geerlingguy/pi4gpu/PCIe bracket/PCIe_bracket_M3_hole.png

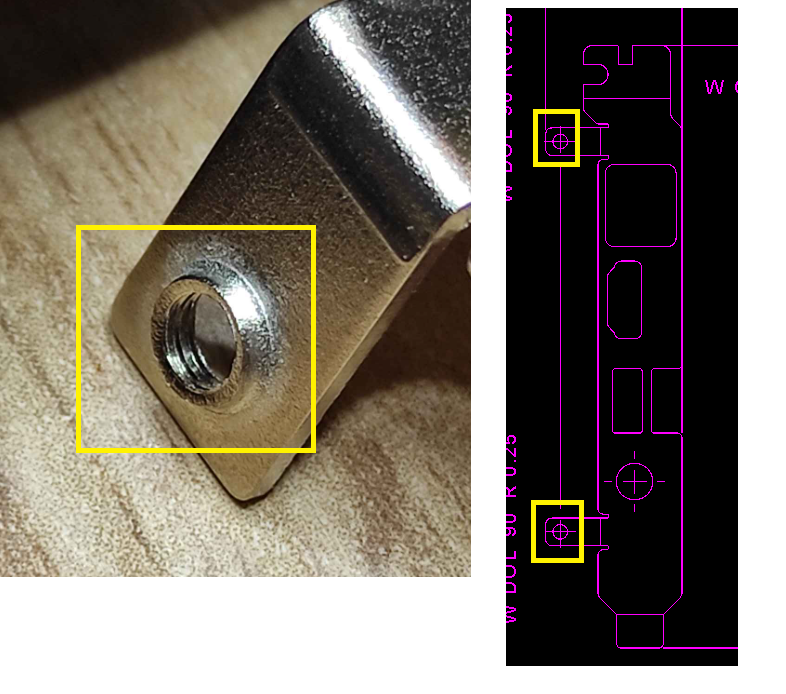
PCIe bracket/PCIe_bracket_M3_hole.png
