geerlingguy/pi4gpu/PCIe bracket/PCIe_missing_bending.png

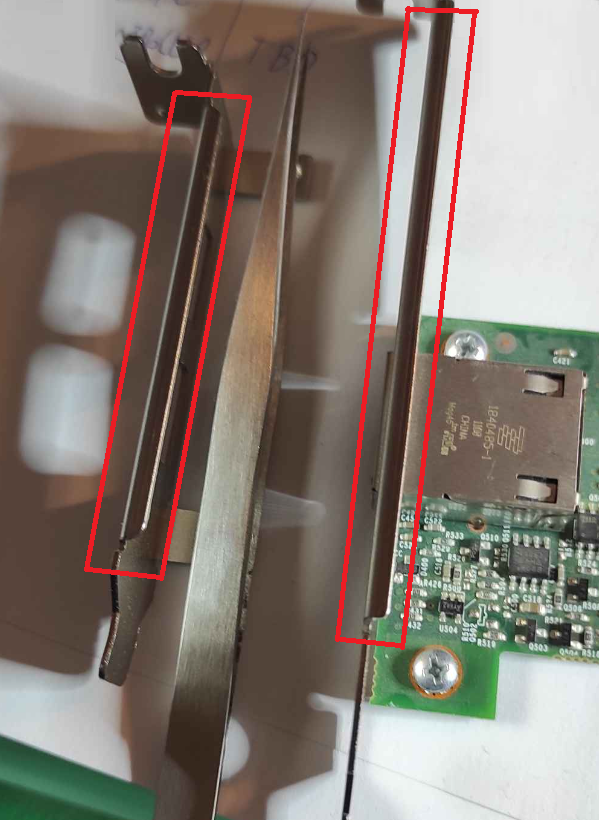
PCIe bracket/PCIe_missing_bending.png
