geerlingguy/pi4gpu/PCIe bracket/photo_2022-12-15_10-46-20.jpg

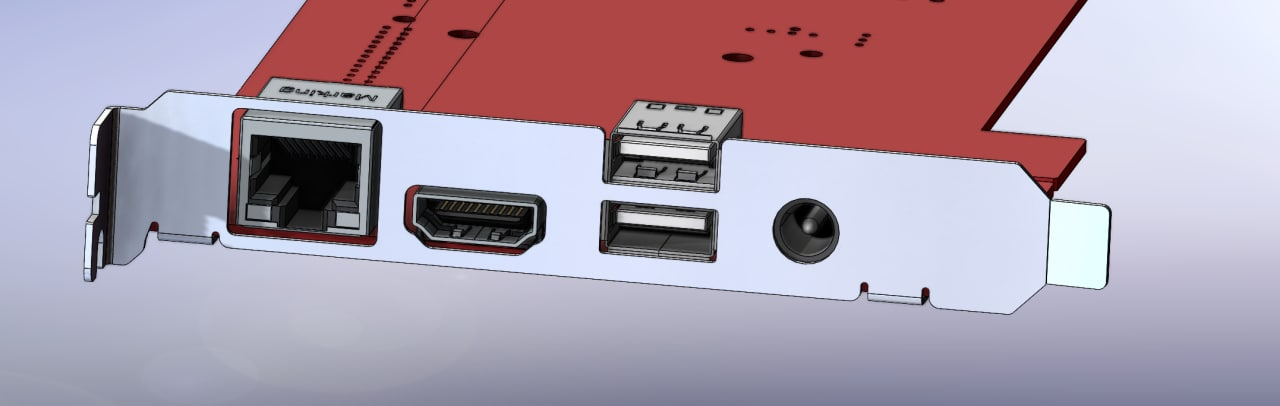
PCIe bracket/photo_2022-12-15_10-46-20.jpg
