geerlingguy/pi4gpu/renders/cm4_gpu1.png

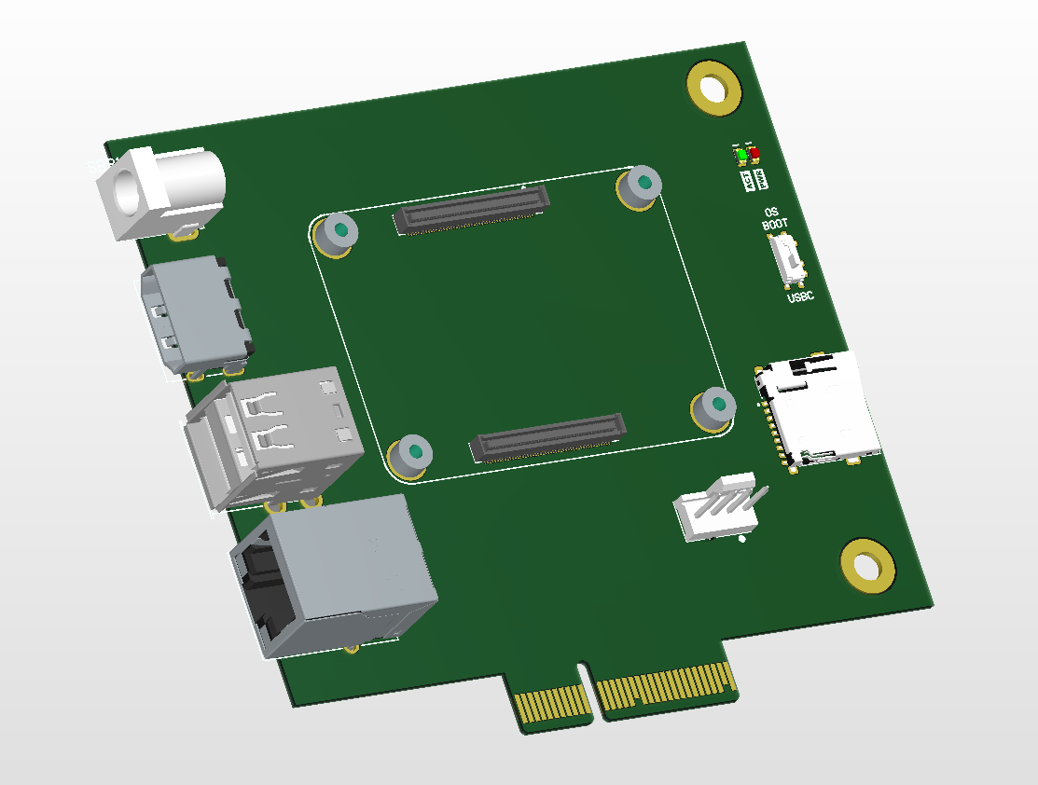
renders/cm4_gpu1.png
