geerlingguy/pi4gpu/renders/cm4_gpu2.png

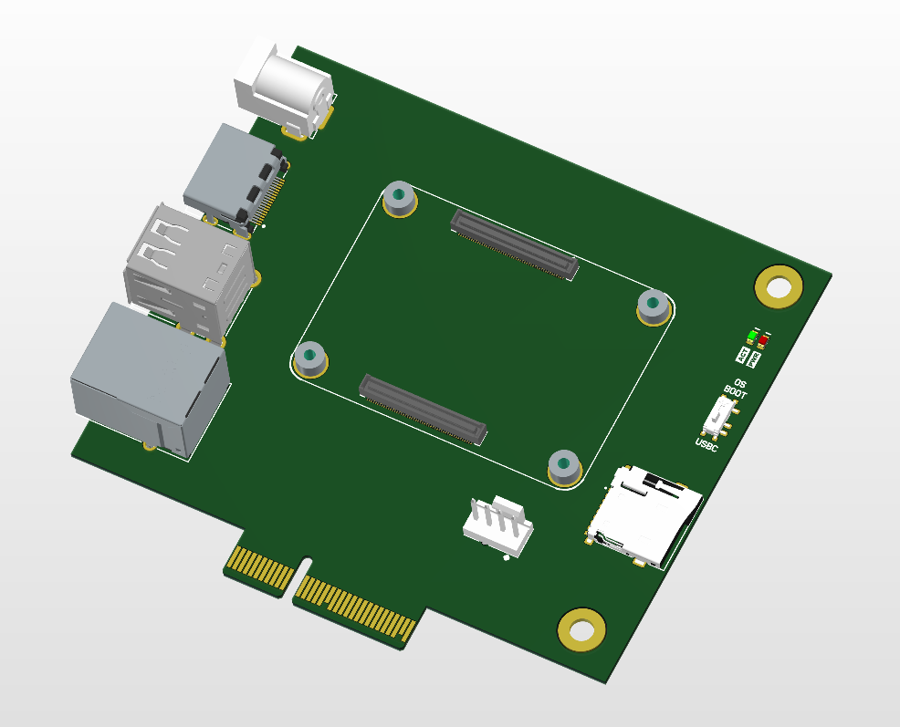
renders/cm4_gpu2.png
