geerlingguy/pi4gpu/renders/CM4GPU_PCB_20221031_01.png

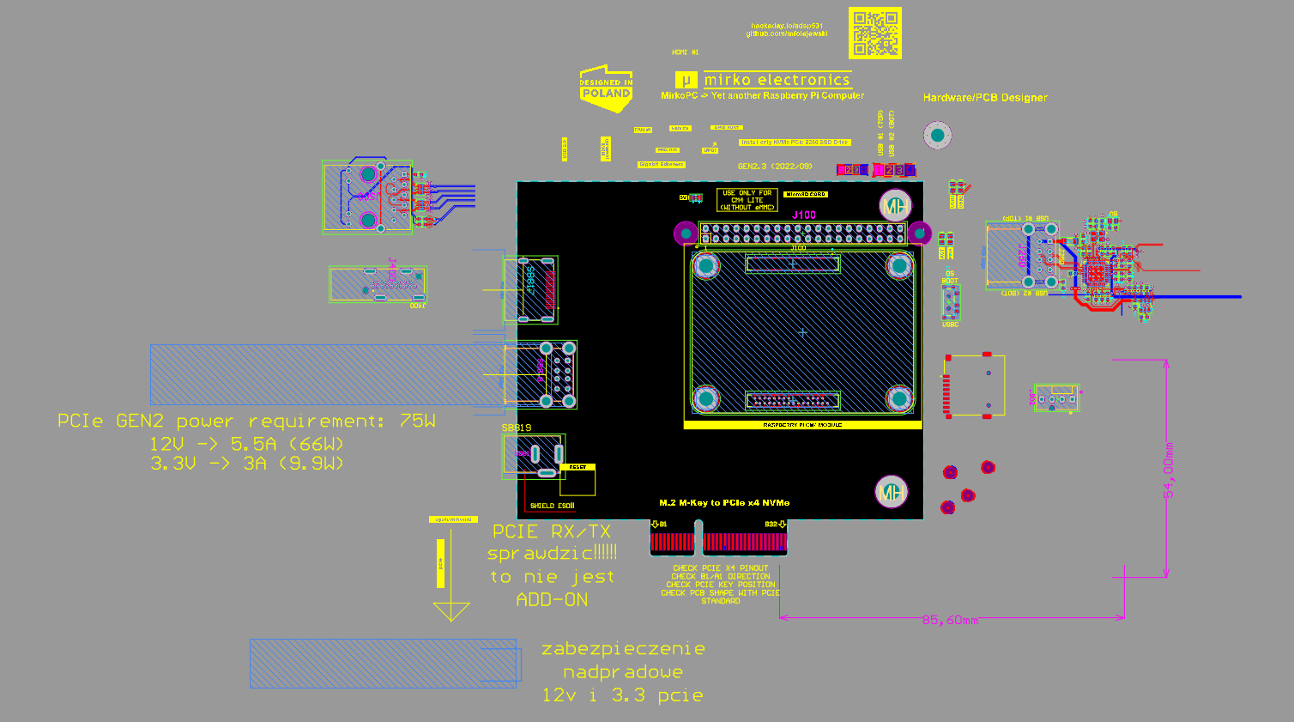
renders/CM4GPU_PCB_20221031_01.png
