geerlingguy/pi4gpu/renders/CM4GPU_PCB_20221103_01.png

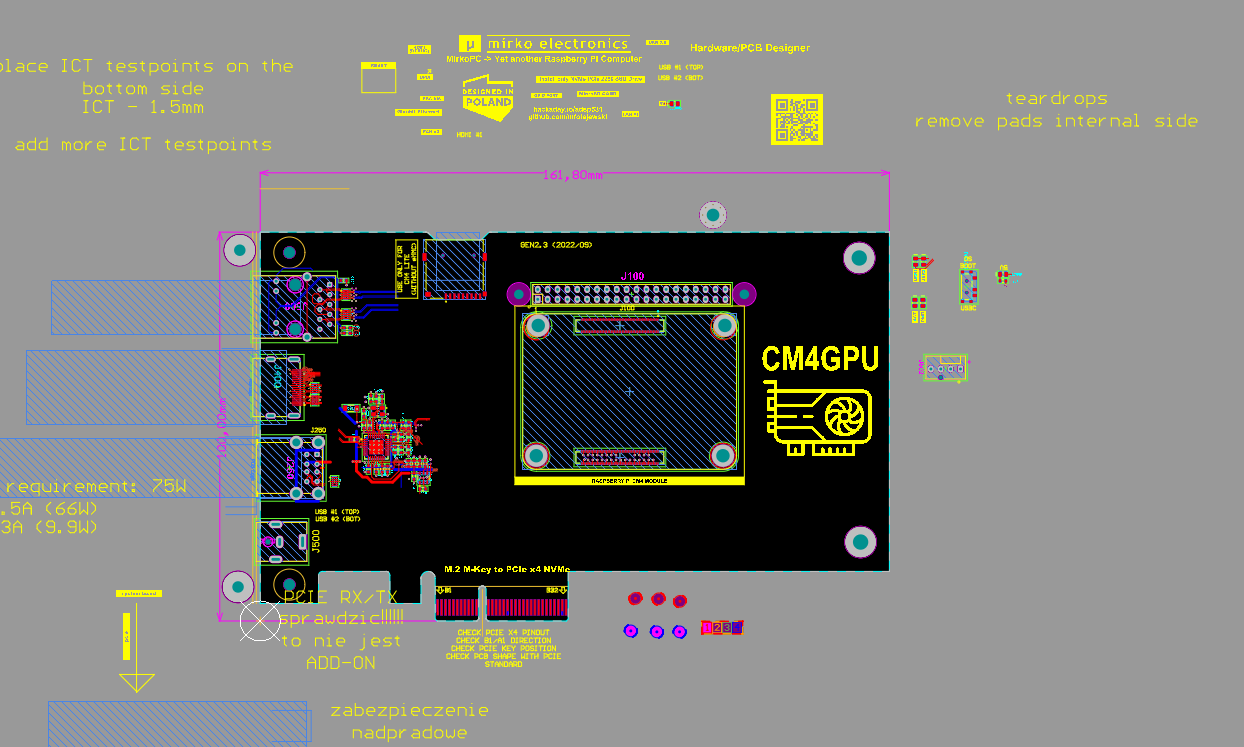
renders/CM4GPU_PCB_20221103_01.png
