geerlingguy/pi4gpu/renders/CM4GPU_PCB_20221110_01.png

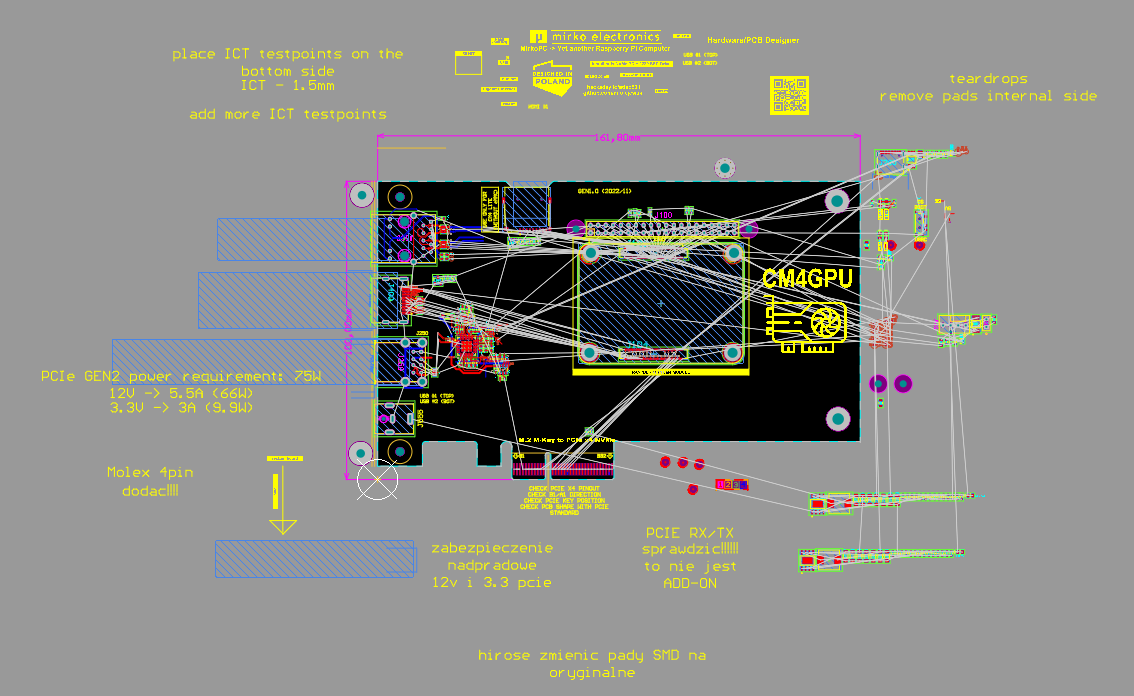
renders/CM4GPU_PCB_20221110_01.png
