geerlingguy/pi4gpu/renders/CM4GPU_PCB_20221114_04.png

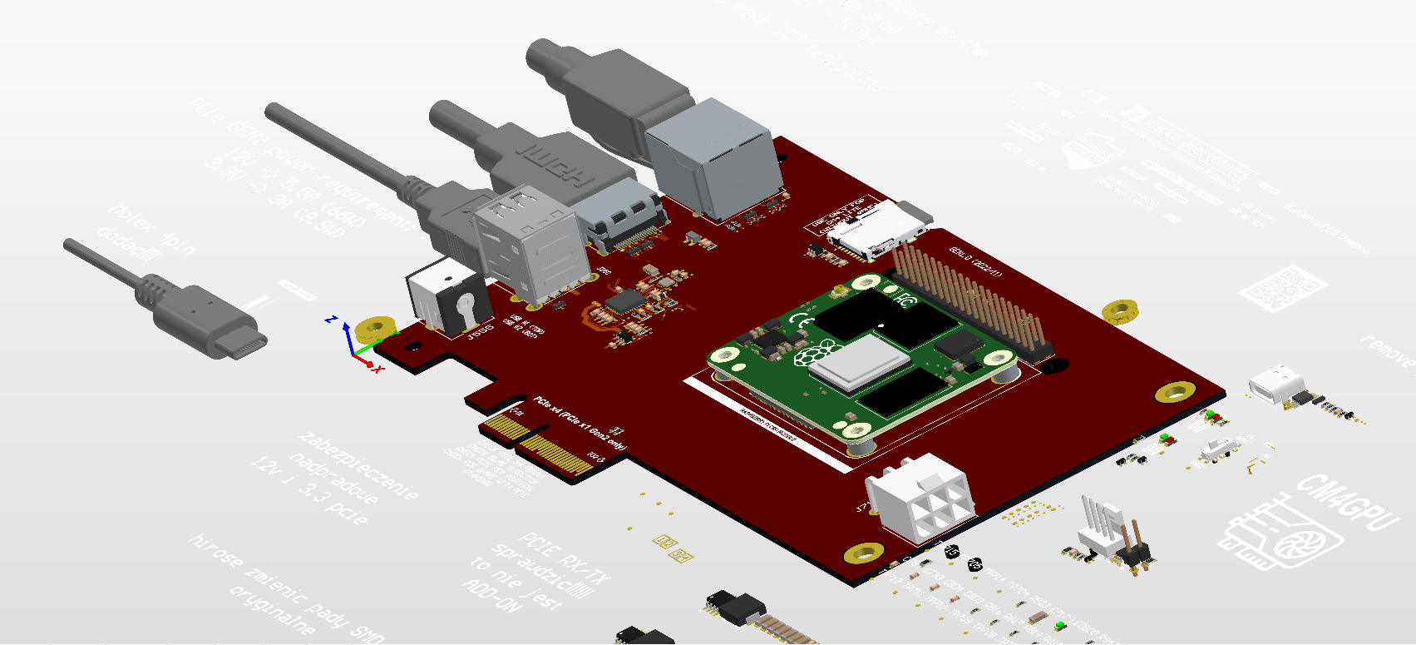
renders/CM4GPU_PCB_20221114_04.png
