geerlingguy/pi4gpu/renders/CM4GPU_PCB_20221117_03.png

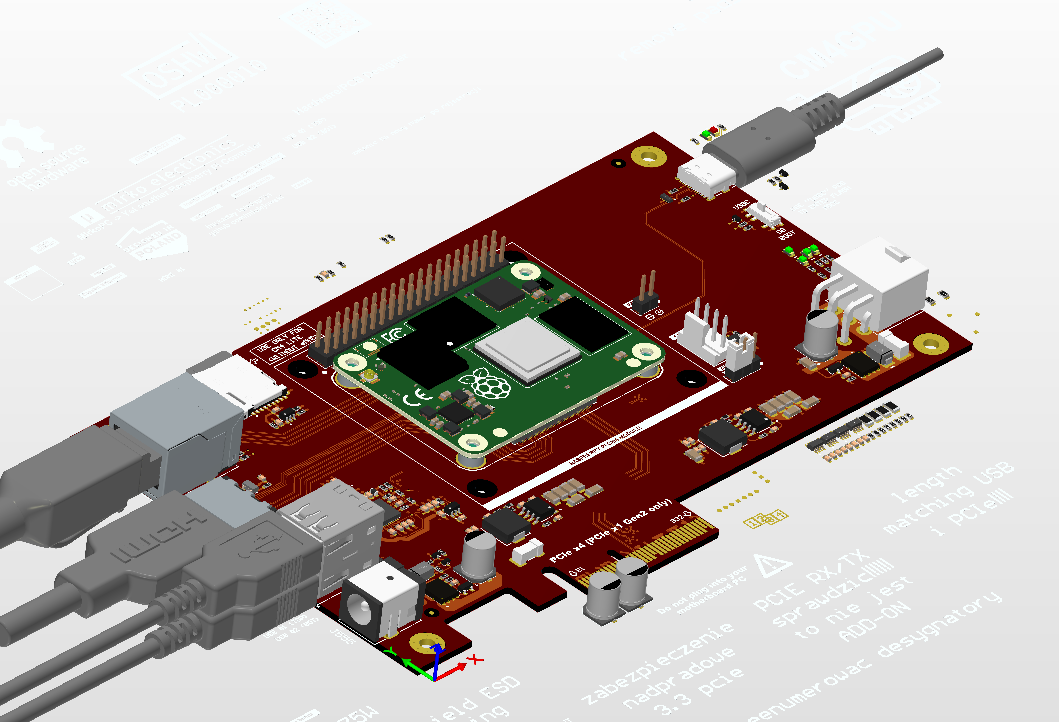
renders/CM4GPU_PCB_20221117_03.png
