geerlingguy/pi4gpu/renders/PCIE_adapter2.png

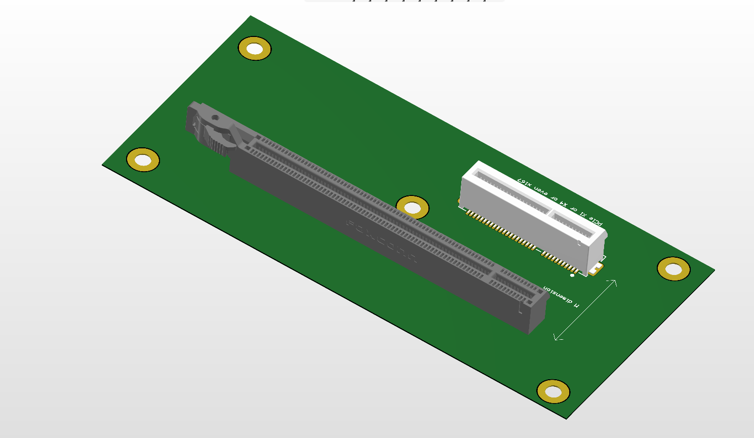
renders/PCIE_adapter2.png
