geerlingguy/pi4gpu/renders/PCIe_X4_X16_ADP_2.png

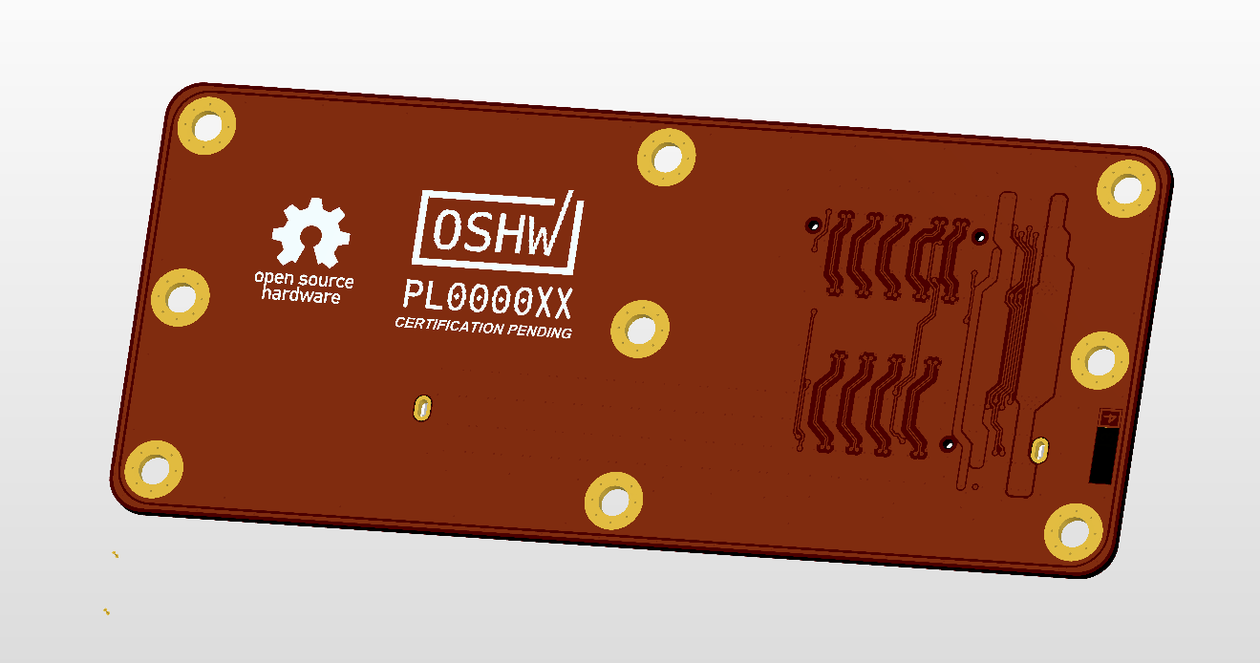
renders/PCIe_X4_X16_ADP_2.png
