geerlingguy/pi4gpu/renders/PCIe_X4_X16_ADP_4.png

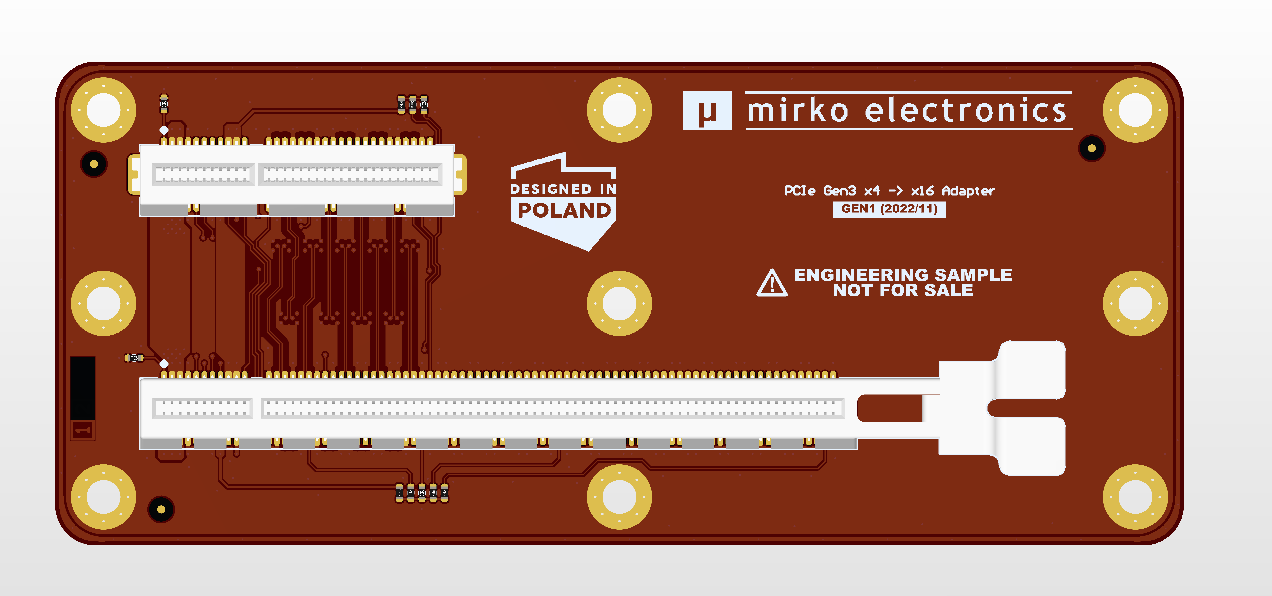
renders/PCIe_X4_X16_ADP_4.png
