geerlingguy/pi4gpu/renders/PCIe_X4_X16_ADP_5.png

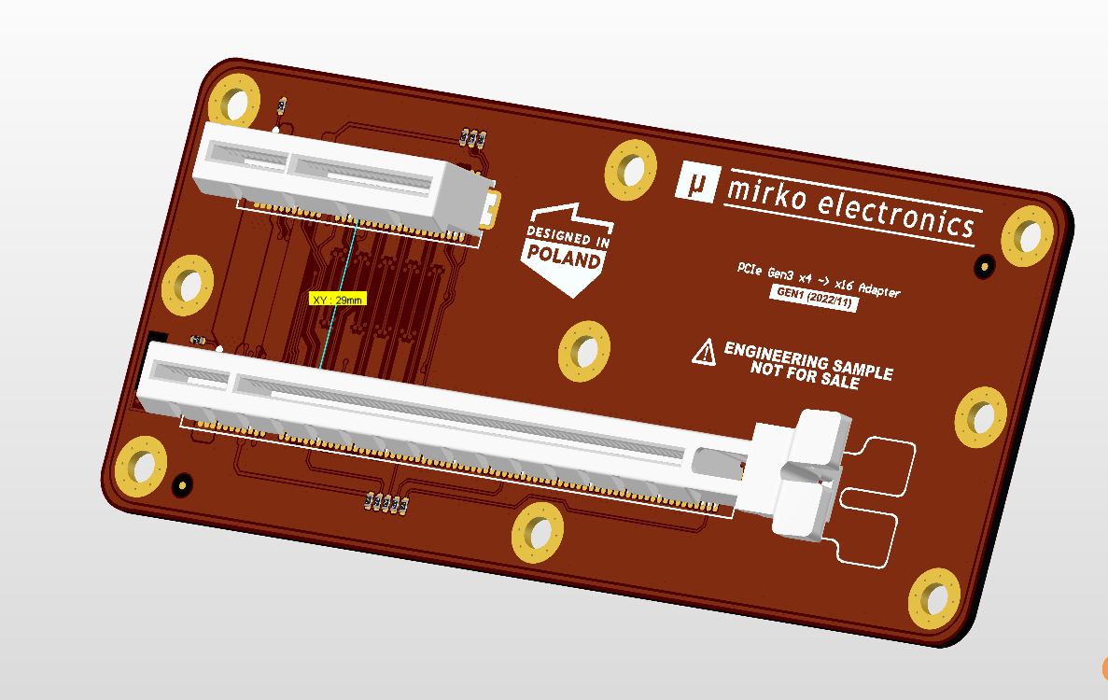
renders/PCIe_X4_X16_ADP_5.png
