geerlingguy/pi4gpu/renders/Pi4GPU_2022-11-21_4.png

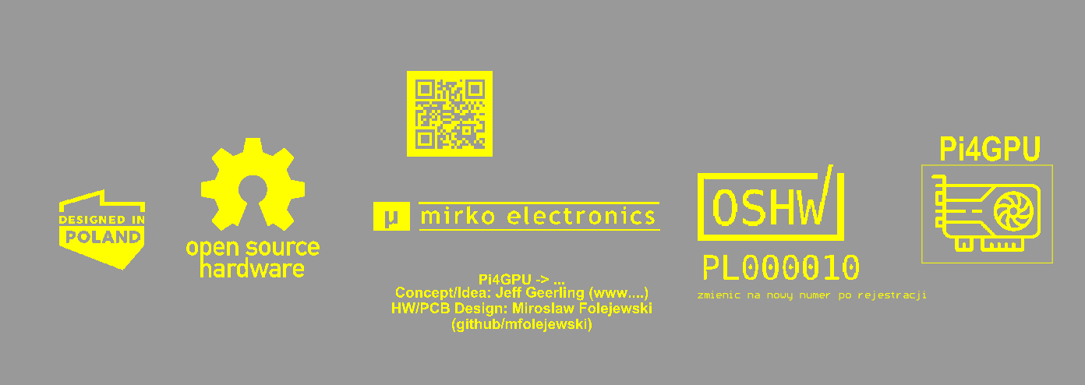
renders/Pi4GPU_2022-11-21_4.png
