geerlingguy/pi4gpu/renders/Pi4GPU_2022-11-23_2.png

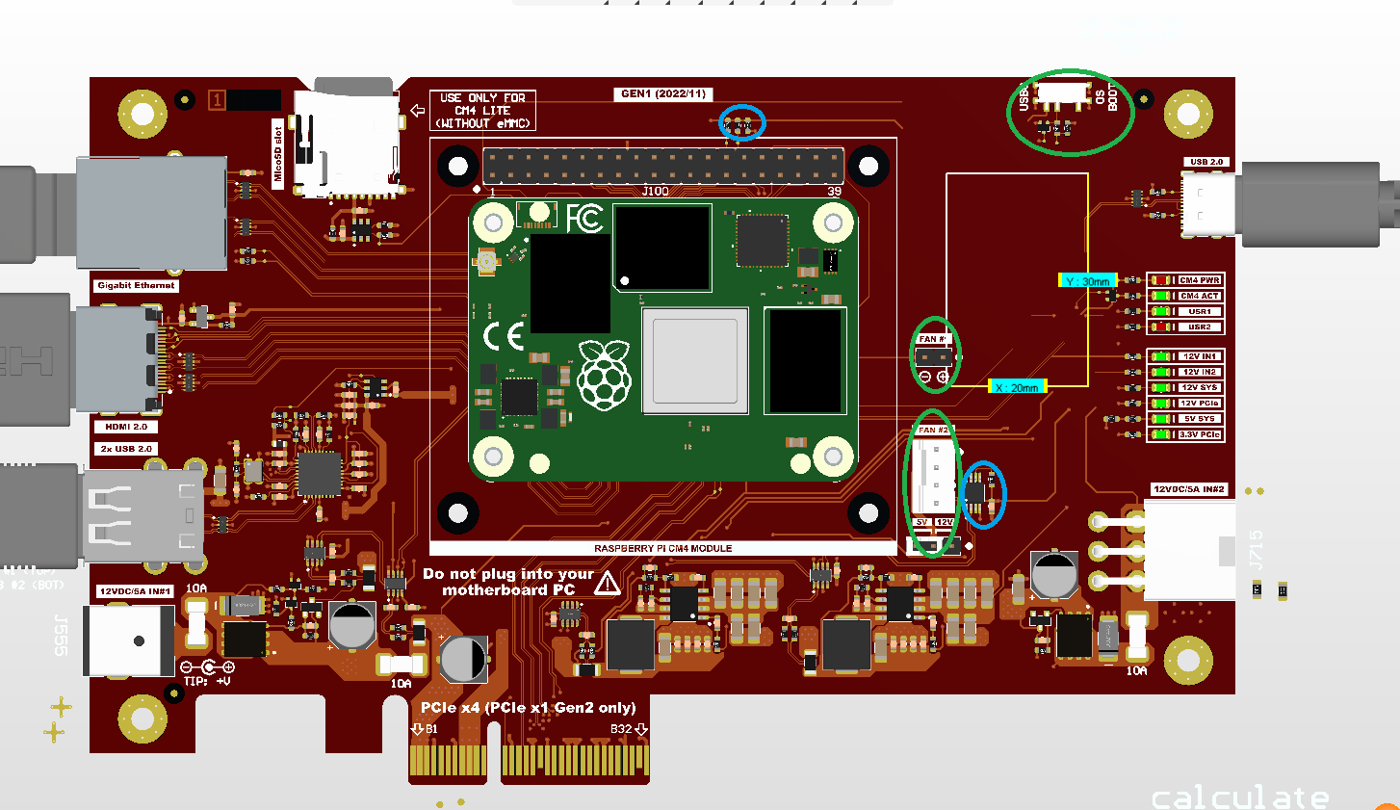
renders/Pi4GPU_2022-11-23_2.png
