geerlingguy/pi4gpu/renders/Pi4GPU_2022-11-24_7.png

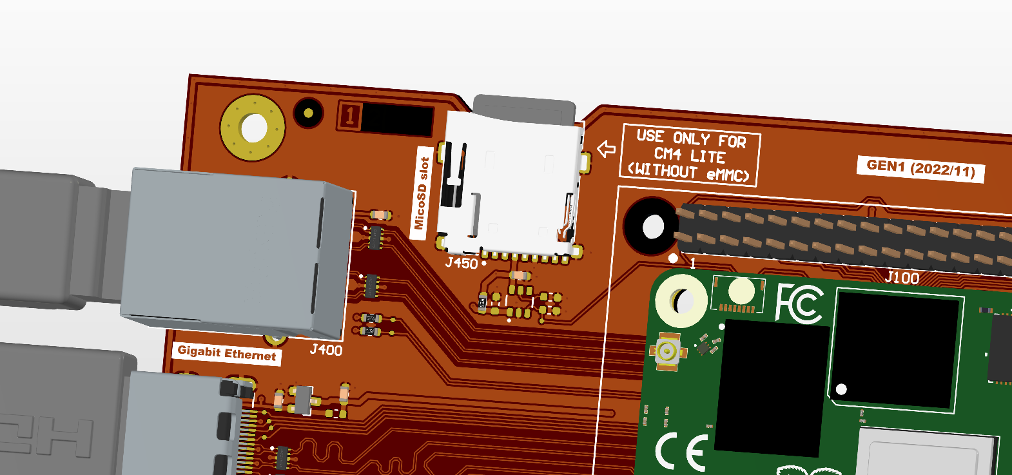
renders/Pi4GPU_2022-11-24_7.png
