geerlingguy/pi4gpu/renders/Pi4GPU_2022-11-29_1.png

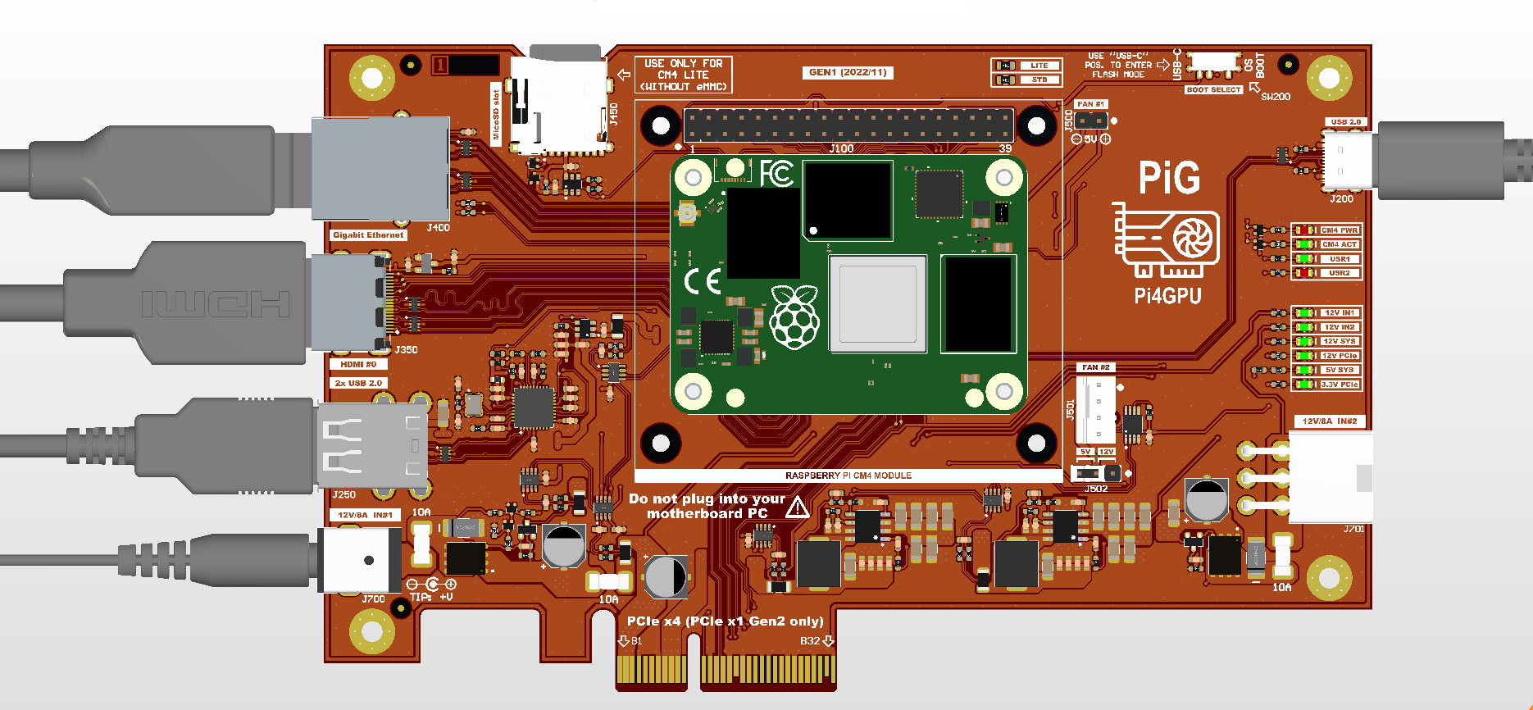
renders/Pi4GPU_2022-11-29_1.png
