geerlingguy/pi4gpu/renders/Pi4GPU_2022-11-29_6.png

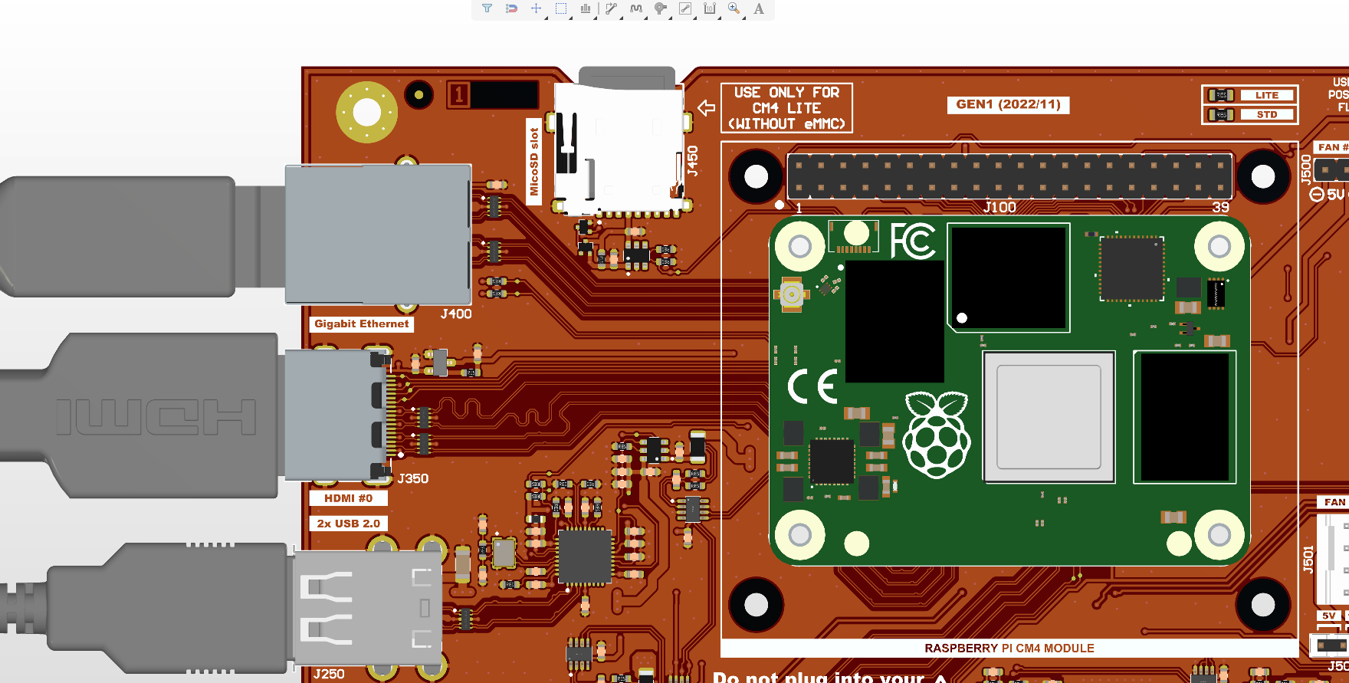
renders/Pi4GPU_2022-11-29_6.png
