geerlingguy/pi4gpu/renders/Pi4GPU_2022-12-03_1.png

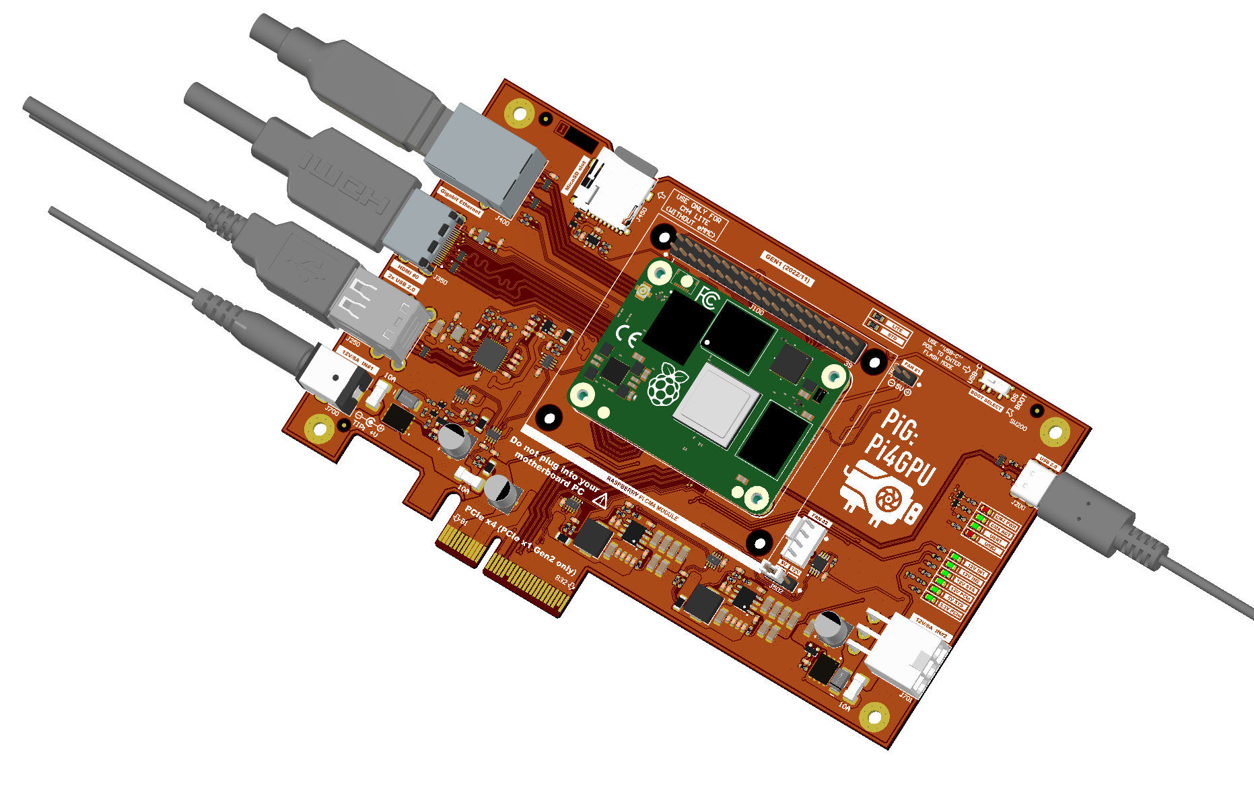
renders/Pi4GPU_2022-12-03_1.png
