geerlingguy/pi4gpu/renders/Pi4GPU_v2_2023-04-13_2.png

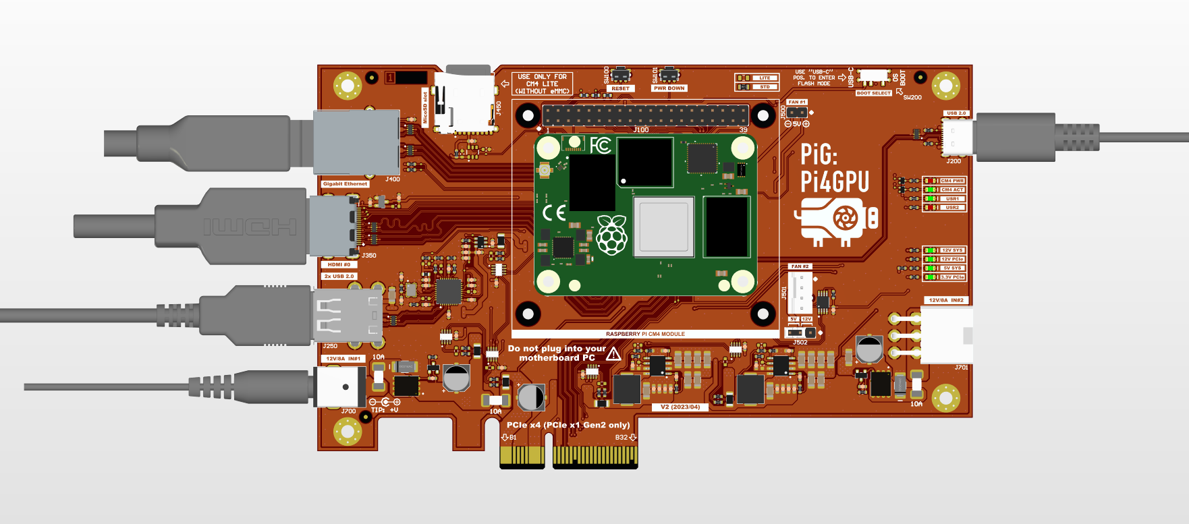
renders/Pi4GPU_v2_2023-04-13_2.png
