geerlingguy/pi4gpu/renders/Pi4GPU_v2_2023-04-13_4.png

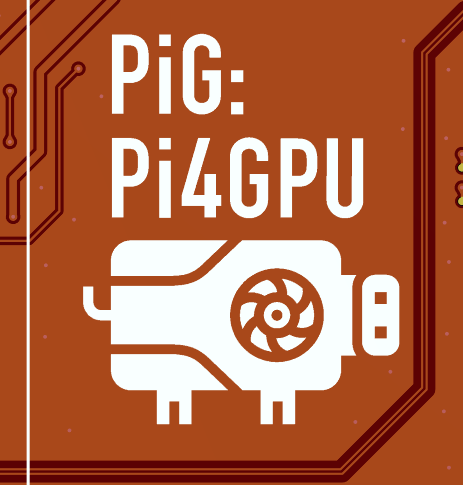
renders/Pi4GPU_v2_2023-04-13_4.png
