geerlingguy/pi4gpu/source files (PCB)/v2/pcb_stackup.png

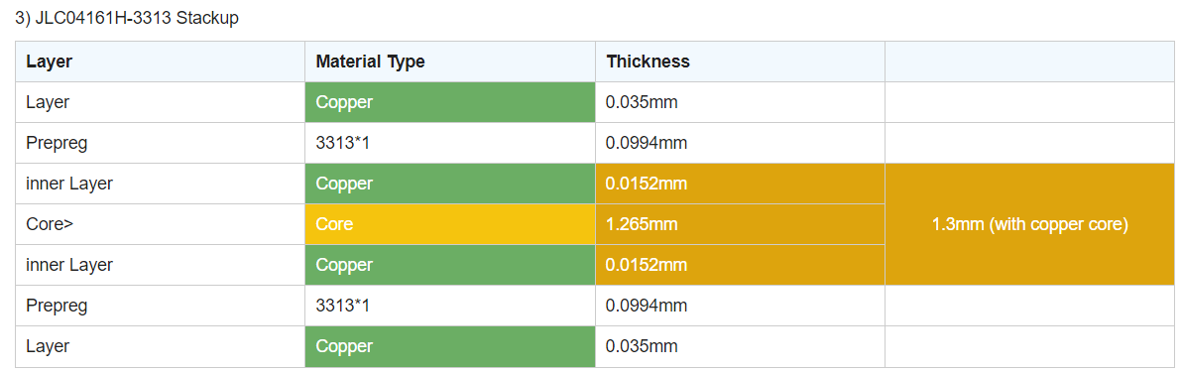
source files (PCB)/v2/pcb_stackup.png
