geerlingguy/pi4gpu/issues/HW_PCB_issues_v1.png

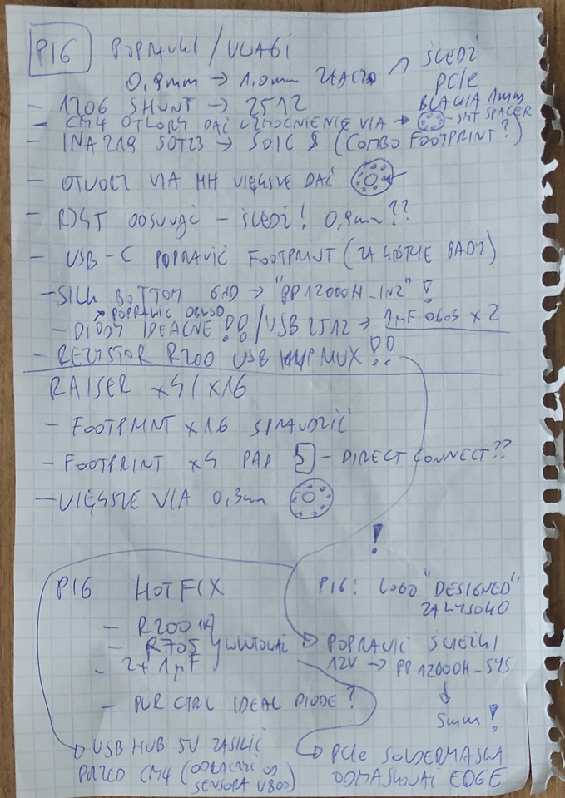
issues/HW_PCB_issues_v1.png
