geerlingguy/pi4gpu/schematics/deprecated/Pi4GPU_(PiG)_v1_Schematic_2022-12-03.pdf

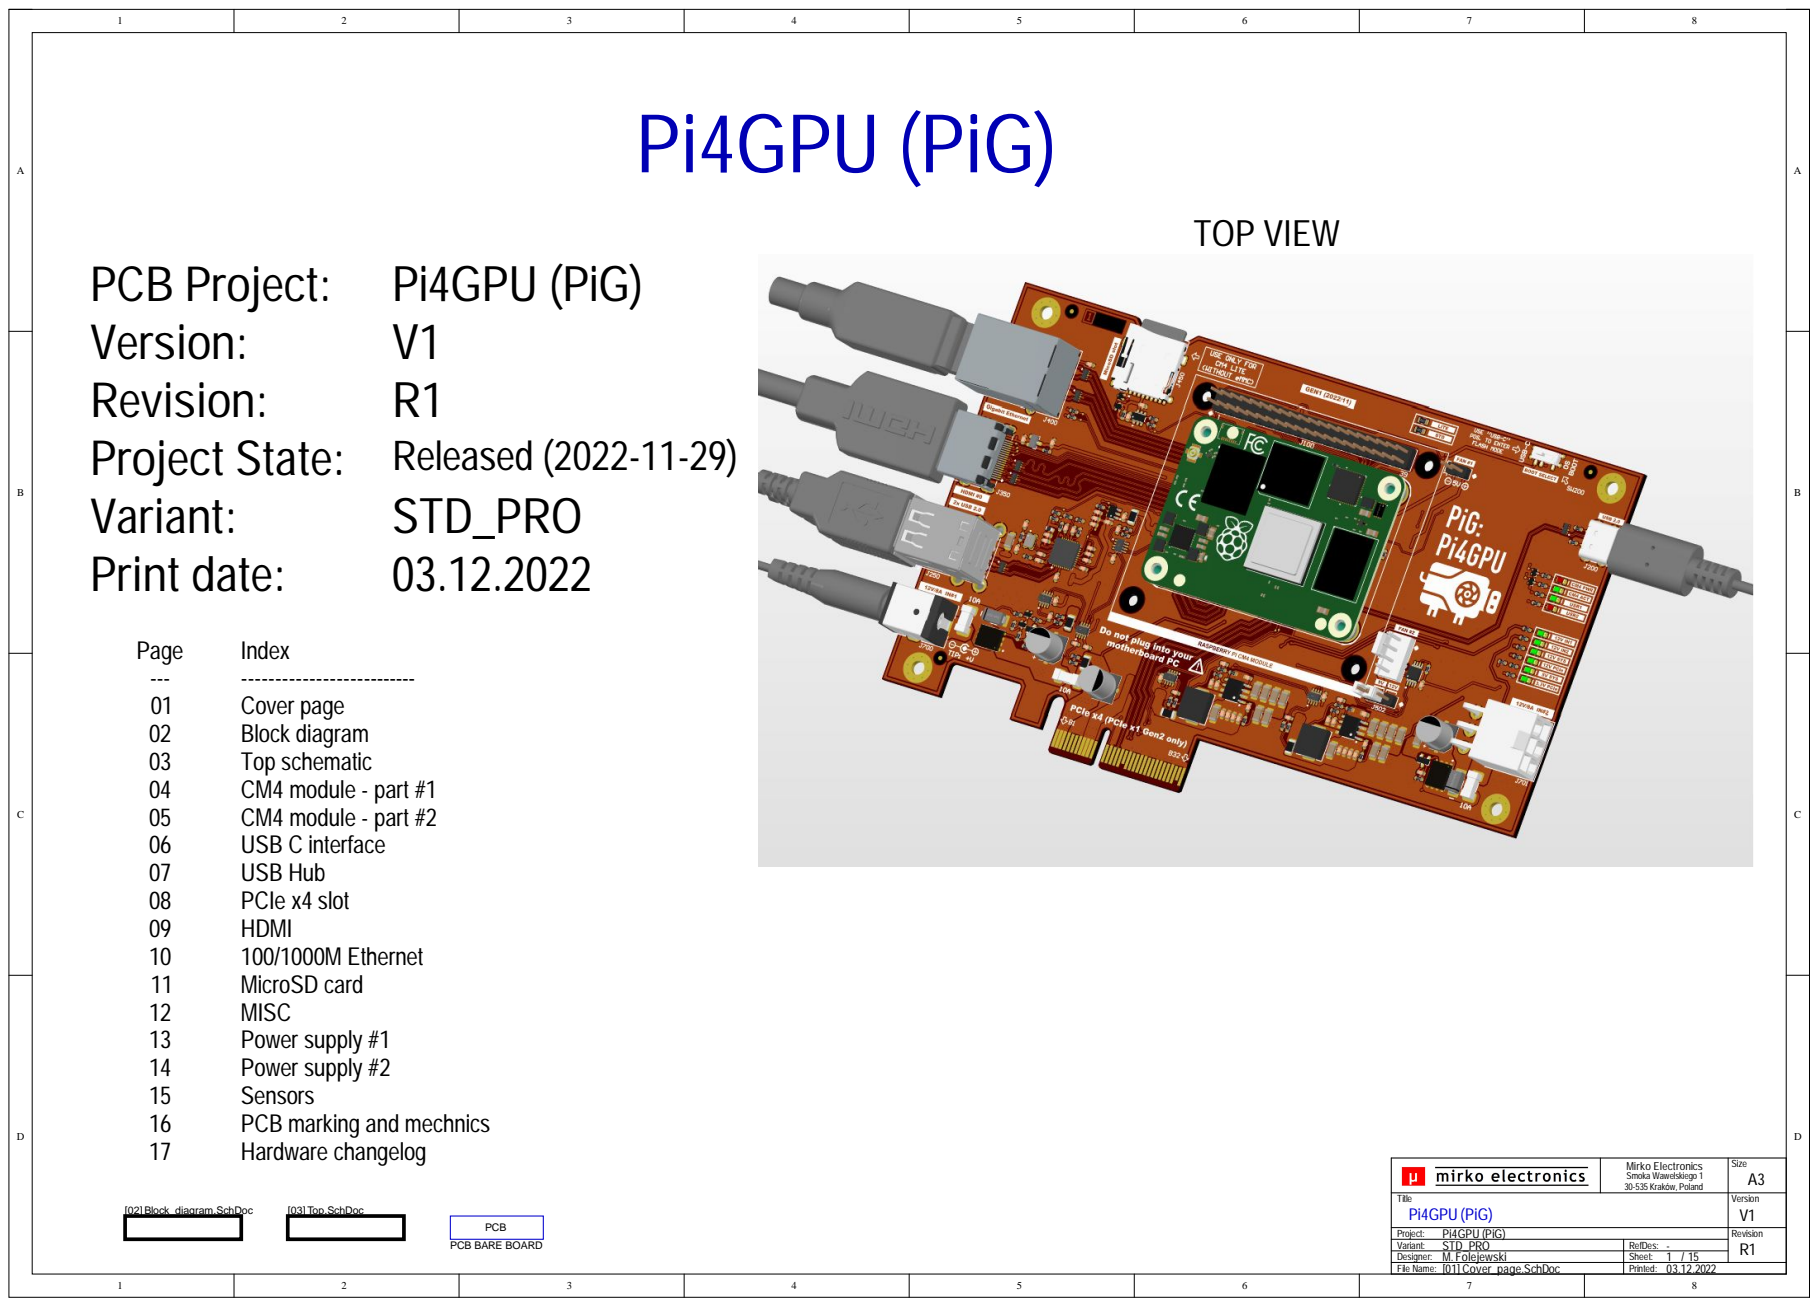
[picture p160: page 1]

Mirko Electronics Smoka Wawelskiego 1 30-535 Kraków, Poland | Size A3

Title Pi4GPU (PiG) | | Version V1

Project: Pi4GPU (PiG) | | Revision R1
Variant: STD_PRO | RefDes: -
Designer: M. Folejewski
File Name: [01] Cover_page.SchDoc | Printed:

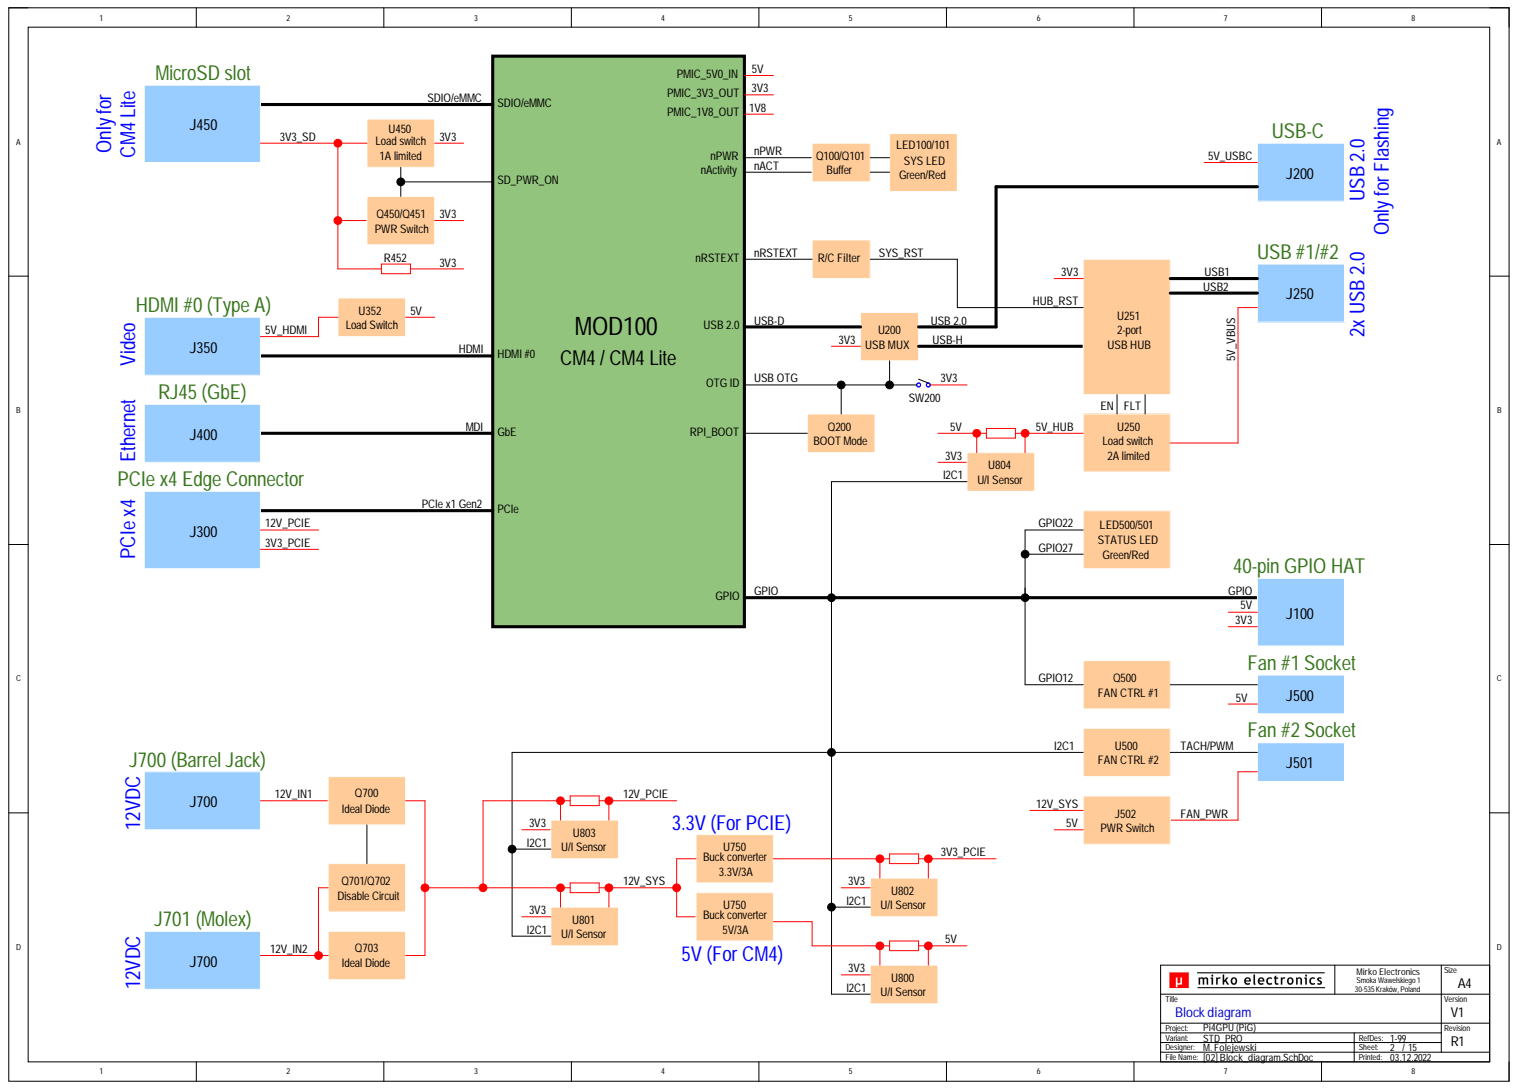
[picture p161: page 2]

SDIO/eMMC

Mirko Electronics Smoka Wawelskiego 1

Title Block diagram | Version V1

Project: Pi4GPU (PiG) | Revision R1
Variant: STD_PRO | RefDes: 1-99


Mirko Electronics Smoka Wawelskiego 1 30-535 Kraków, Poland | Size A4

Title Top schematic | | Version V1

Project: Pi4GPU (PiG) | | Revision R1
Variant: STD_PRO | RefDes: 1-99

Sheet: 3 15 /

File Name: [03] TOP.SchDoc | Printed: 03.12.2022

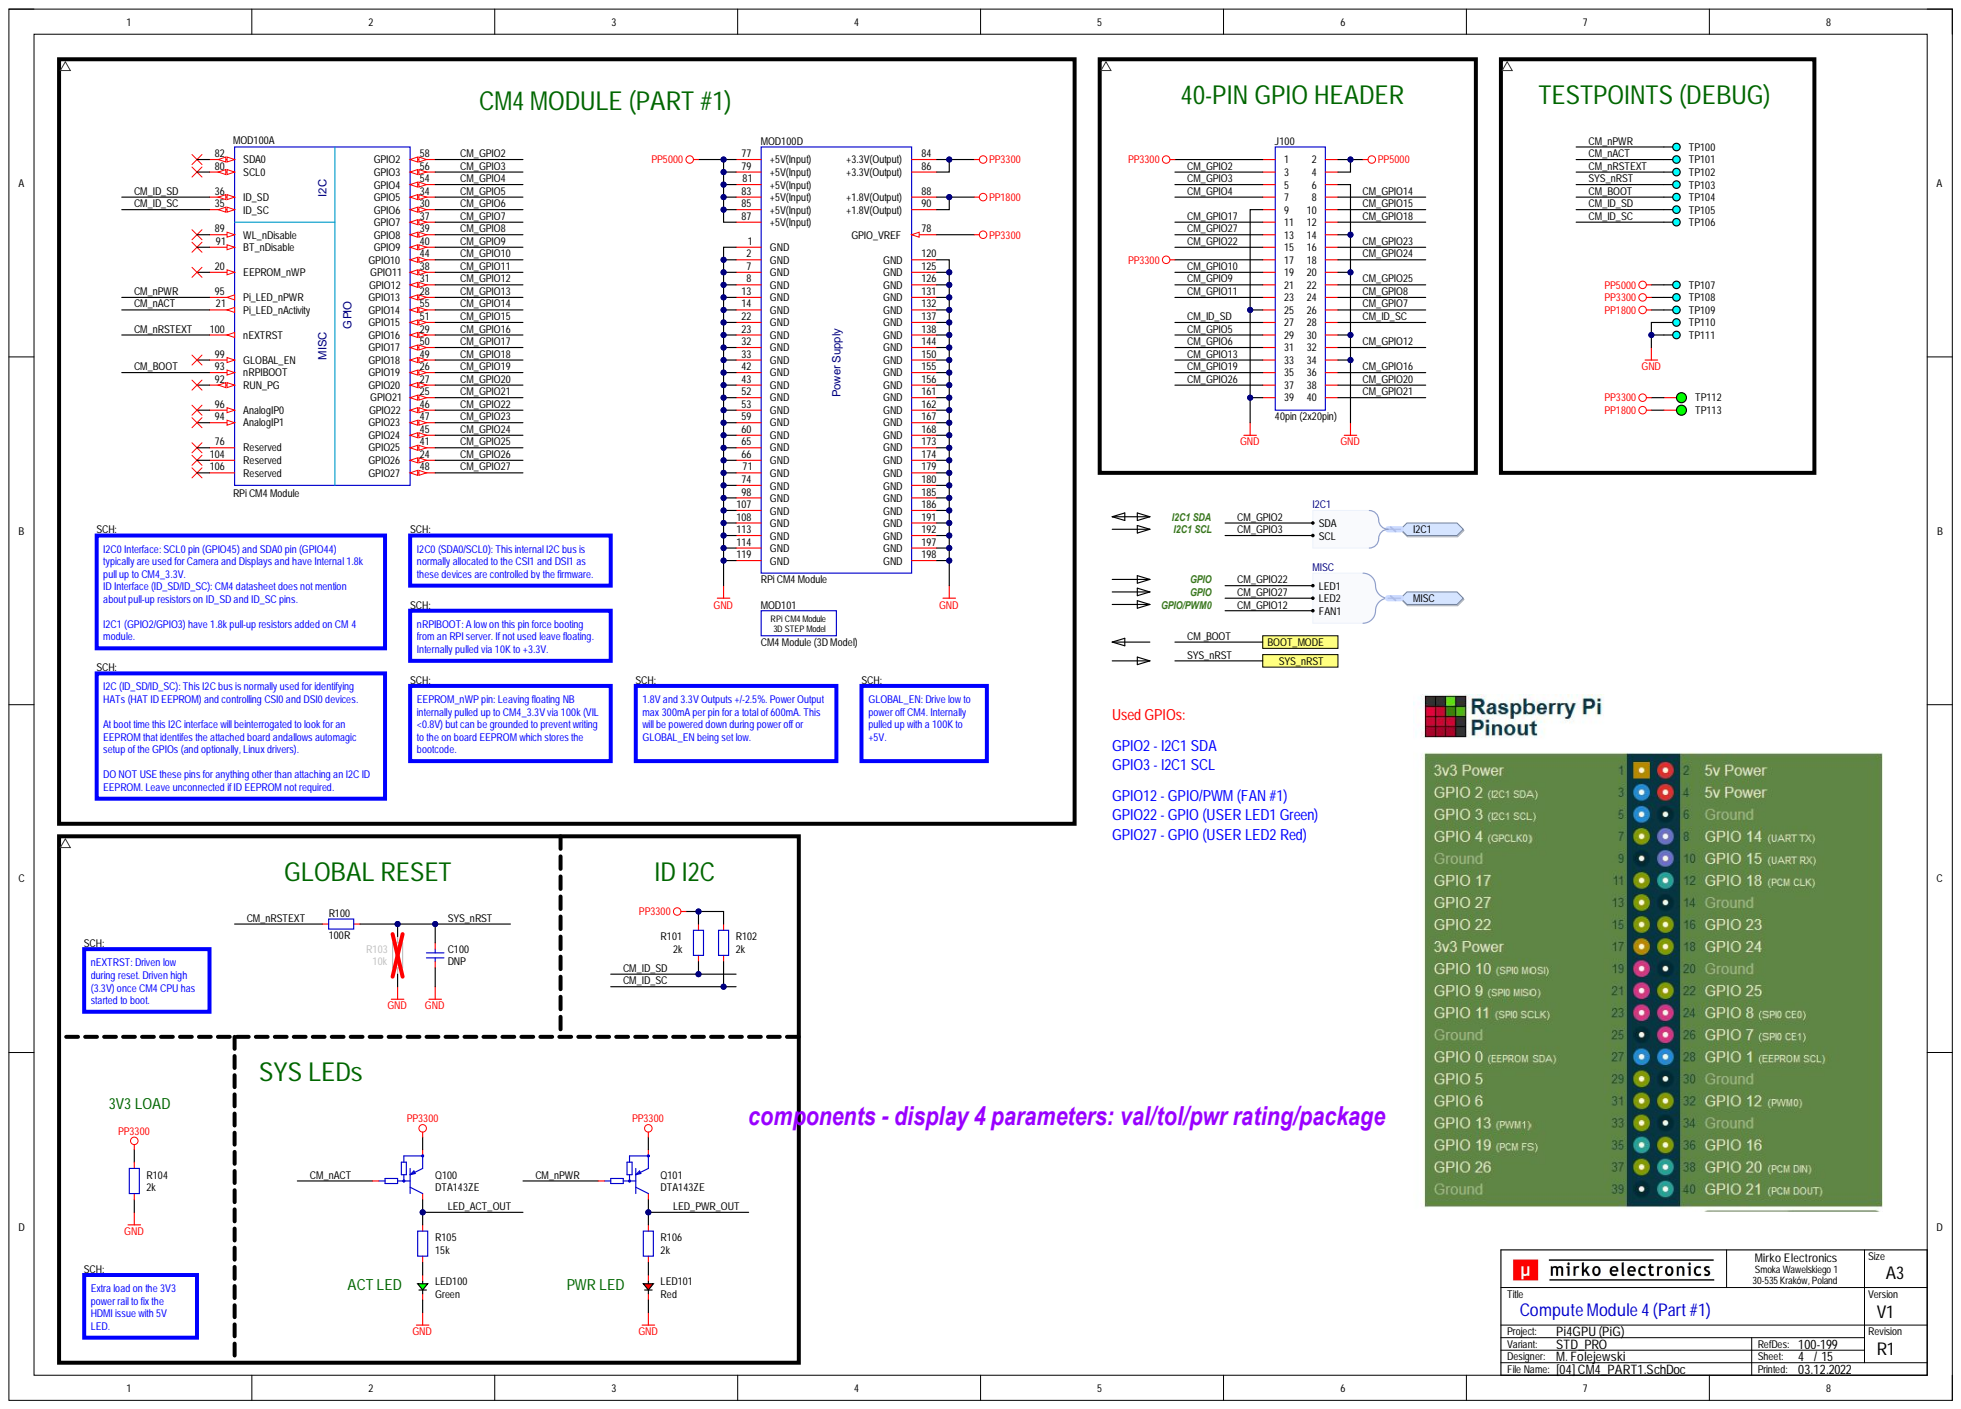
[picture p162: page 4]

85 | 90
87 | 7 8

1 3 | 1 31
1 4 | 1 32
22 | 1 37

23 | 1 38
32 | 1 44

1 07 | 1 86
1 08 | 1 91
1 1 3 | 1 92

GPIO27 - GPIO (USER LED2 Red) I2C1 SDA I2C1 SCL

Mi r k o E l ec tro n i cs Smoka Wawelskiego 1 30-535 Kra kó w, Pol a nd | S i z e A 3

T i tl e C o m p u te Mod ule 4 (Part #1) | | Versi on V1

Proj ect: P i 4G P U (P i G ) | | R evi s i on R 1
Vari a n t: S T D_P R O | R efDes : 1 00-1 99
Des i g ner: M. F o l ej ews ki | S hee t: 4 / 1 5
F i l e N ame : [04] C M4_PA R T 1 . S ch Doc | Pri n ted : 03. 1 2. 2022

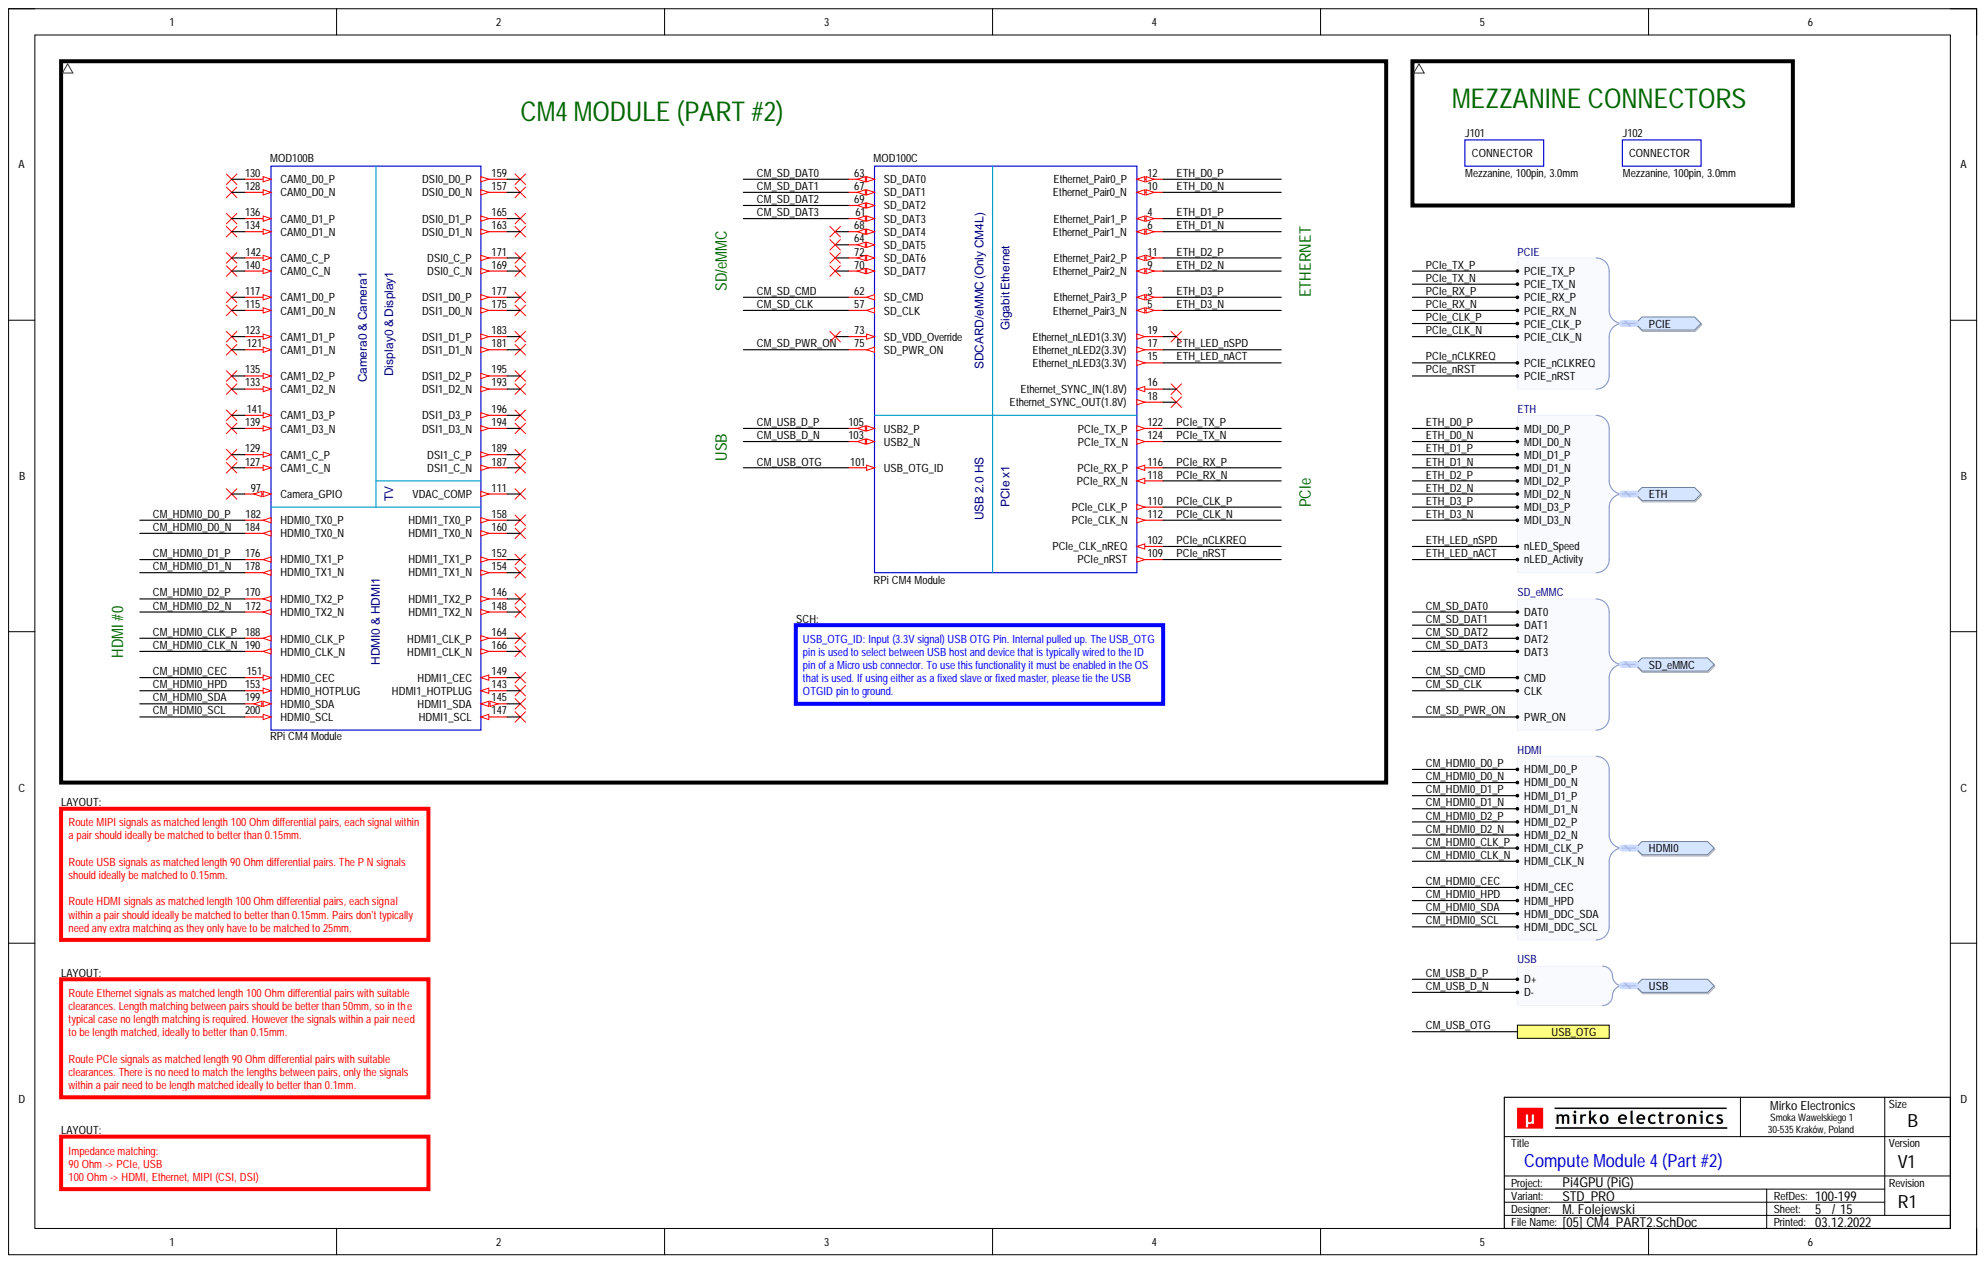
[picture p163: page 5]

SDCARD/eMMC(Only CM4L) USB 2.0 HS

(3.3V signal
Input
to select between USB host and device
Micro usb connector. To use
is used.
OTG

rs, each signal withi

Route USB signals as
should

Route HDMI signals as
within a pai
need any extra

Route Ethernet signals as
clearances. Length
typical case no

fferential pai
than 50mm, so
the signals within a pai

Route PCIe signals as
clearances. There

Project: Pi4GPU (Pi G ) | Revision R1
Variant: STD_PRO | RefDes: 100-199
Designer: M. Folejewski | Sheet:
Fi le Name: [05] CM4_PART2.SchDoc | Printed:

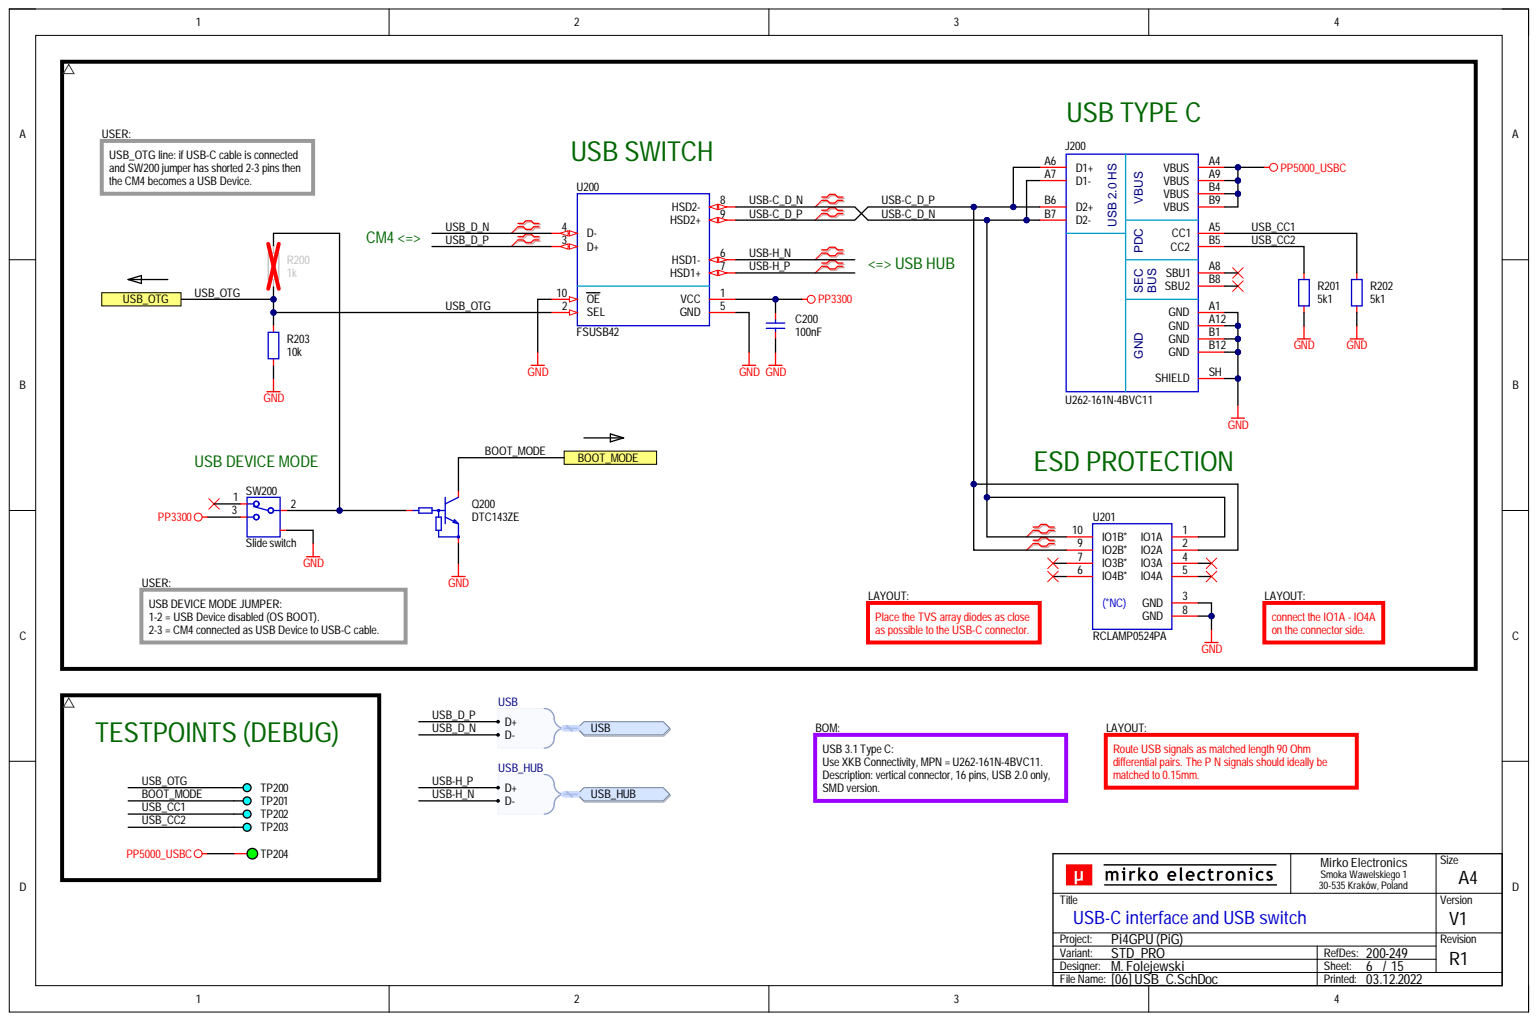
[picture p164: page 6]

USER:
USB_OTG line: if USB-C cable is connected
and SW200 jumper has shorted 2-3 pins then
the CM4 becomes a USB Device.

GND VBUS PDC SEC

USB DEVICE MODE JUMPER:
1-2 = USB Device disabled (OS BOOT).
2-3 = CM4 connected as USB Device to USB-C cable.

Place the TVS array diodes as close
as possible to the USB-C connector.

connect the IO1A - IO4A
on the connector side.

BOM:
USB 3.1 Type C:
Use XKB Connectivity, MPN = U262-161N-4BVC11.
Description: vertical connector, 16 pins, USB 2.0 only,
SMD version.

LAYOUT:
Route USB signals as matched length 90 Ohm
differential pairs. The P N signals should ideally be
matched to 0.15mm.

Mirko Electronics Smoka Wawelskiego 1 30-535 Kraków, Poland | Size A4

Title USB-C interface and USB switch | | Version V1

Project: Pi4GPU (PiG) | | Revision R1
Variant: STD_PRO | RefDes: 200-249

File Name: [06] USB_C.SchDoc | Printed:

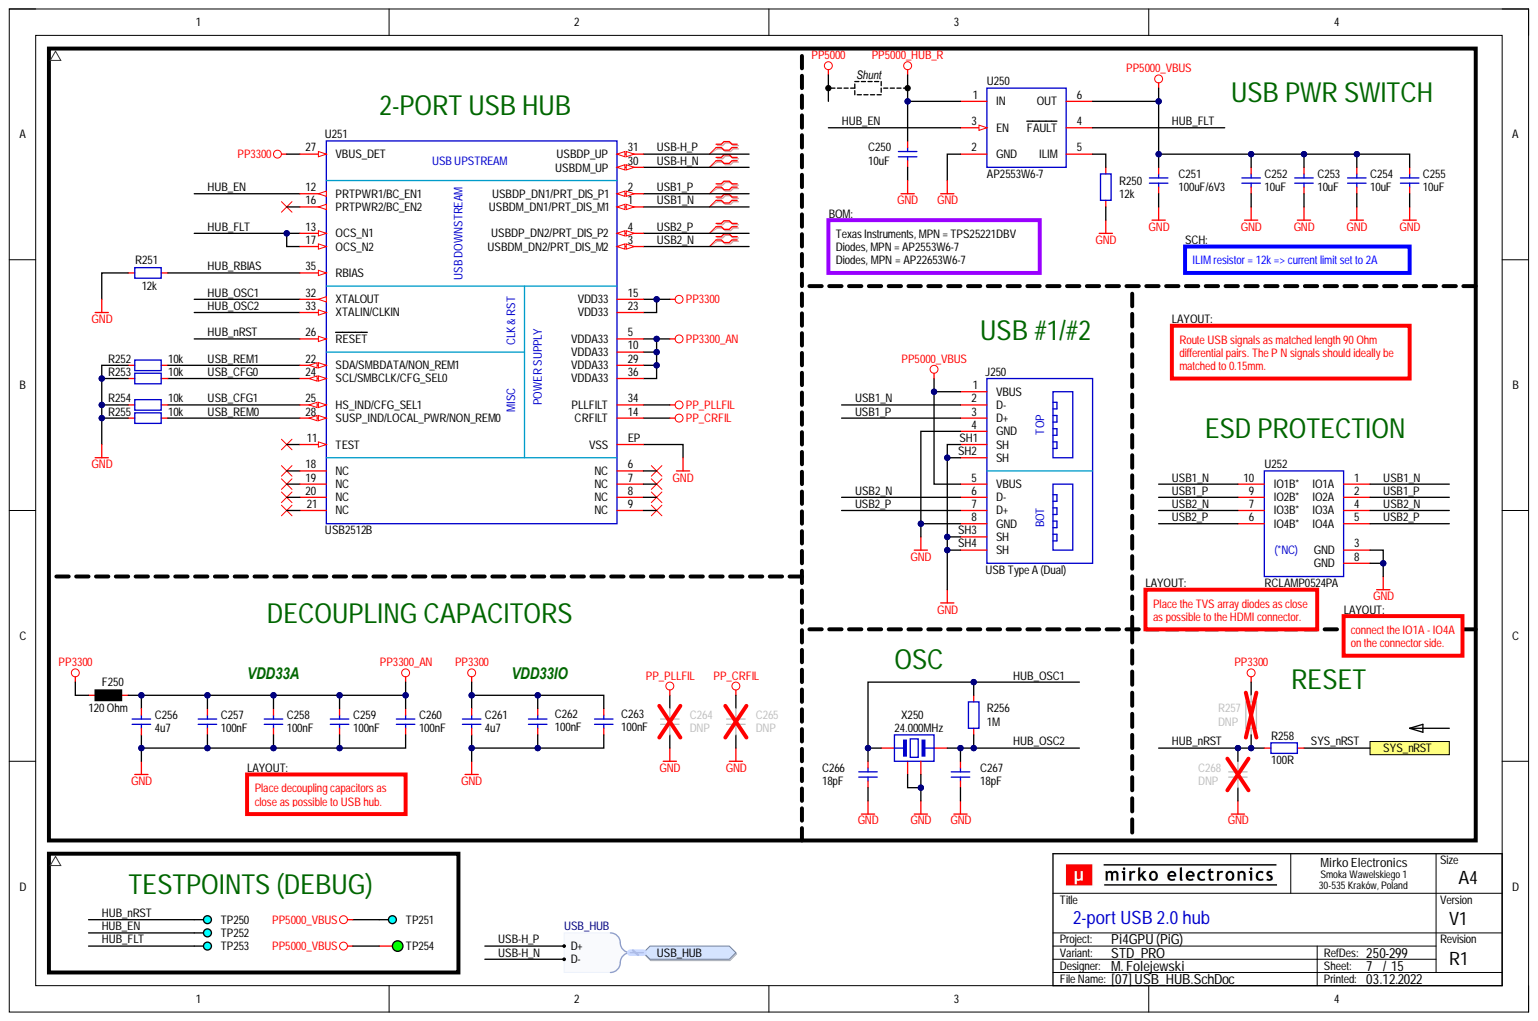
[picture p165: page 7]

SCH:
ILIM resistor = 12k => current limit set to 2A

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

D+ 3 D- 2 GND 4

Place the TVS array diodes as close
as possible to the HDMI connector.

Place decoupling capacitors as
close as possible to USB hub.

Mirko Electronics Smoka Wawelskiego 1

File Name: [07] USB_HUB.SchDoc | Printed:

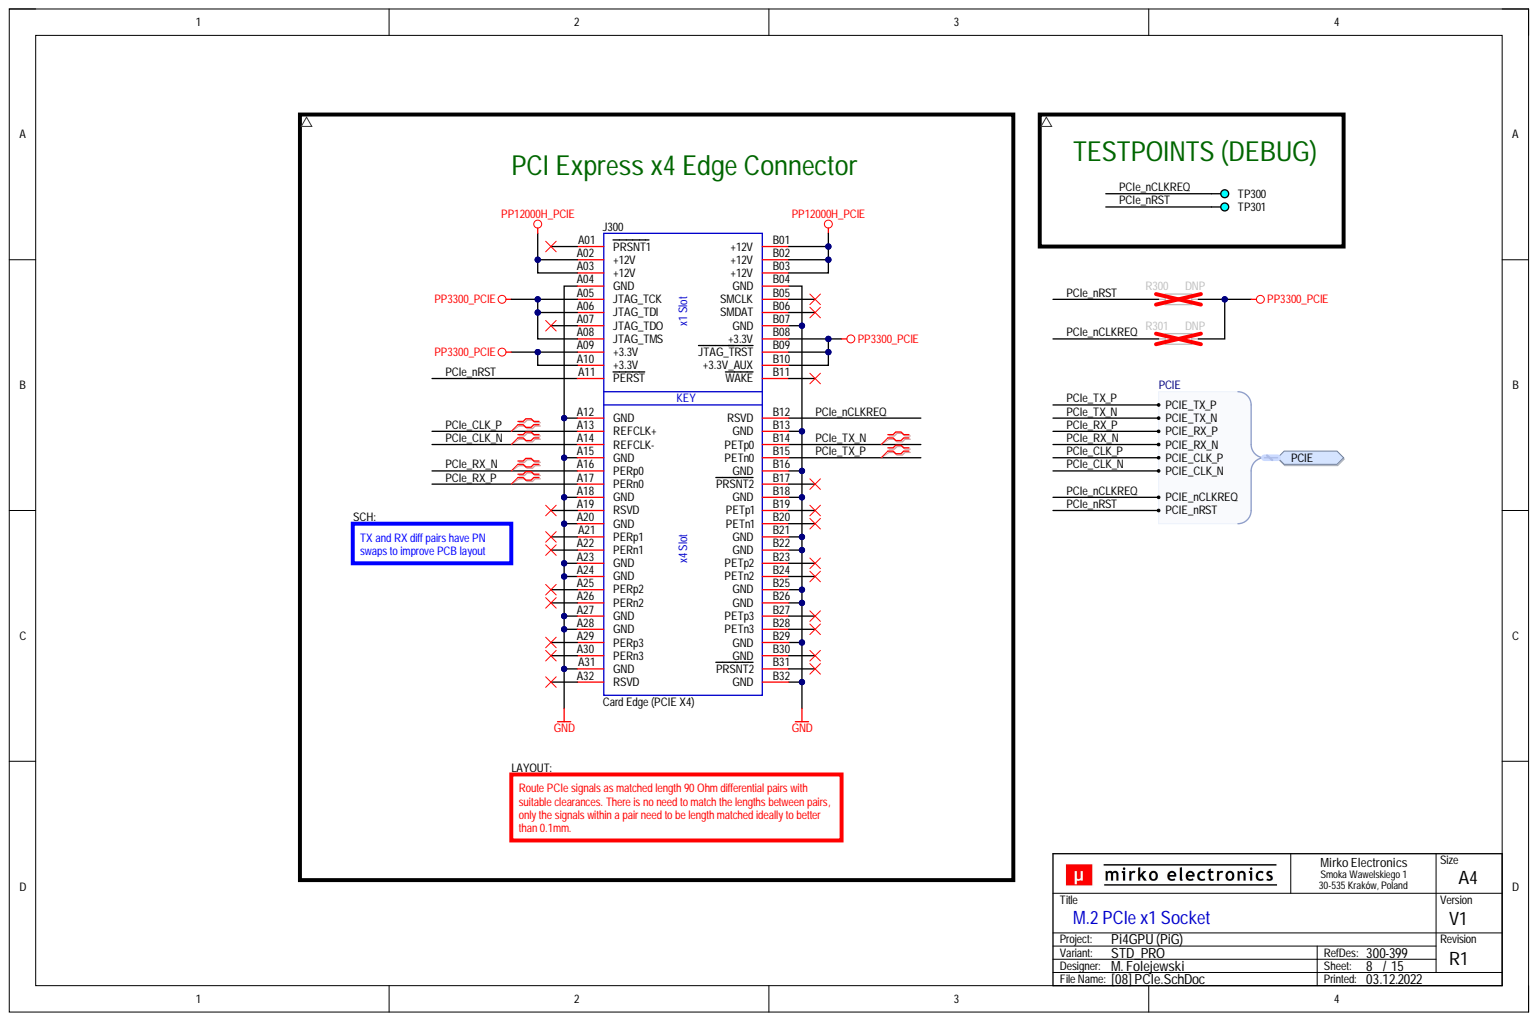
[picture p166: page 8]

PCI Express x4 Edge Connector

nd RX diff pairs have PN
ps to improve PCB layout

LAYOU
Route PCIe signals as matched le
suita
only the signals within a pair need to be le
tha

here is no need to match the le

ngth matched ideally to better

Mirko Electro n ics Smoka Wawelskiego 1 30-535 Kraków, Poland | Siz e A4

Titl e M.2 PCIe x1 Socket | | Ve rsion V1

Project: Pi4G PU (PiG ) | | Revision
STD_P R O R1 Va ria nt: | 300-399 RefDes:
Designer: M. Folejews k i | Sheet: 8 / 1 5
File Na me: [08] PCIe.S ch Doc | Printed : 03.1 2. 2022

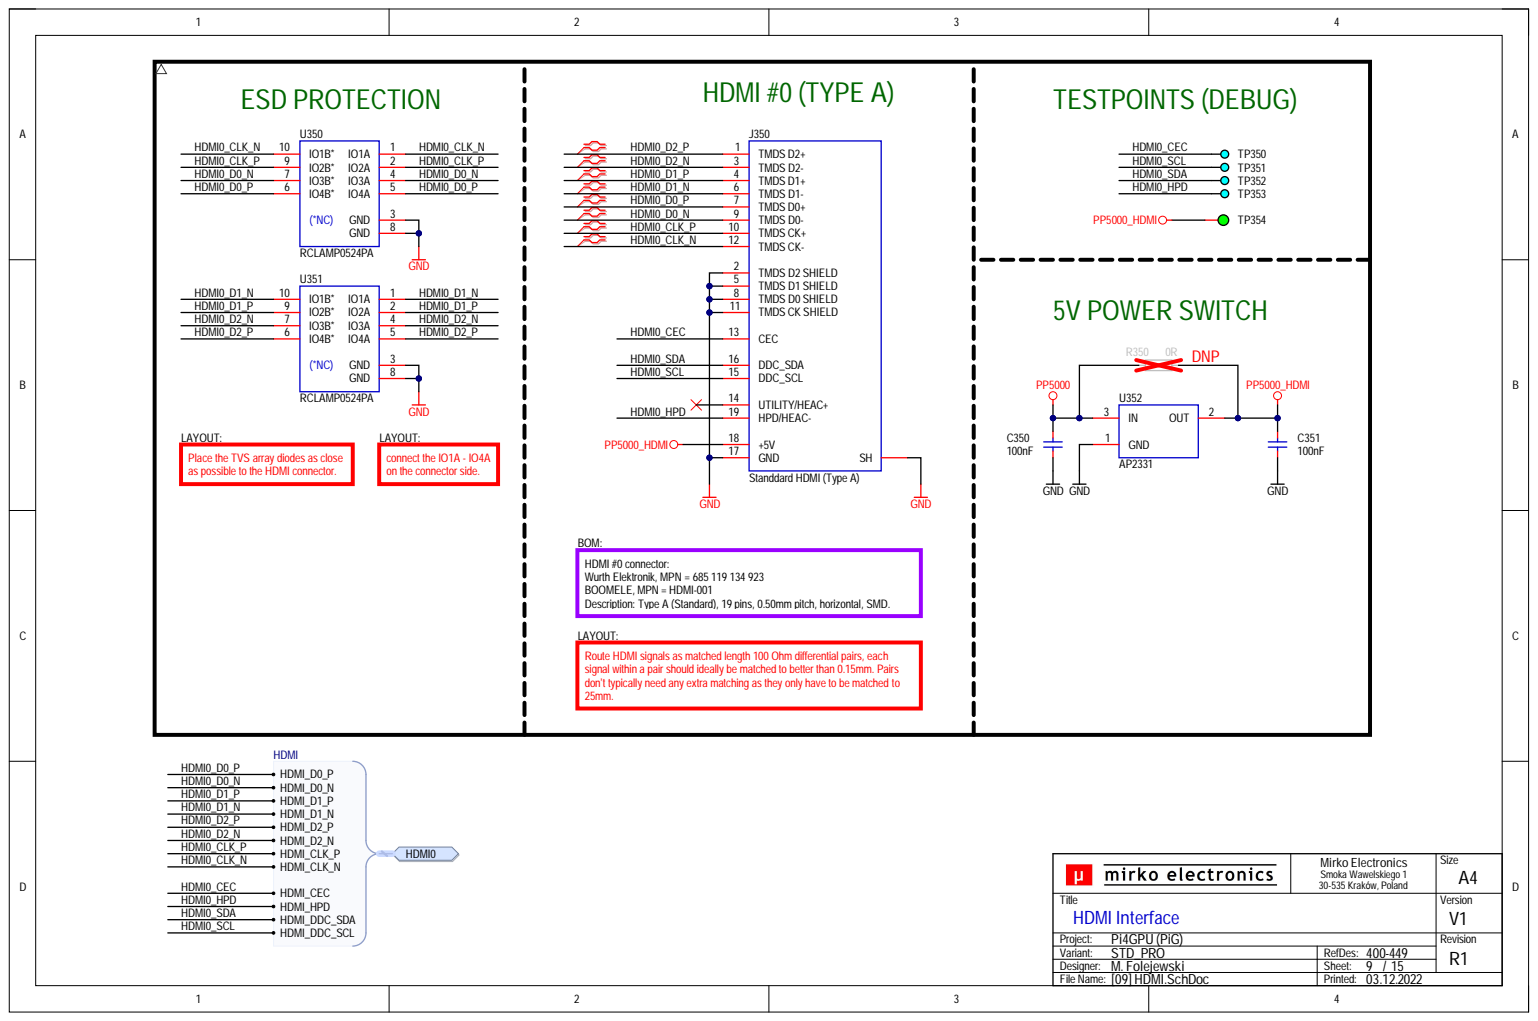
[picture p167: page 9]

Place the TVS array diodes as close
as possible to the HDMI connector.

connect the IO1A - IO4A
on the connector side.

BOM:
HDMI #0 connector:
Wurth Elektronik, MPN = 685 119 134 923
BOOMELE, MPN = HDMI-001
Description: Type A (Standard), 19 pins, 0.50mm pitch, horizontal, SMD.

LAYOUT:
Route HDMI signals as matched length 100 Ohm differential pairs, each
signal within a pair should ideally be matched to better than 0.15mm. Pairs
don’t typically need any extra matching as they only have to be matched to

Mirko Electronics Smoka Wawelskiego 1 30-535 Kraków, Poland | Size A4

Title HDMI Interface | | Version V1

Project: Pi4GPU (PiG) | | Revision R1
Variant: STD_PRO | RefDes: 400-449

File Name: [09] HDMI.SchDoc | Printed:

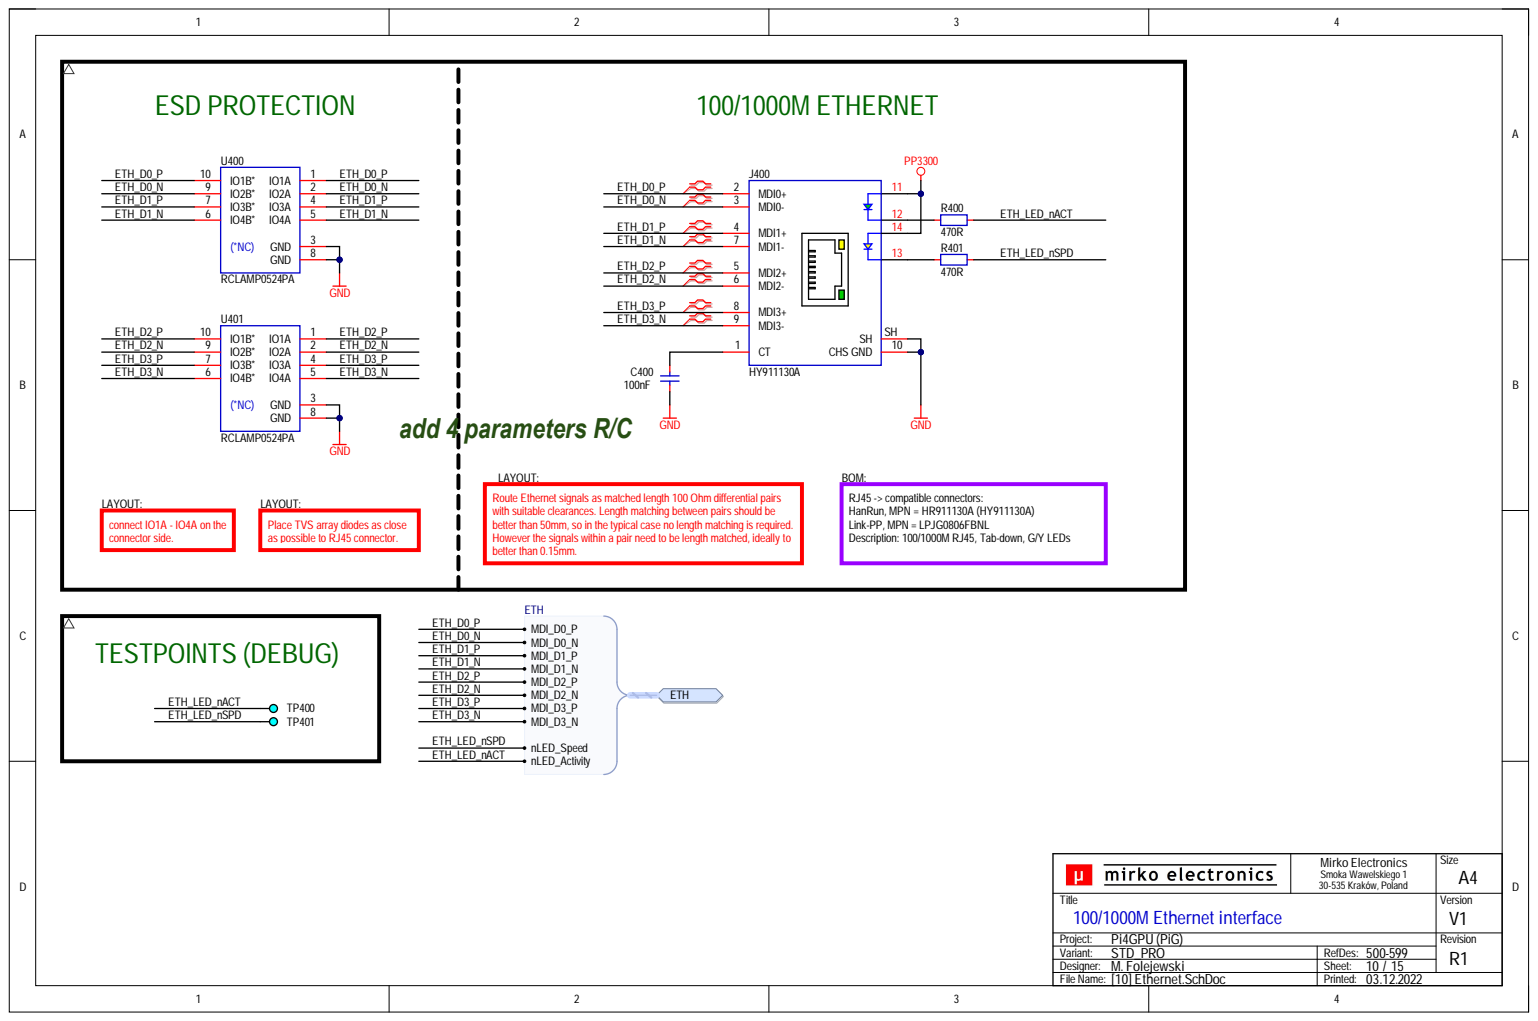
[picture p168: page 10]

LAYOUT:
Route Ethernet signals as matched length 100 Ohm differential pairs
with suitable clearances. Length matching between pairs should be
better than 50mm, so in the typical case no length matching is required.
However the signals within a pair need to be length matched, ideally to
better than 0.15mm.

BOM:
RJ45 -> compatible connectors:
HanRun, MPN = HR911130A (HY911130A)
Link-PP, MPN = LPJG0806FBNL
Description: 100/1000M RJ45, Tab-down, G/Y LEDs

Place TVS array diodes as close
as possible to RJ45 connector.

Mirko Electronics Smoka Wawelskiego 1 30-535 Kraków, Poland | Size A4

Title 100/1000M Ethernet interface | | Version V1

Project: Pi4GPU (PiG) | | Revision R1
Variant: STD_PRO | RefDes: 500-599

File Name: [10] Ethernet.SchDoc | Printed:

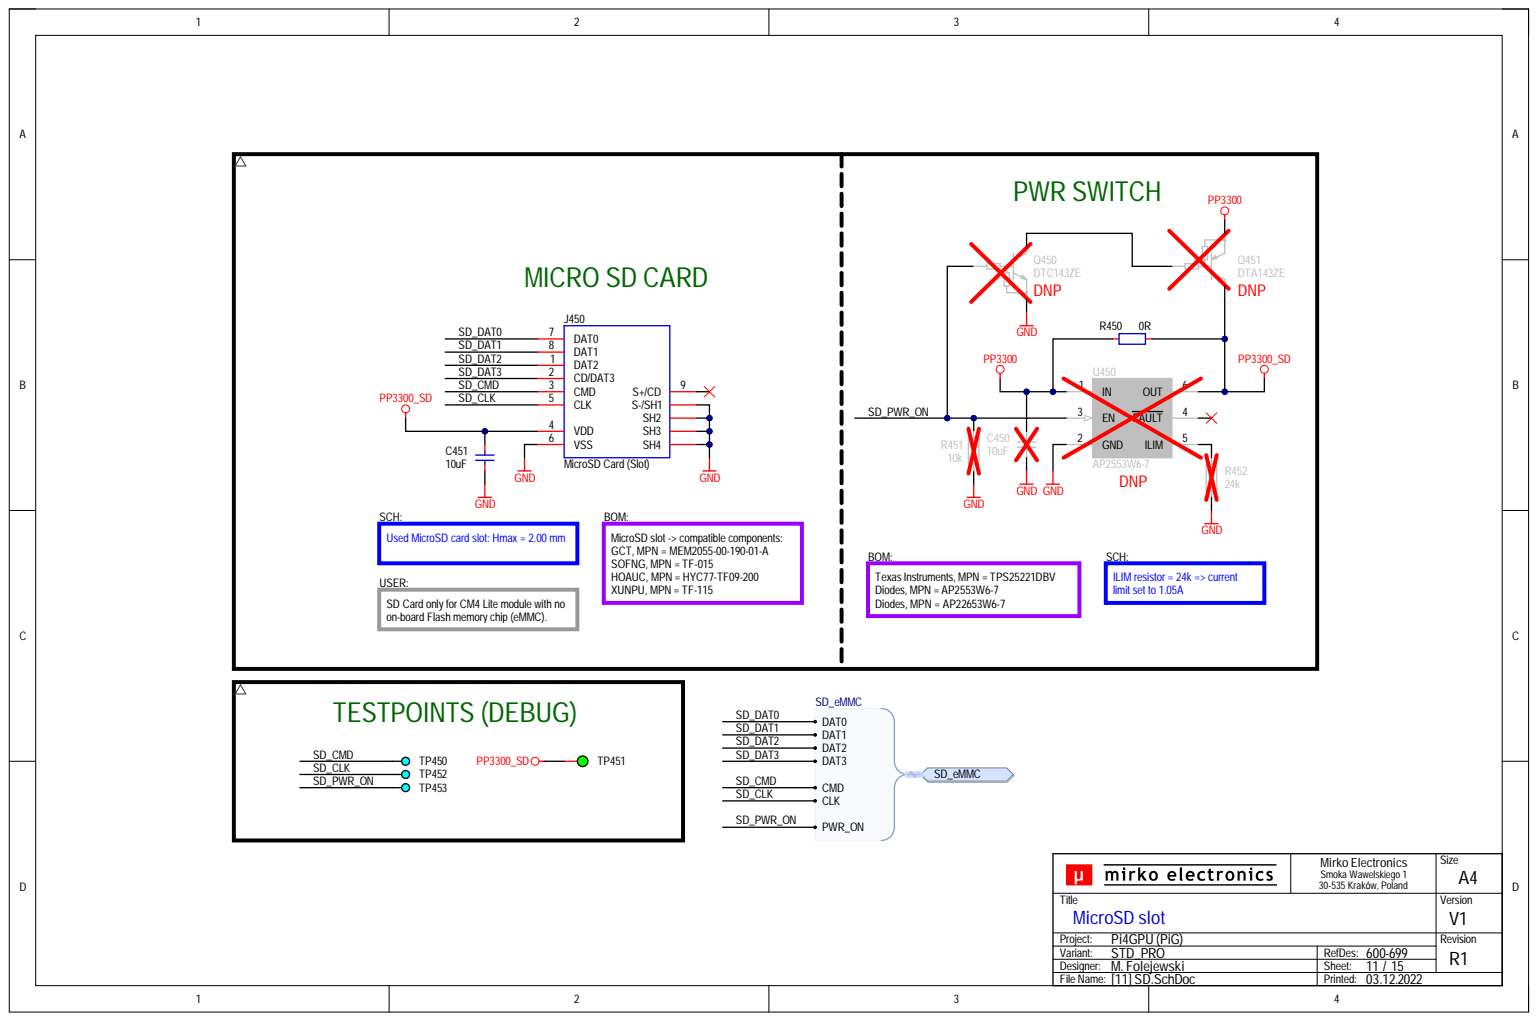
[picture p169: page 11]

SCH:
Used MicroSD card slot: Hmax = 2.00 mm

BOM:
MicroSD slot -> compatible components:
GCT, MPN = MEM2055-00-190-01-A
SOFNG, MPN = TF-015
HOAUC, MPN = HYC77-TF09-200
XUNPU, MPN = TF-115

USER:
SD Card only for CM4 Lite module with no
on-board Flash memory chip (eMMC).

Mirko Electronics Smoka Wawelskiego 1 30-535 Kraków, Poland | Size A4

Title MicroSD slot | | Version V1

Project: Pi4GPU (PiG) | | Revision R1
Variant: STD_PRO | RefDes: 600-699

File Name: [11] SD.SchDoc | Printed:

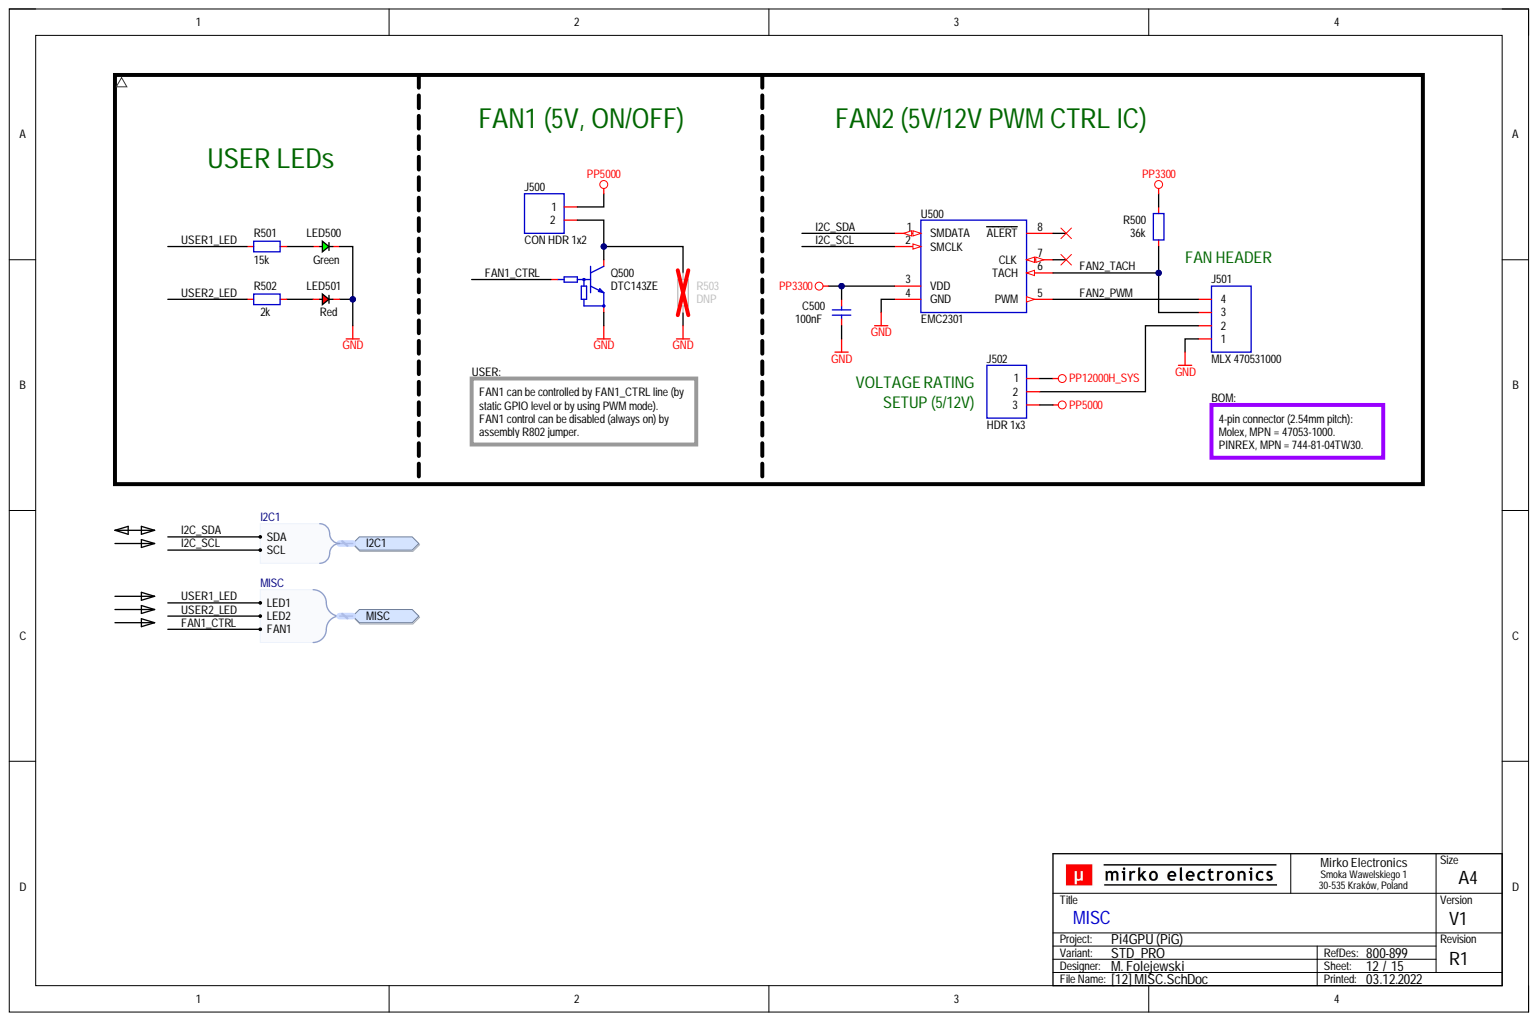
[picture p170: page 12]

USER:
FAN1 can be controlled by FAN1_CTRL line (by
static GPIO level or by using PWM mode).
FAN1 control can be disabled (always on) by
assembly R802 jumper.

Mirko Electronics Smoka Wawelskiego 1 30-535 Kraków, Poland | Size A4

Title MISC | | Version V1

Project: Pi4GPU (PiG) | | Revision R1
Variant: STD_PRO | RefDes: 800-899

File Name: [12] MISC.SchDoc | Printed:

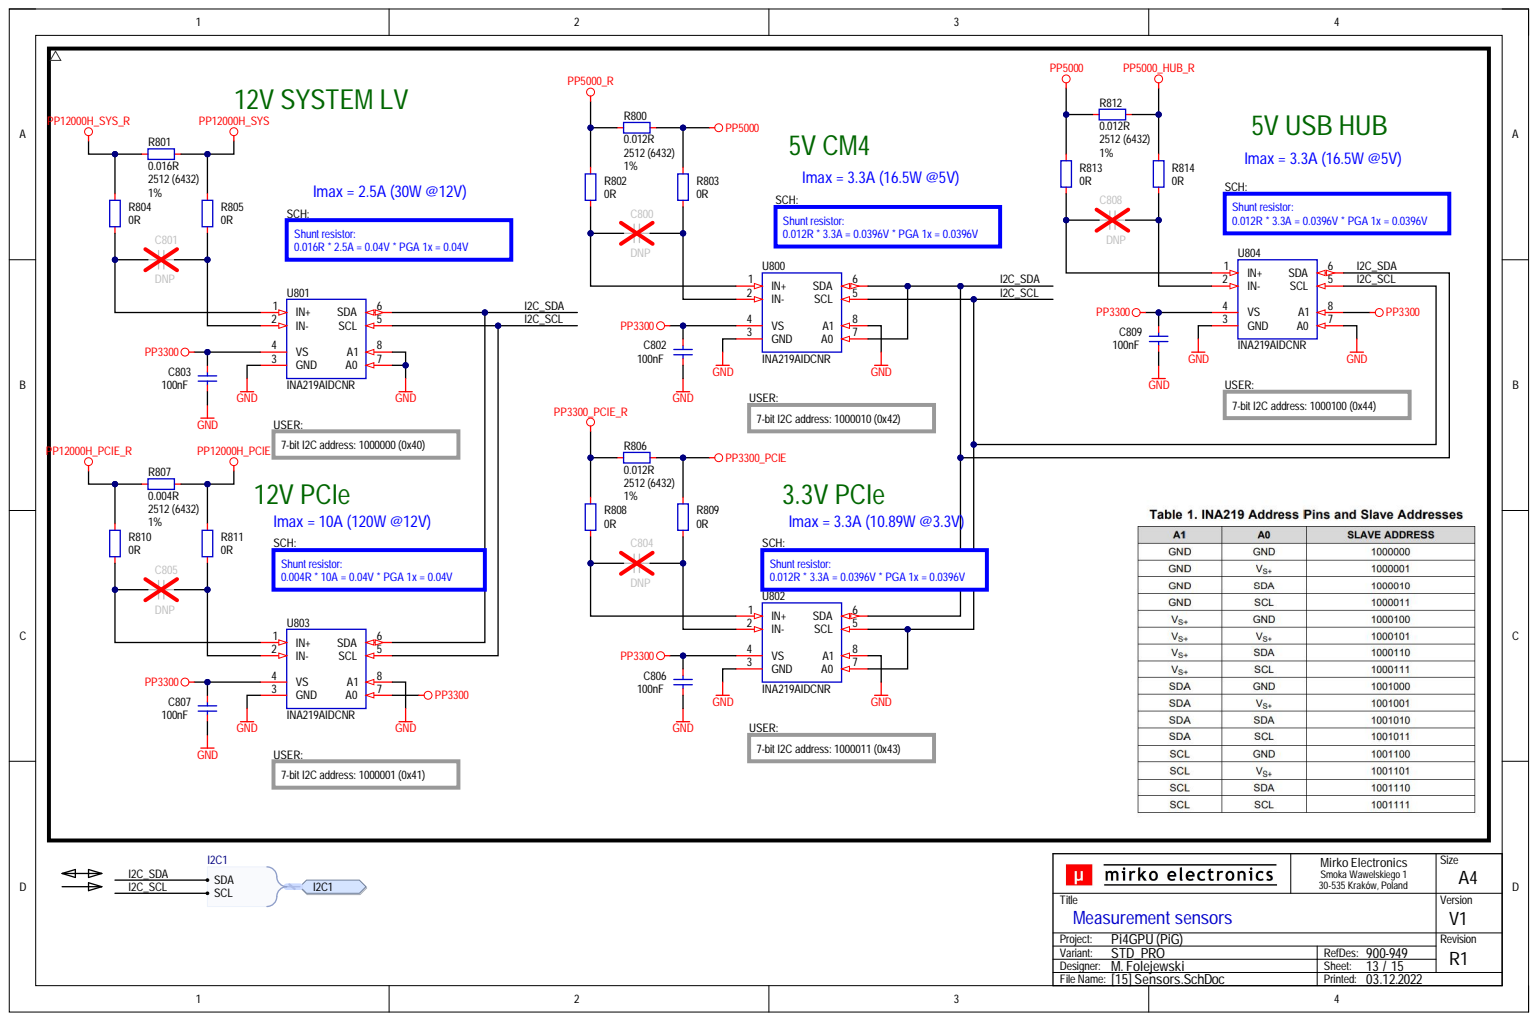
[picture p171: page 13]

7-bit I2C address: 1000010 (0x42)

7-bit I2C address: 1000000 (0x40)

Mirko Electronics Smoka Wawelskiego 1 30-535 Kraków, Poland | Size A4

Title Measurement sensors | | Version V1

Project: Pi4GPU (PiG) | | Revision R1
Variant: STD_PRO | RefDes: 900-949

File Name: [15] Sensors.SchDoc | Printed:

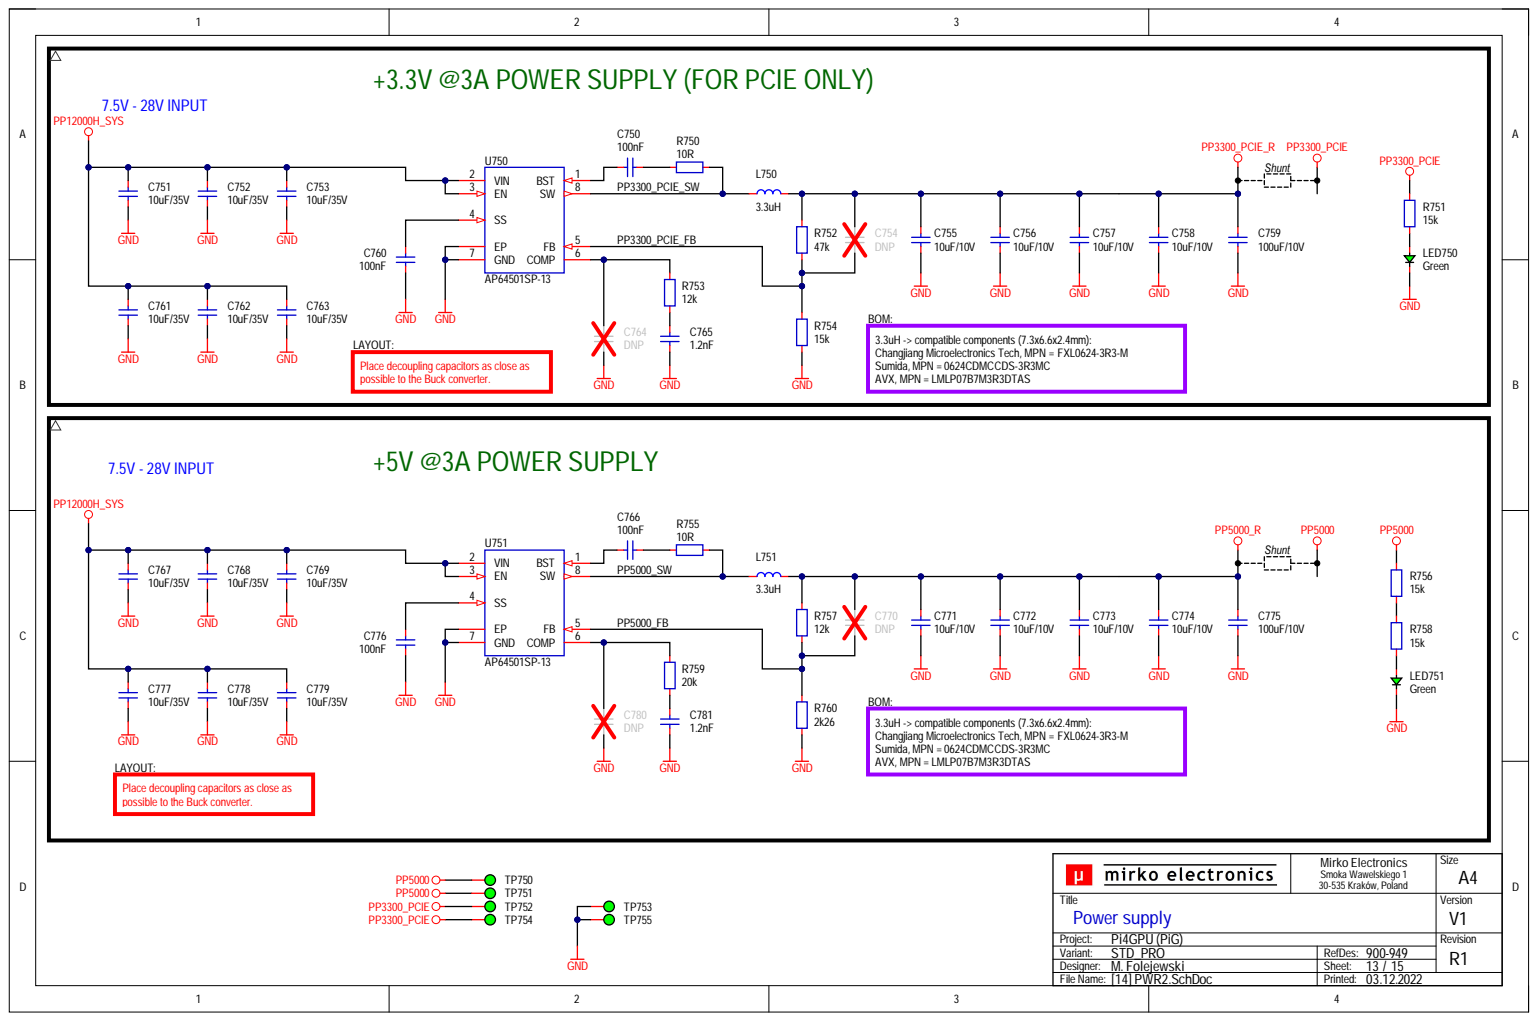
[picture p172: page 14]

+3.3V @3A POWER SUPPLY (FOR PCIE ONLY)

BOM:
3.3uH -> compatible components (7.3x6.6x2.4mm):
Changjiang Microelectronics Tech, MPN = FXL0624-3R3-M
Sumida, MPN = 0624CDMCCDS-3R3MC
AVX, MPN = LMLP07B7M3R3DTAS

LAYOUT:
Place decoupling capacitors as close as
possible to the Buck converter.

Mirko Electronics Smoka Wawelskiego 1 30-535 Kraków, Poland | Size A4

Title Power supply | | Version V1

Project: Pi4GPU (PiG) | | Revision R1
Variant: STD_PRO | RefDes: 900-949

File Name: [14] PWR2.SchDoc | Printed:

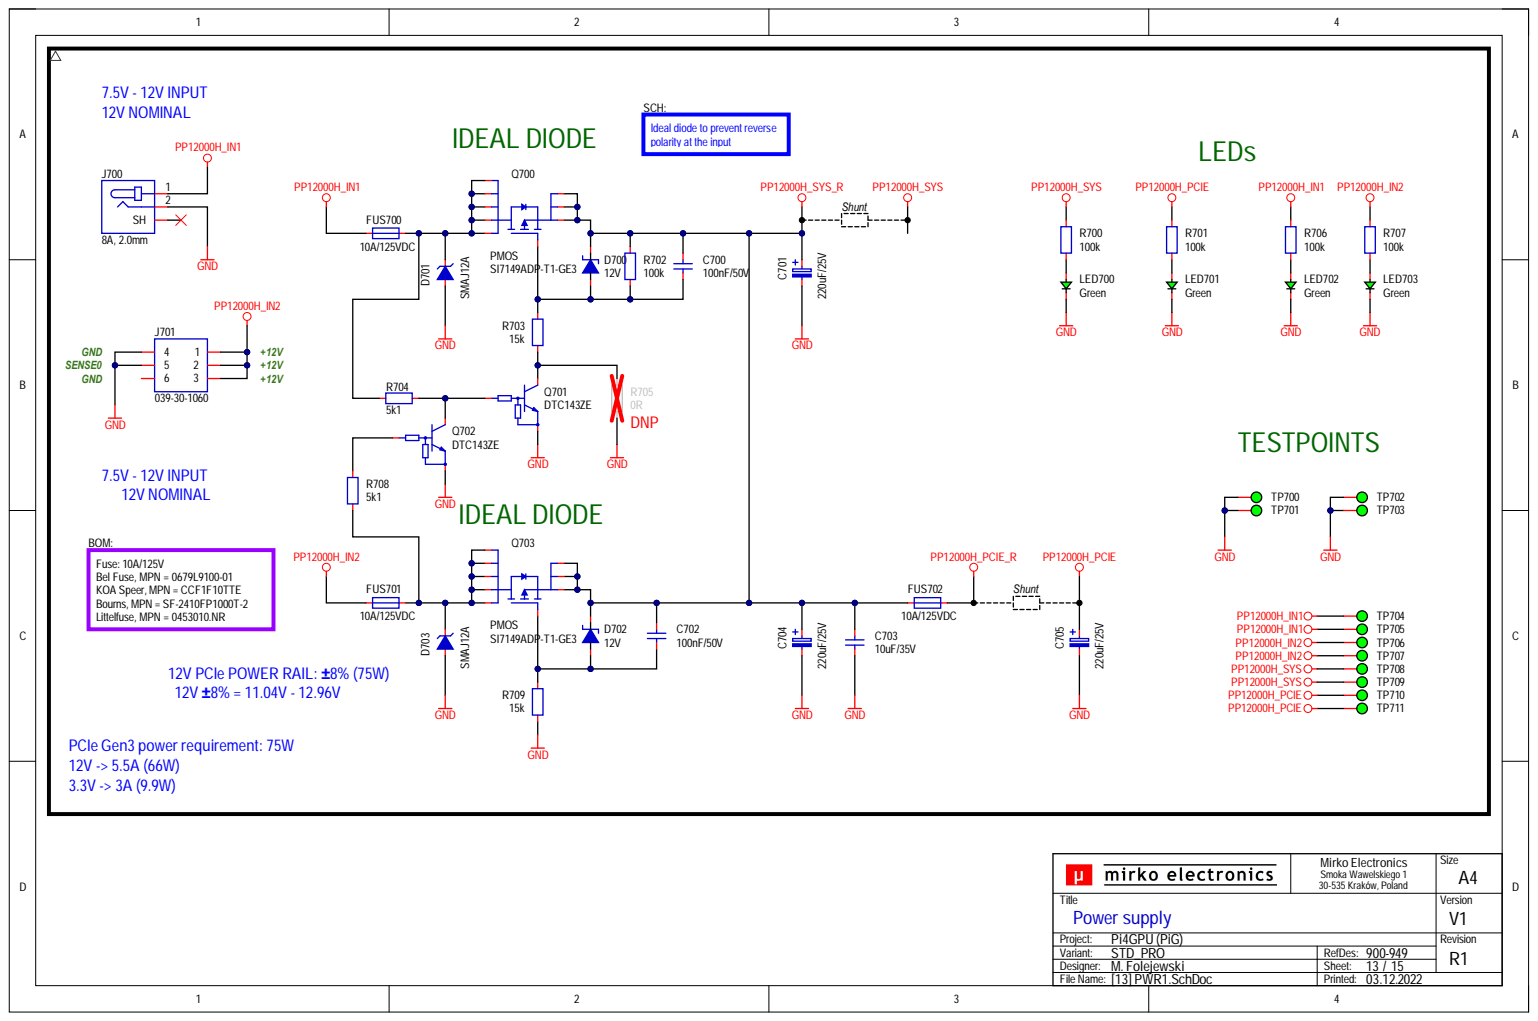
[picture p173: page 15]

SCH:
Ideal diode to prevent reverse
polarity at the input

Mirko Electronics Smoka Wawelskiego 1 30-535 Kraków, Poland | Size A4

Title Power supply | | Version V1

Project: Pi4GPU (PiG) | | Revision R1
Variant: STD_PRO | RefDes: 900-949

File Name: [13] PWR1.SchDoc | Printed:

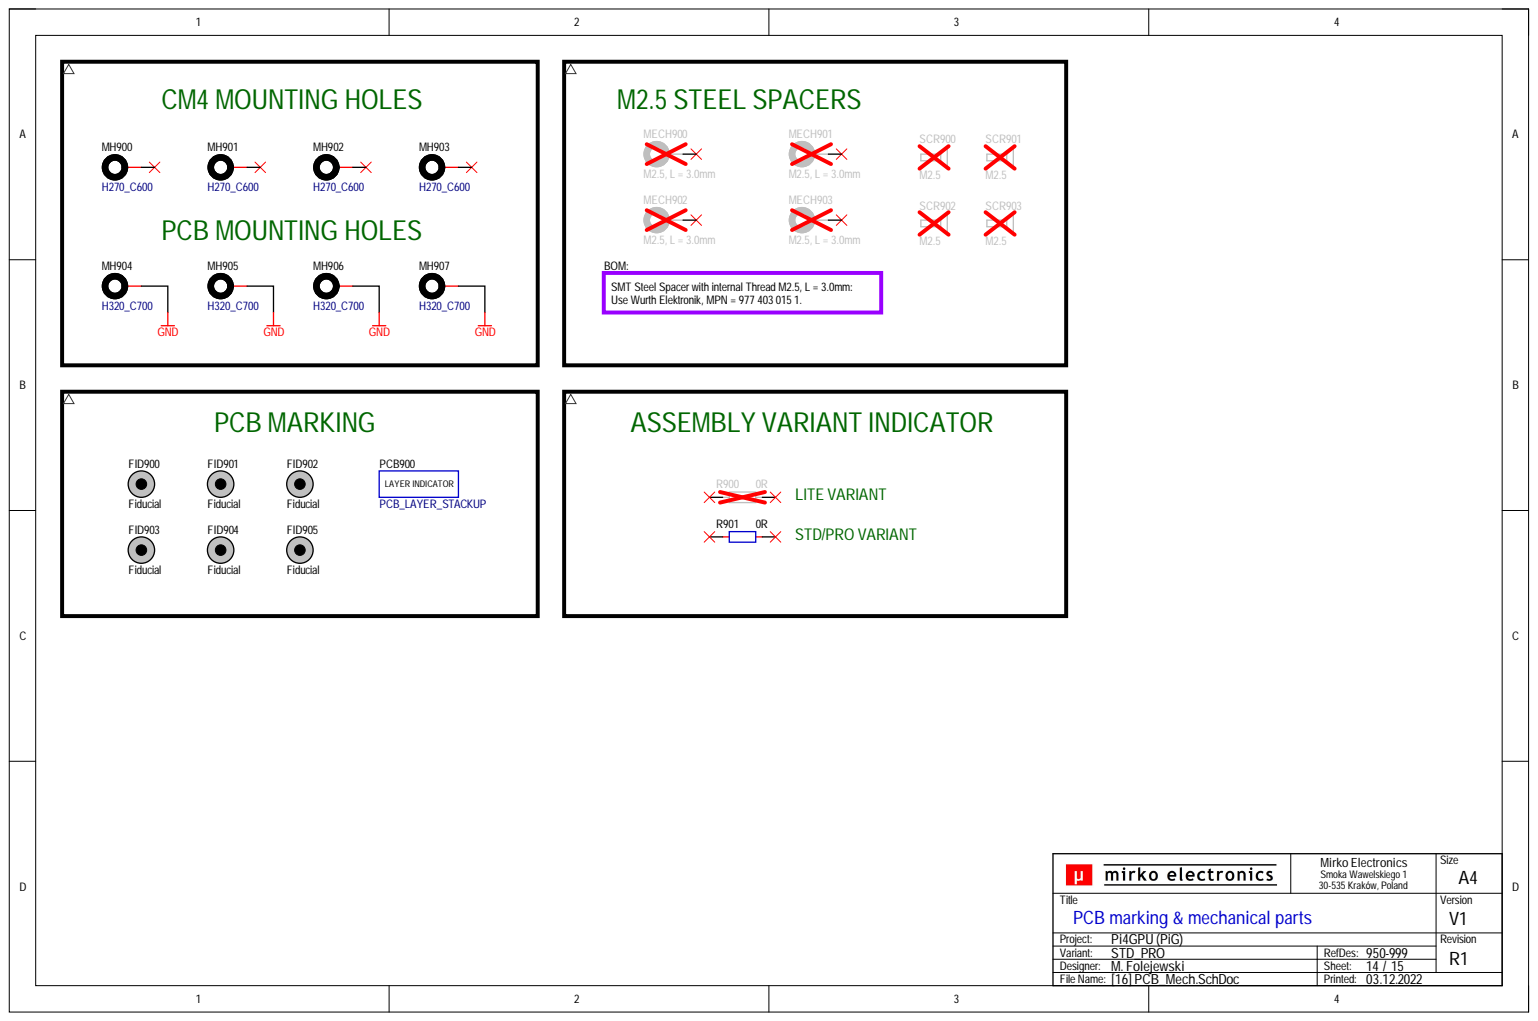
[picture p174: page 16]

BOM:
SMT Steel Spacer with internal Thread M2.5, L = 3.0mm:
Use Wurth Elektronik, MPN = 977 403 015 1.

Mirko Electronics Smoka Wawelskiego 1 30-535 Kraków, Poland | Size A4

Title PCB marking & mechanical parts | | Version V1

Project: Pi4GPU (PiG) | | Revision R1
Variant: STD_PRO | RefDes: 950-999

File Name: [16] PCB_Mech.SchDoc | Printed:

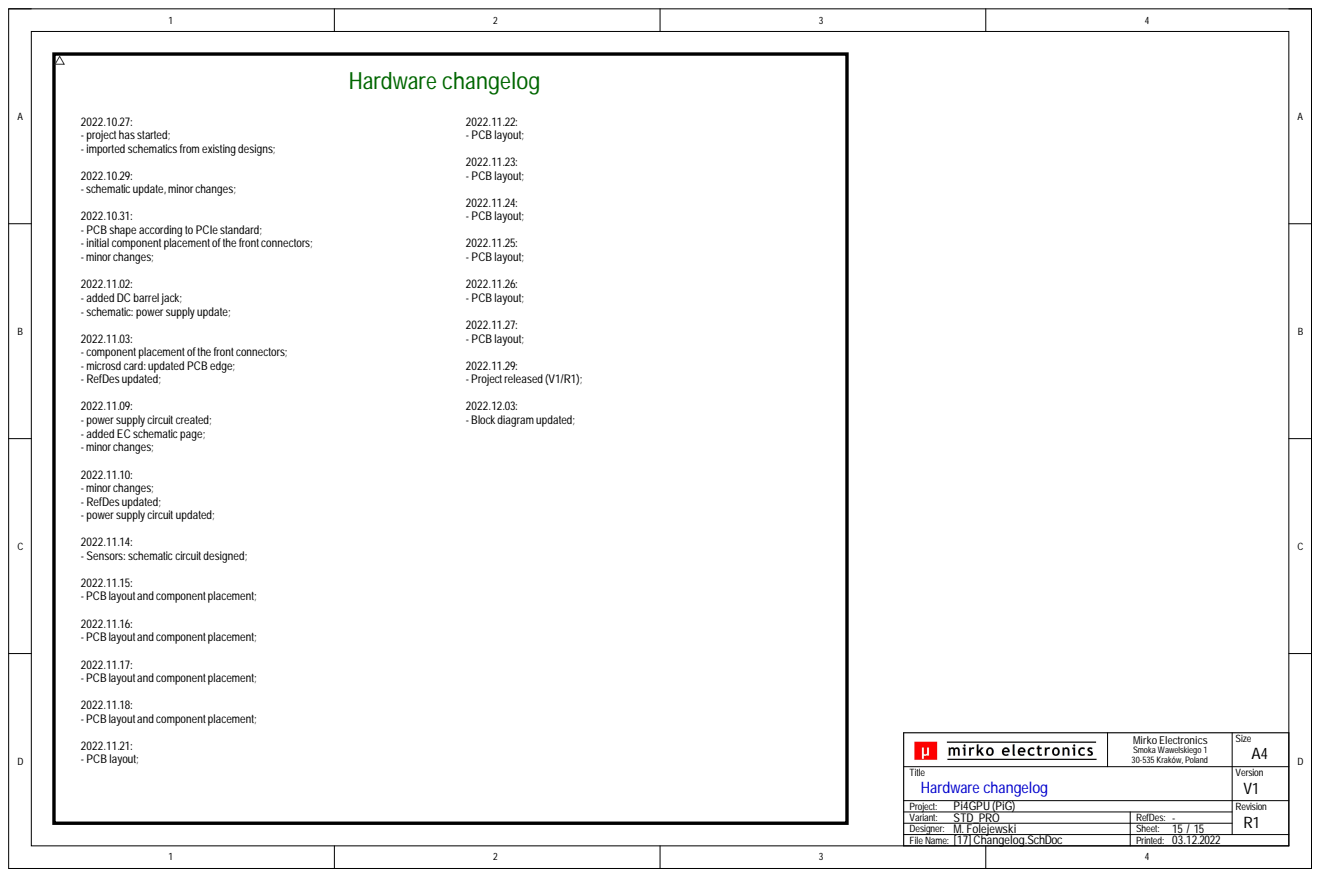
[picture p175: page 17]

- project has started;
- imported schematics from existing designs;

- schematic update, minor changes;

- PCB shape according to PCIe standard;
- initial component placement of the front connectors;
- minor changes;

- added DC barrel jack;
- schematic: power supply update;

- component placement of the front connectors;
- microsd card: updated PCB edge;
- RefDes updated;

- power supply circuit created;
- added EC schematic page;

- power supply circuit updated;

- Sensors: schematic circuit designed;

- PCB layout and component placement;

Mirko Electronics Smoka Wawelskiego 1 30-535 Kraków, Poland | Size A4

Title Hardware changelog | | Version V1

Revision R1
Variant: STD_PRO

File Name: [17] Changelog.SchDoc | Printed:
