geerlingguy/pi4gpu/schematics/deprecated/CM4GPU_v1_Schematic_20221110.pdf

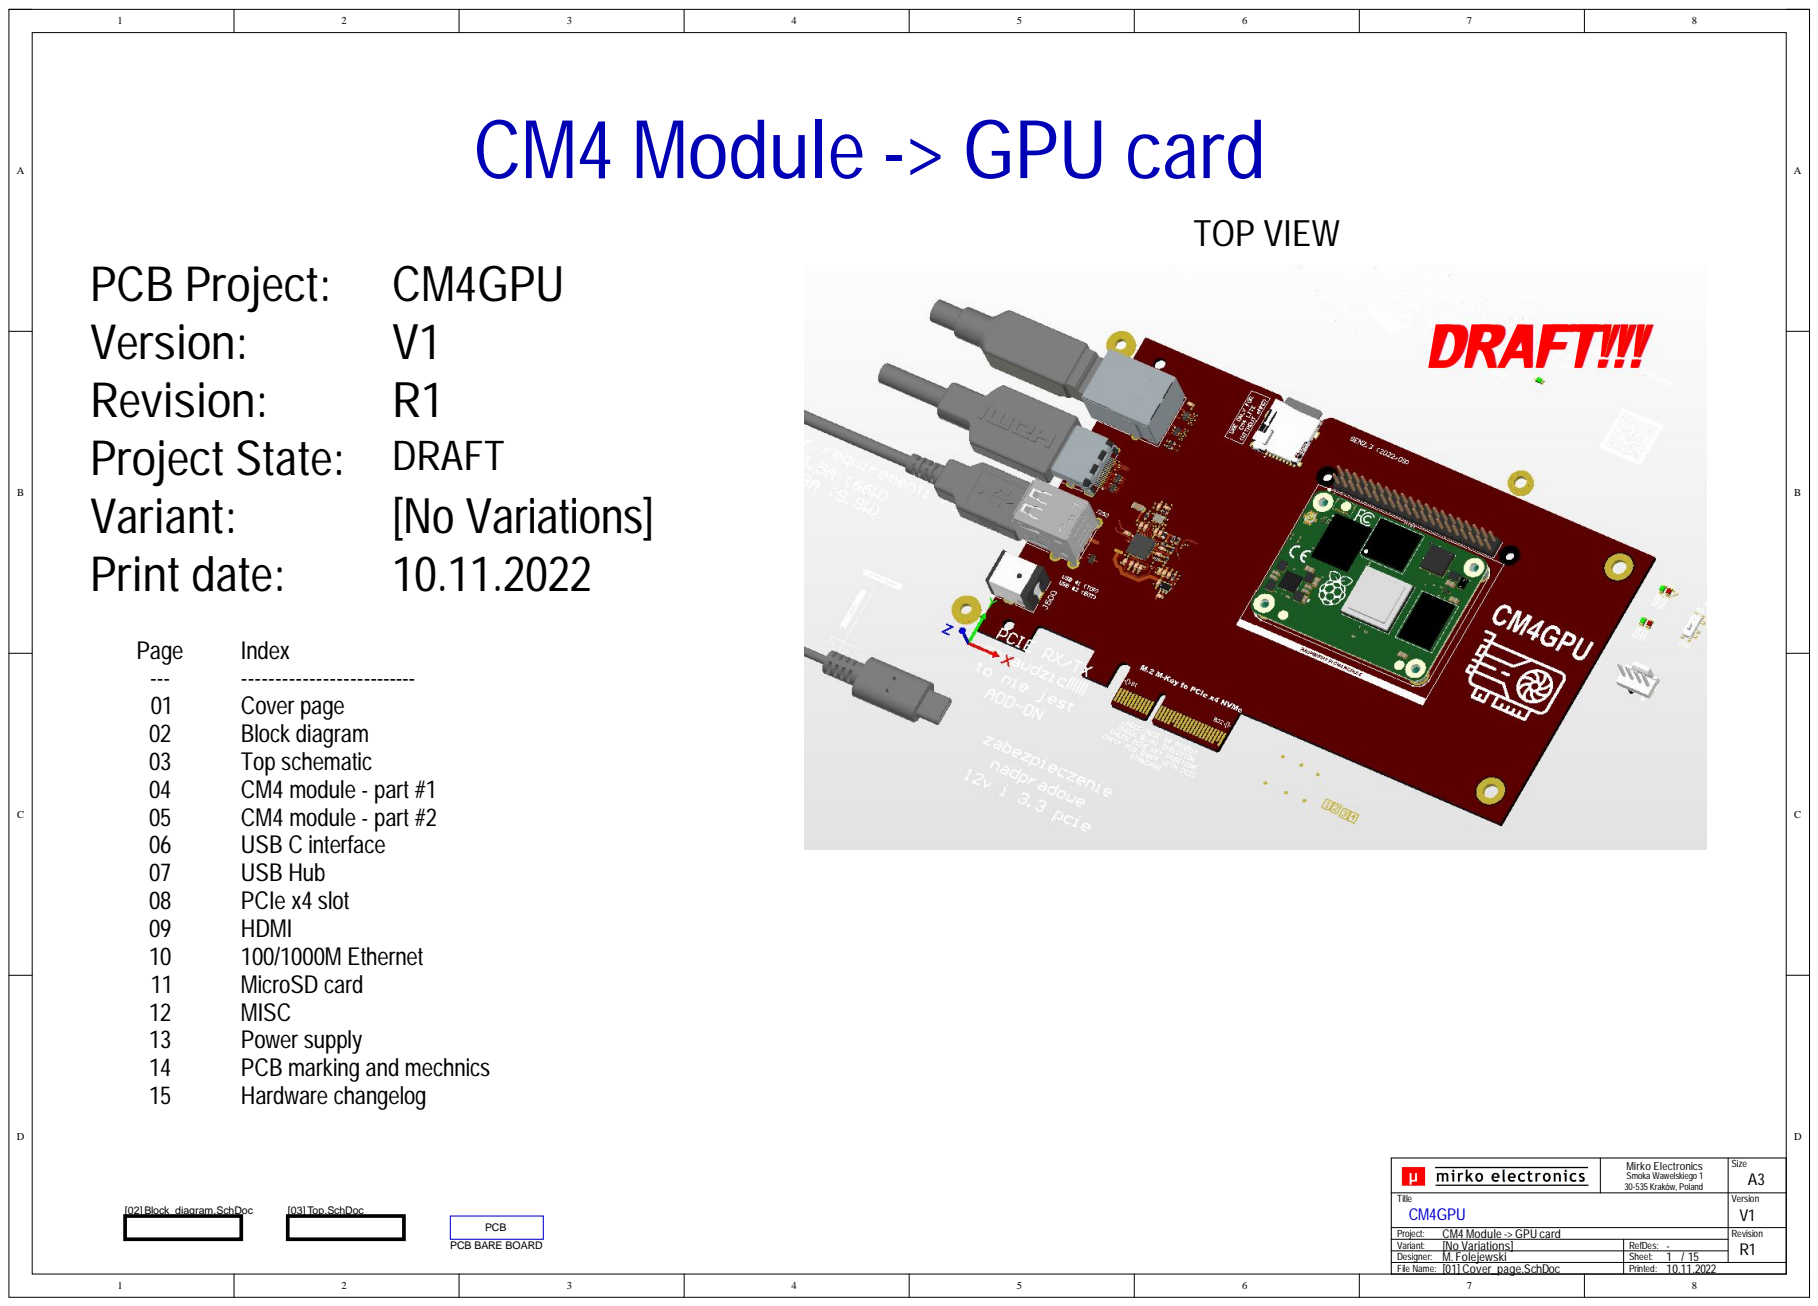
[picture p209: page 1]

Mirko Electronics Smoka Wawelskiego 1 30-535 Kraków, Poland | Size A3

Title CM4GPU | | Version V1

Project: CM4 Module -> GPU card | | Revision R1
Variant: [No Variations] | RefDes: -
Designer: M. Folejewski
File Name: [01] Cover_page.SchDoc | Printed:

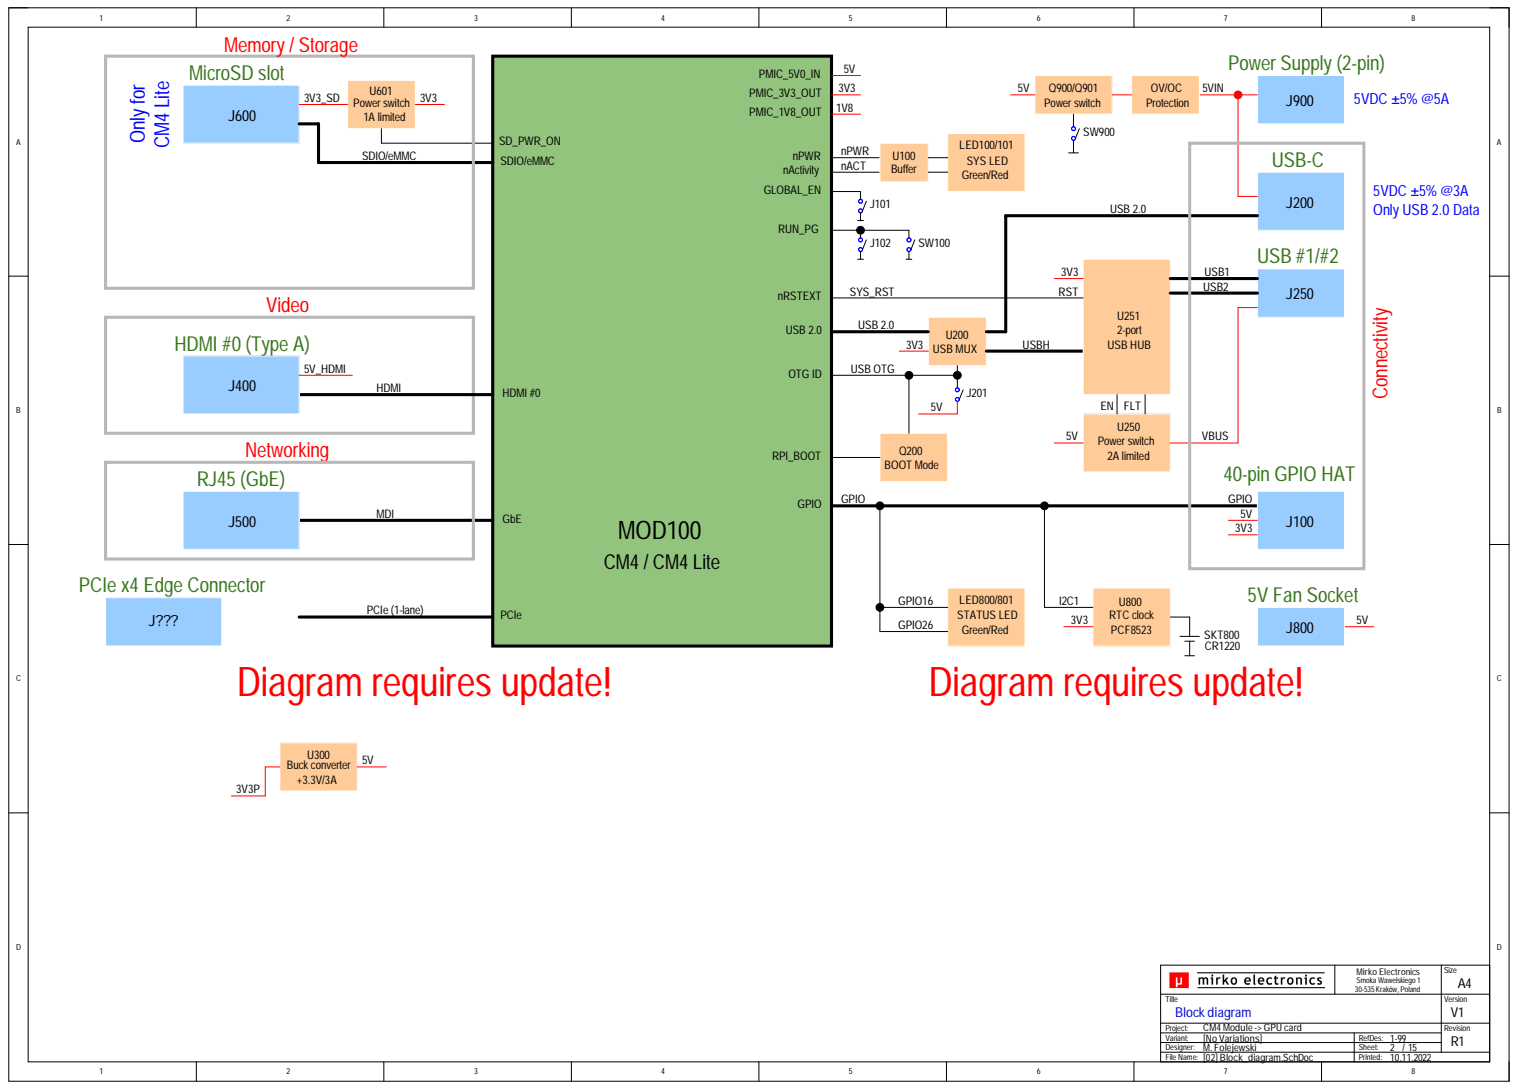
[picture p210: page 2]

SDIO/eMMC

USB OTG OTG ID

Mirko Electronics Smoka Wawelskiego 1 30-535 Kraków, Poland | Size A4

Title Block diagram | | Version V1

Project: CM4 Module -> GPU card | | Revision R1
Variant: [No Variations] | RefDes: 1-99

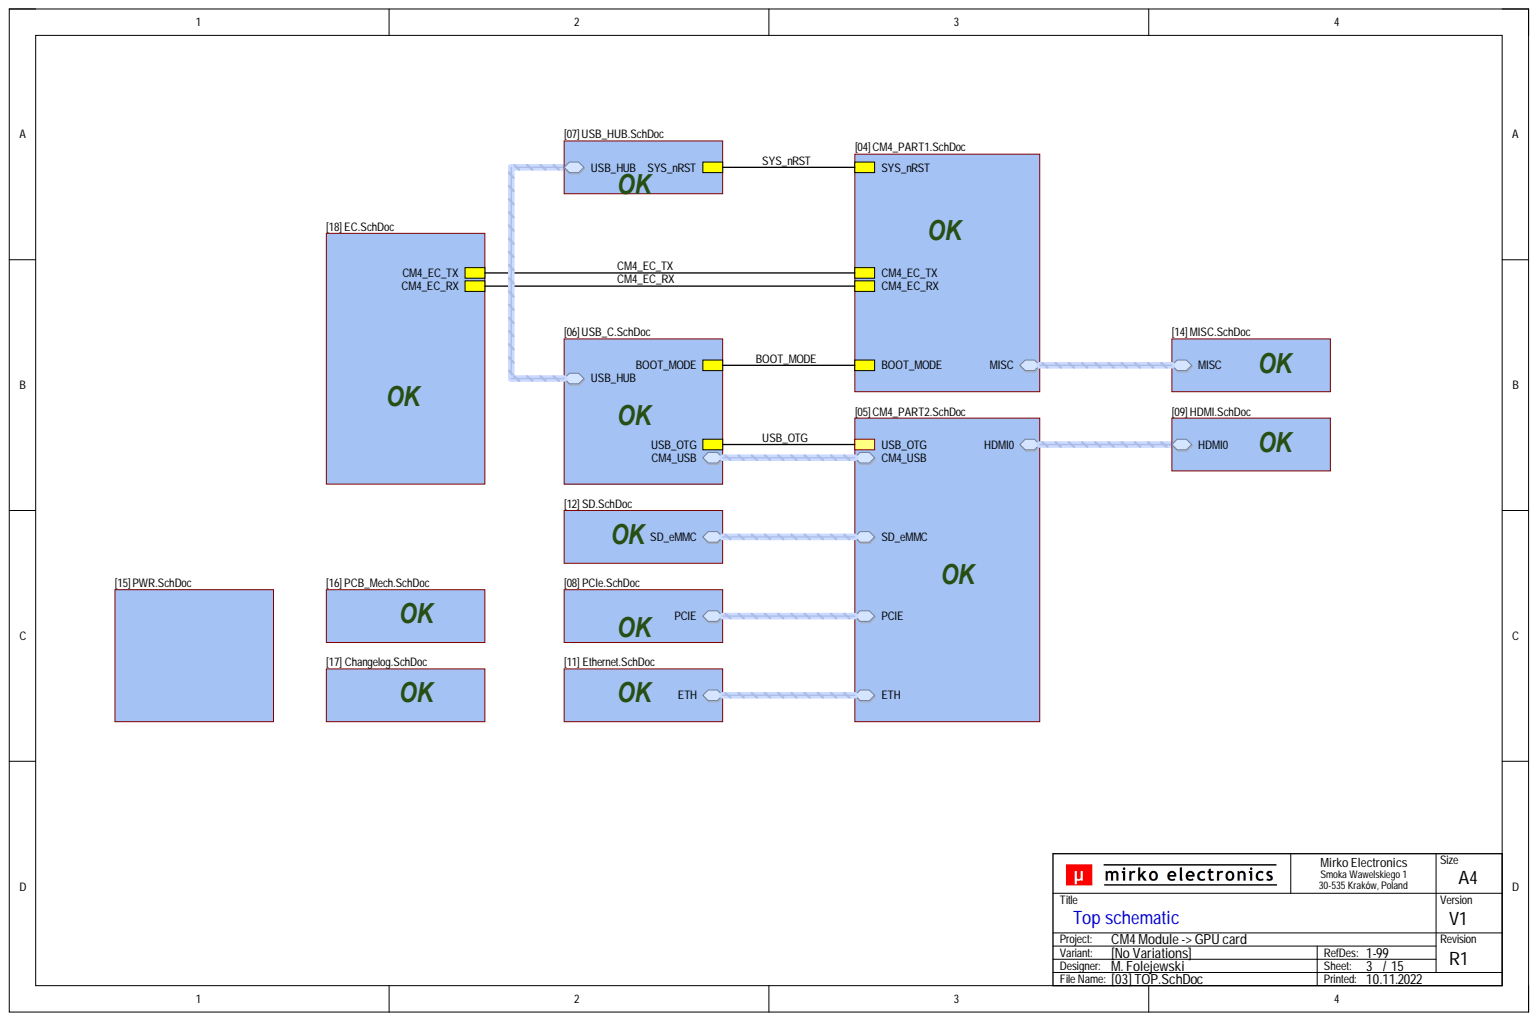
[picture p211: page 3]

[06] USB_C.SchDoc

Mirko Electronics Smoka Wawelskiego 1 30-535 Kraków, Poland | Size A4

Title Top schematic | | Version V1

Project: CM4 Module -> GPU card | | Revision R1
Variant: [No Variations] | RefDes: 1-99

Sheet: 3 15 /

File Name: [03] TOP.SchDoc | Printed: 10.11.2022

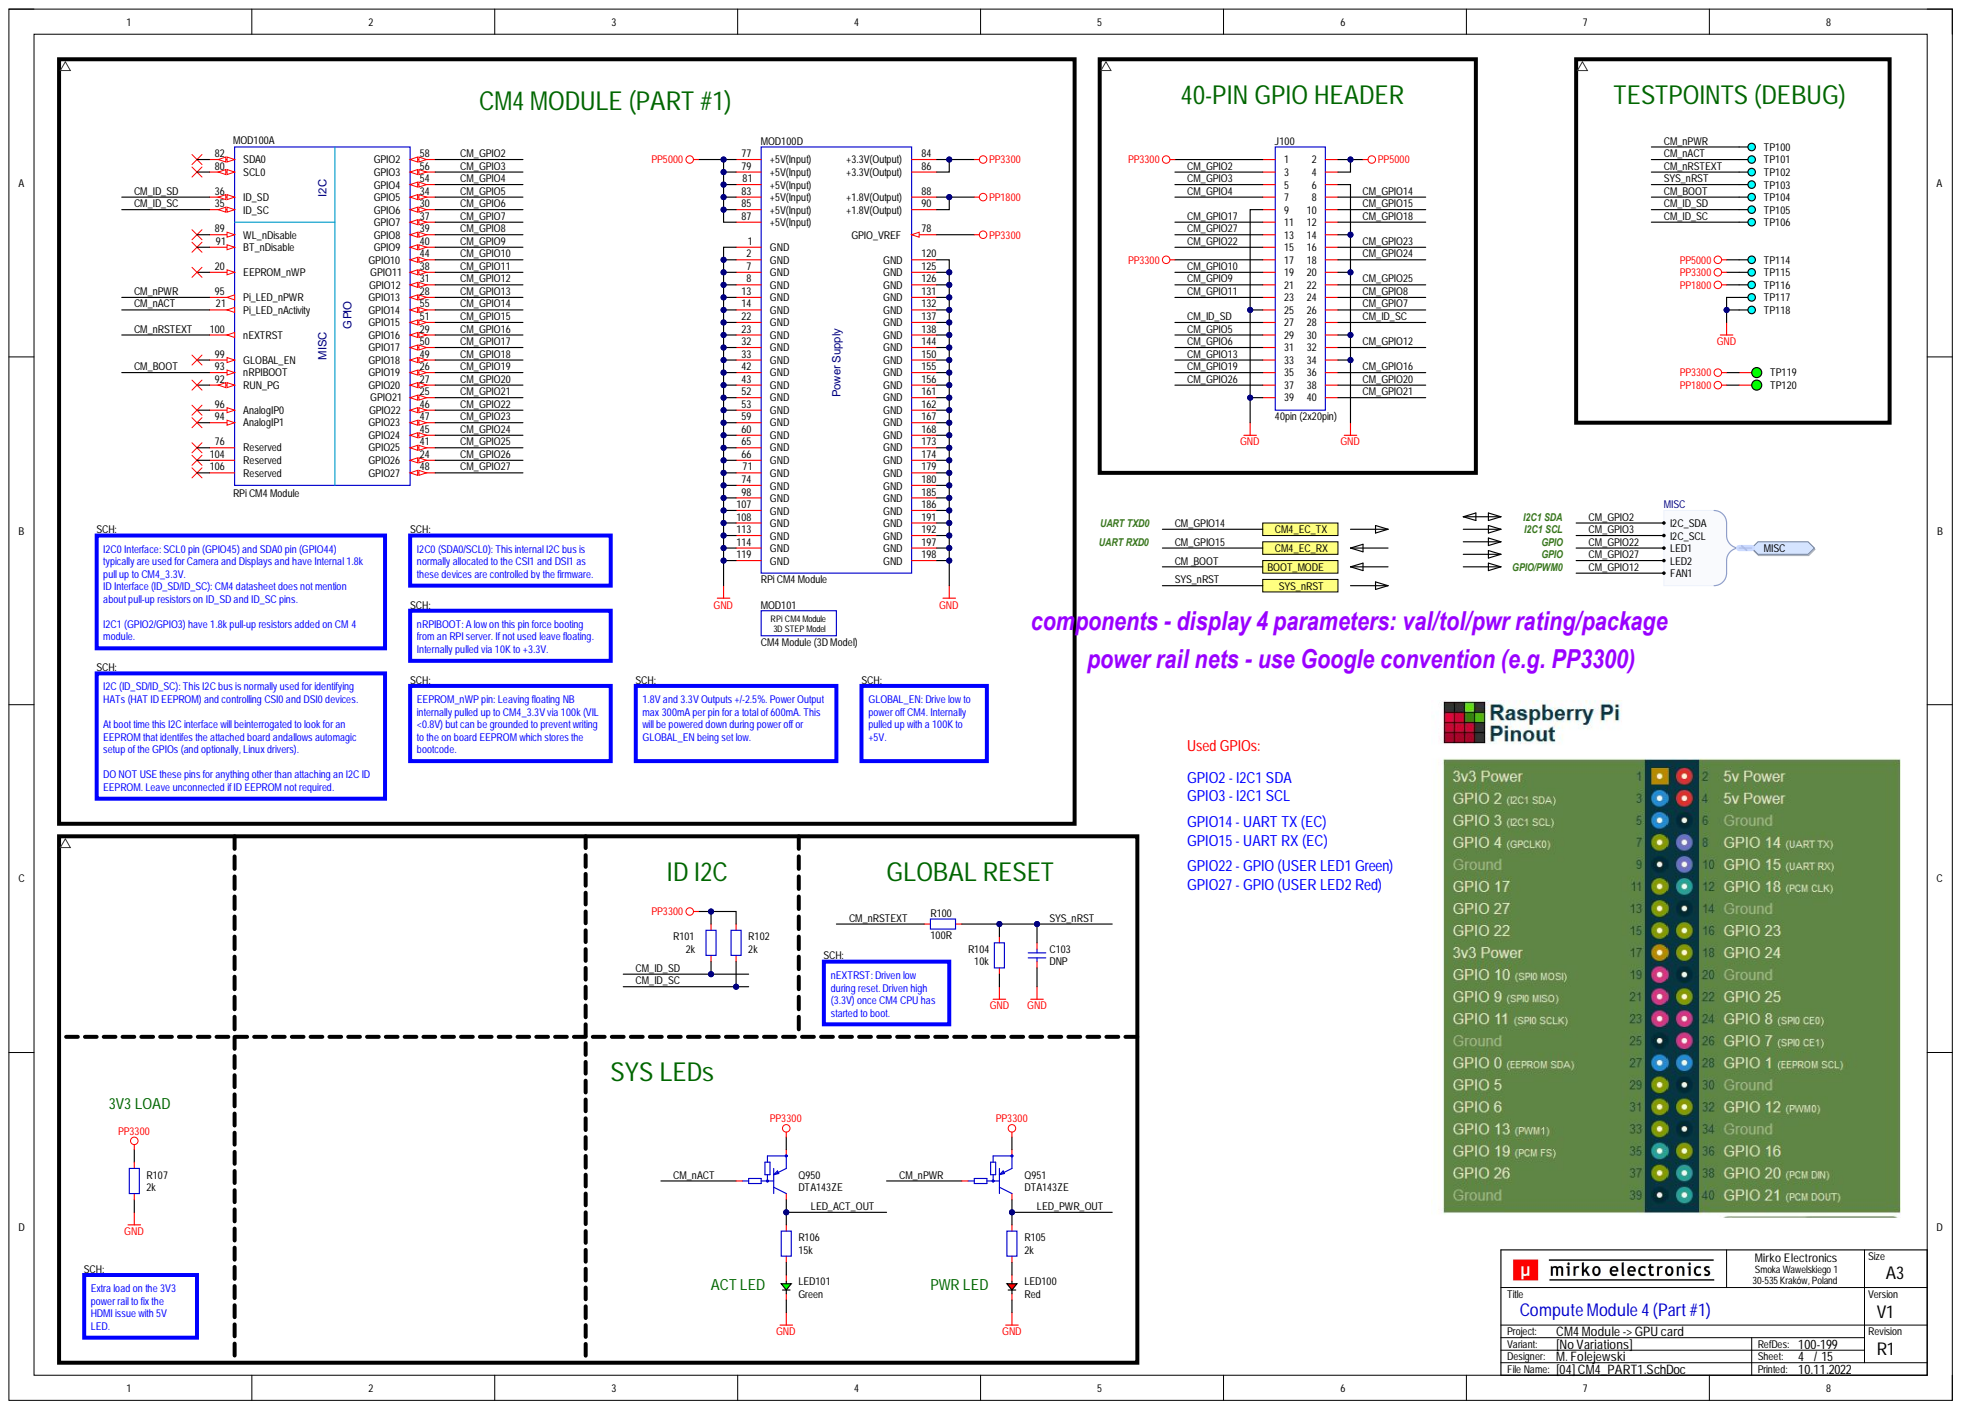
[picture p212: page 4]

85 | 90
87 | 7 8

1 3 | 1 31
1 4 | 1 32
22 | 1 37

1 07 | 1 86
1 08 | 1 91

power rail nets - use Google convention (e.g. PP3300)

Mi r k o E l ec tro n i cs Smoka Wawelskiego 1 30-535 Kra kó w, Pol a nd | S i z e A 3

T i tl e C o m p u te Mod ule 4 (Part #1) | | Versi on V1

Proj ect: C M4 Mo d u l e -> G P U ca rd | | R evi s i on R 1
Vari a n t: [ N o V a ri a ti o n s ] | R efDes : 1 00-1 99
Des i g ner: M. F o l ej ews ki | S hee t: 4 / 1 5
F i l e N ame : [04] C M4_PA R T 1 . S ch Doc | Pri n ted : 1 0. 1 1 . 2022

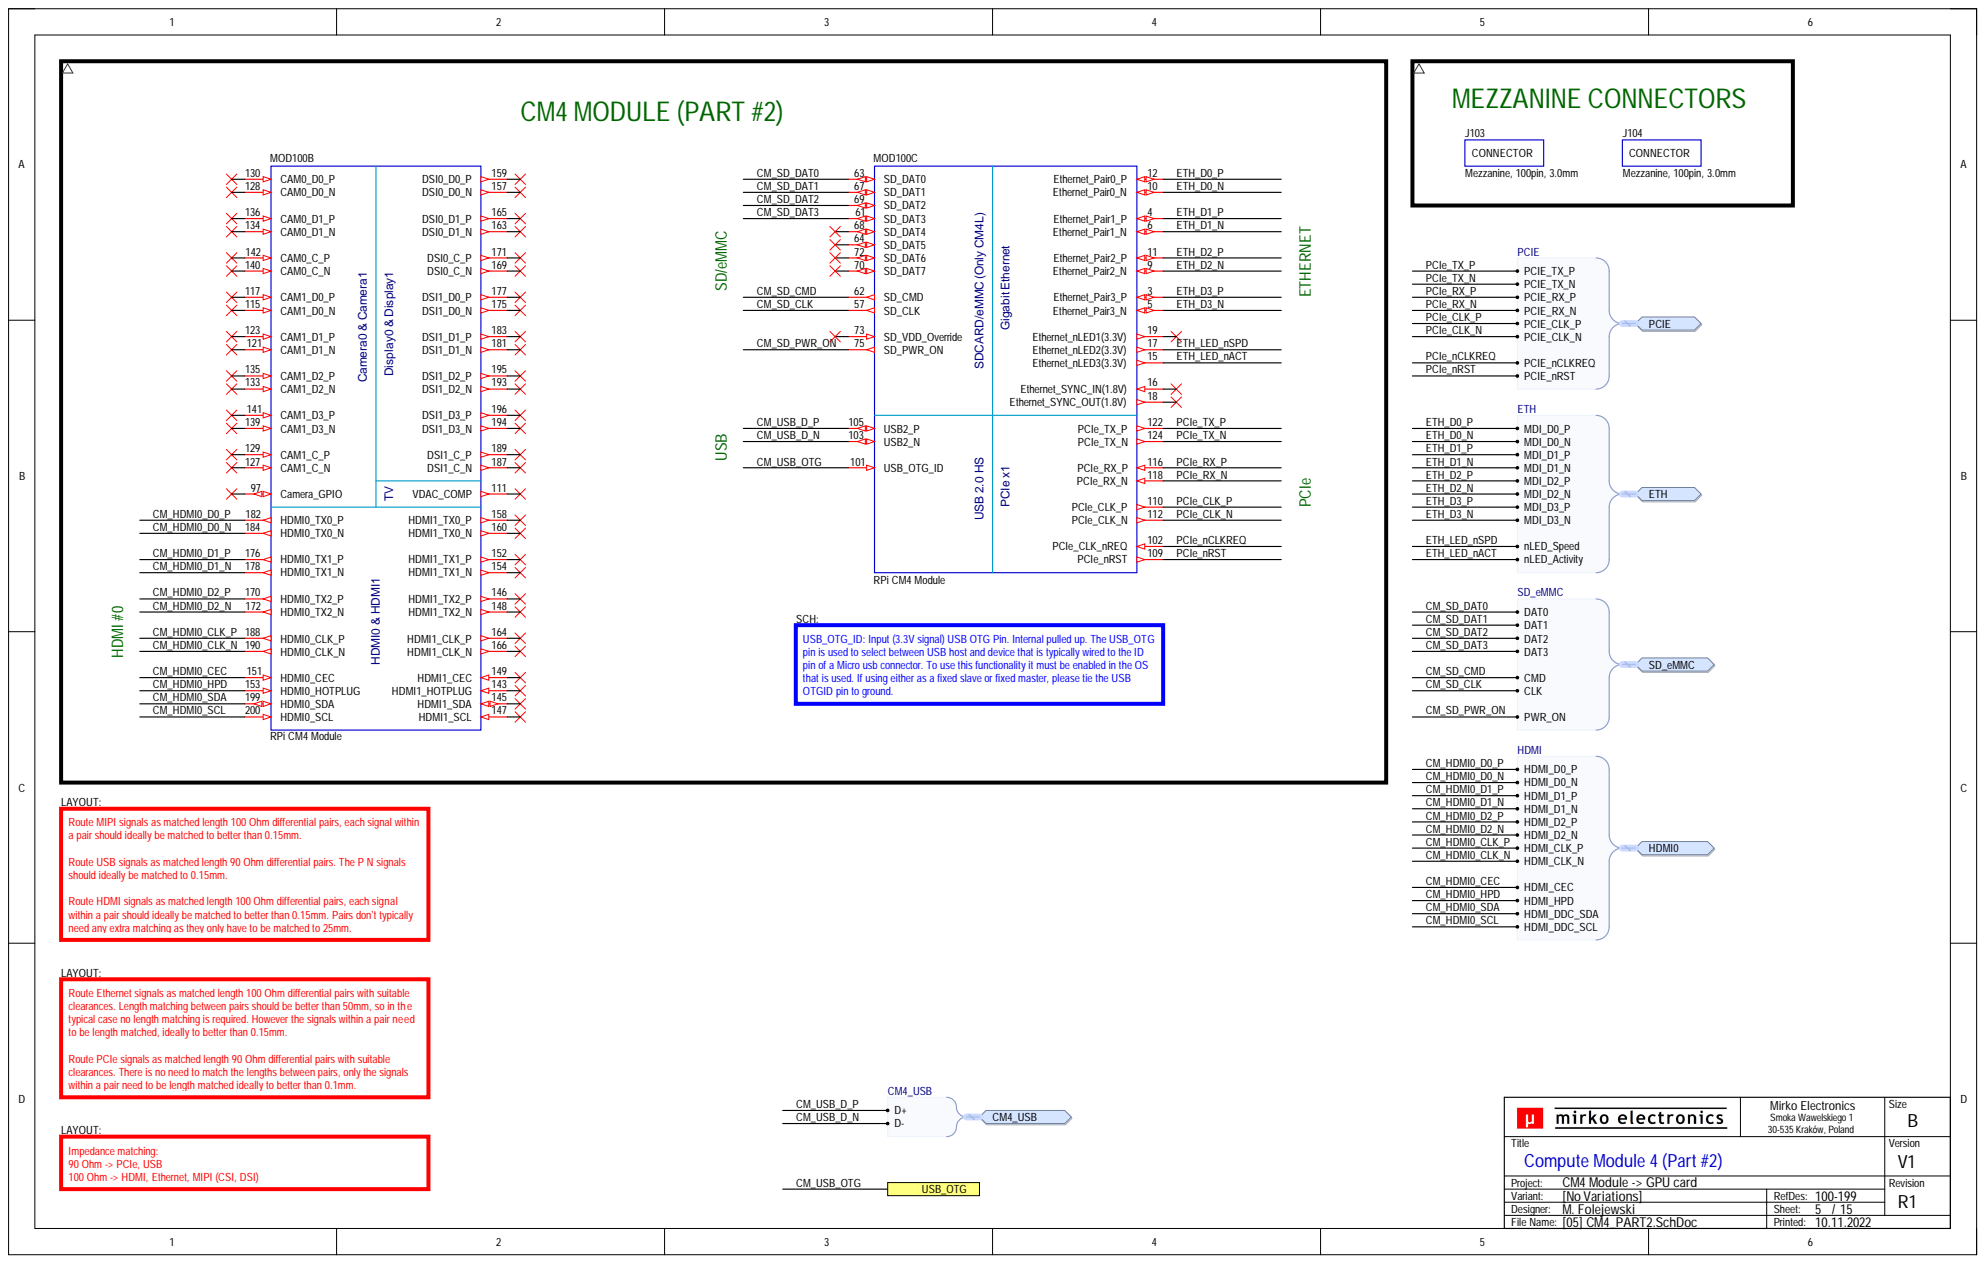
[picture p213: page 5]

SDCARD/eMMC(Only CM4L) USB 2.0 HS

SCH:
USB_OTG_ID: Input (3.3V signal) USB OTG Pin. Internal pulled up. The USB_OTG
pin is used to select between USB host and device that is typically wired to the ID
pin of a Micro usb connector. To use this functionality it must be enabled in the OS
that is used. If using either as a fixed slave or fixed master, please tie the USB
OTGID pin to ground.

LAYOUT:
Route MIPI signals as matched length 100 Ohm differential pairs, each signal within
a pair should ideally be matched to better than 0.15mm.

Route USB signals as matched length 90 Ohm differential pairs. The P N signals
should ideally be matched to 0.15mm.

Route HDMI signals as matched length 100 Ohm differential pairs, each signal
within a pair should ideally be matched to better than 0.15mm. Pairs don’t typically
need any extra matching as they only have to be matched to 25mm.

Route Ethernet signals as matched length 100 Ohm differential pairs with suitable
clearances. Length matching between pairs should be better than 50mm, so in the
typical case no length matching is required. However the signals within a pair need
to be length matched, ideally to better than 0.15mm.

Route PCIe signals as matched length 90 Ohm differential pairs with suitable
clearances. There is no need to match the lengths between pairs, only the signals
within a pair need to be length matched ideally to better than 0.1mm.

Impedance matching:
90 Ohm -> PCIe, USB
100 Ohm -> HDMI, Ethernet, MIPI (CSI, DSI)

Project: CM4 Module -> GPU card | Revision R1
Variant: [No Variations] | RefDes: 100-199
Designer: M. Folejewski
File Name: [05] CM4_PART2.SchDoc | Printed:

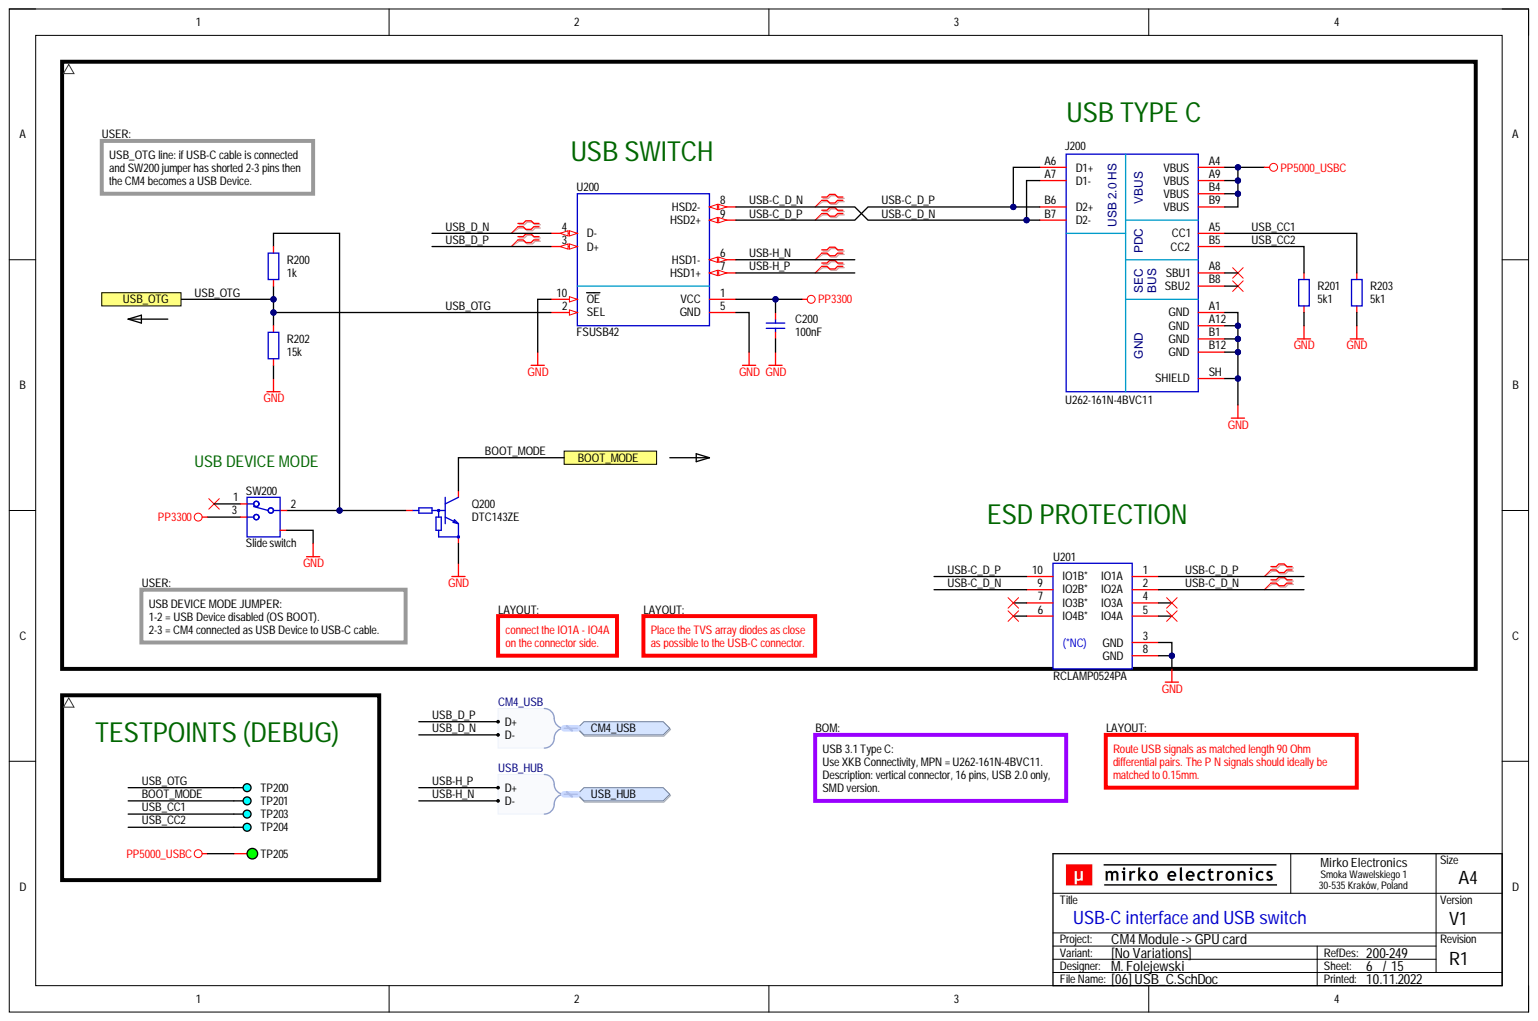
[picture p214: page 6]

USER:
USB_OTG line: if USB-C cable is connected
and SW200 jumper has shorted 2-3 pins then
the CM4 becomes a USB Device.

D1+ A6 | VBUS
D1- A7
D2+ B6 | B4

GND VBUS PDC SEC

USB DEVICE MODE JUMPER:
1-2 = USB Device disabled (OS BOOT).
2-3 = CM4 connected as USB Device to USB-C cable.

connect the IO1A - IO4A
on the connector side.

Place the TVS array diodes as close
as possible to the USB-C connector.

BOM:
USB 3.1 Type C:
Use XKB Connectivity, MPN = U262-161N-4BVC11.
Description: vertical connector, 16 pins, USB 2.0 only,
SMD version.

LAYOUT:
Route USB signals as matched length 90 Ohm
differential pairs. The P N signals should ideally be
matched to 0.15mm.

Mirko Electronics Smoka Wawelskiego 1 30-535 Kraków, Poland | Size A4

Title USB-C interface and USB switch | | Version V1

Project: CM4 Module -> GPU card | | Revision R1
Variant: [No Variations] | RefDes: 200-249

File Name: [06] USB_C.SchDoc | Printed:

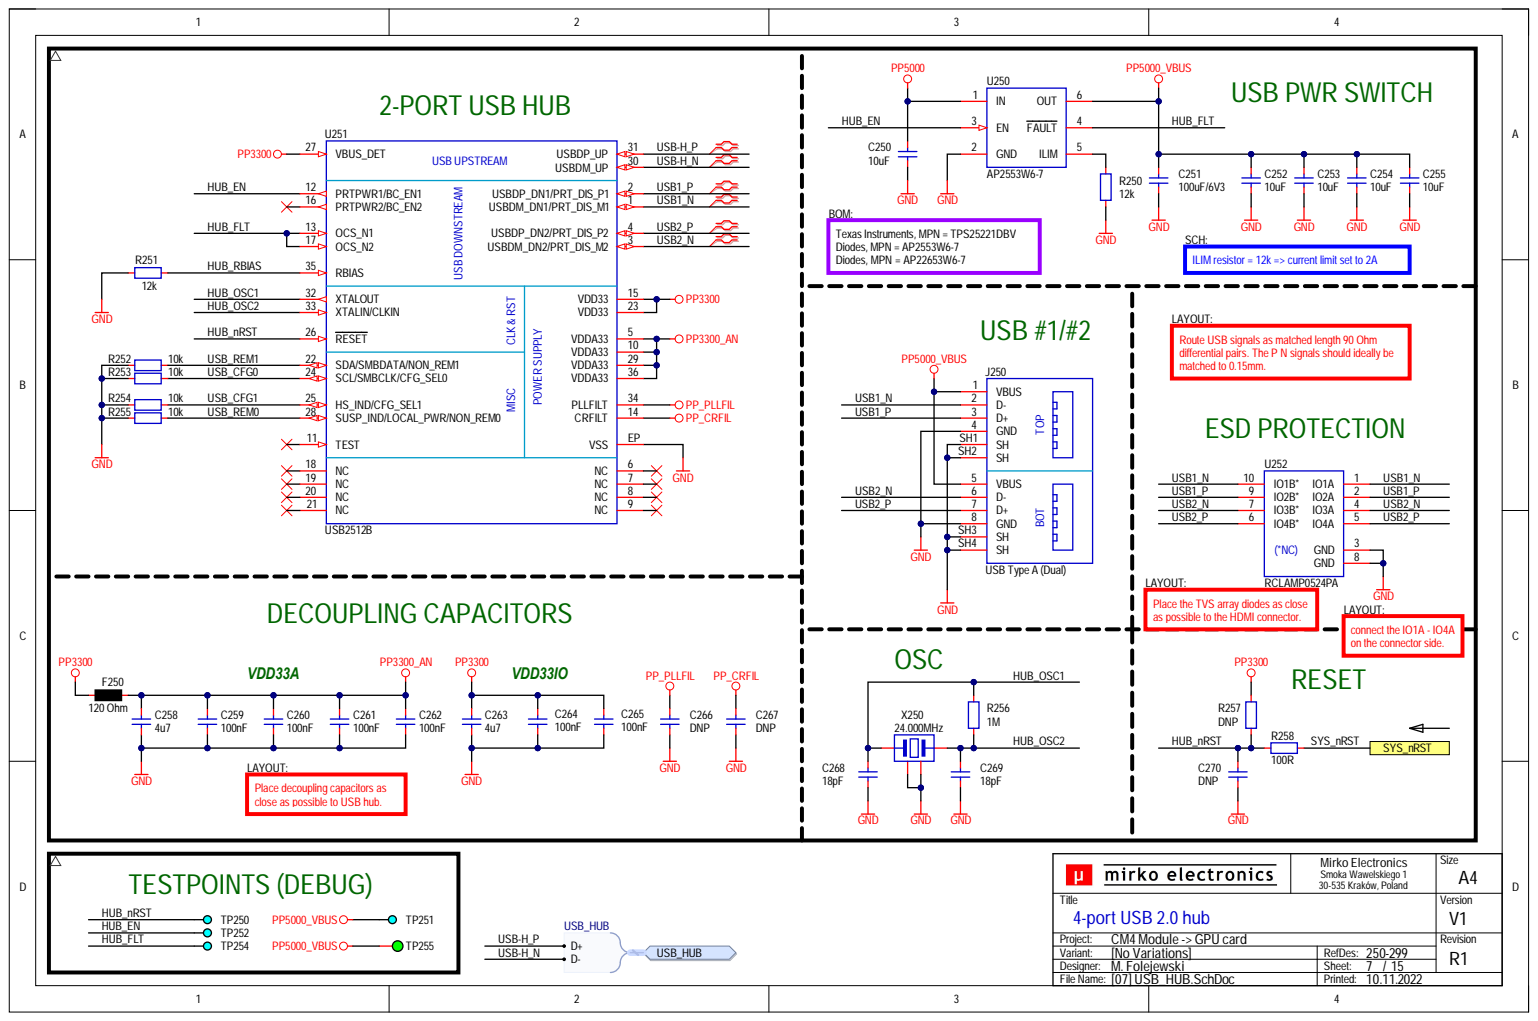
[picture p215: page 7]

SCH:
ILIM resistor = 12k => current limit set to 2A

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

D+ 3 D- 2 GND 4

Place the TVS array diodes as close
as possible to the HDMI connector.

Place decoupling capacitors as
close as possible to USB hub.

Mirko Electronics Smoka Wawelskiego 1

File Name: [07] USB_HUB.SchDoc | Printed:

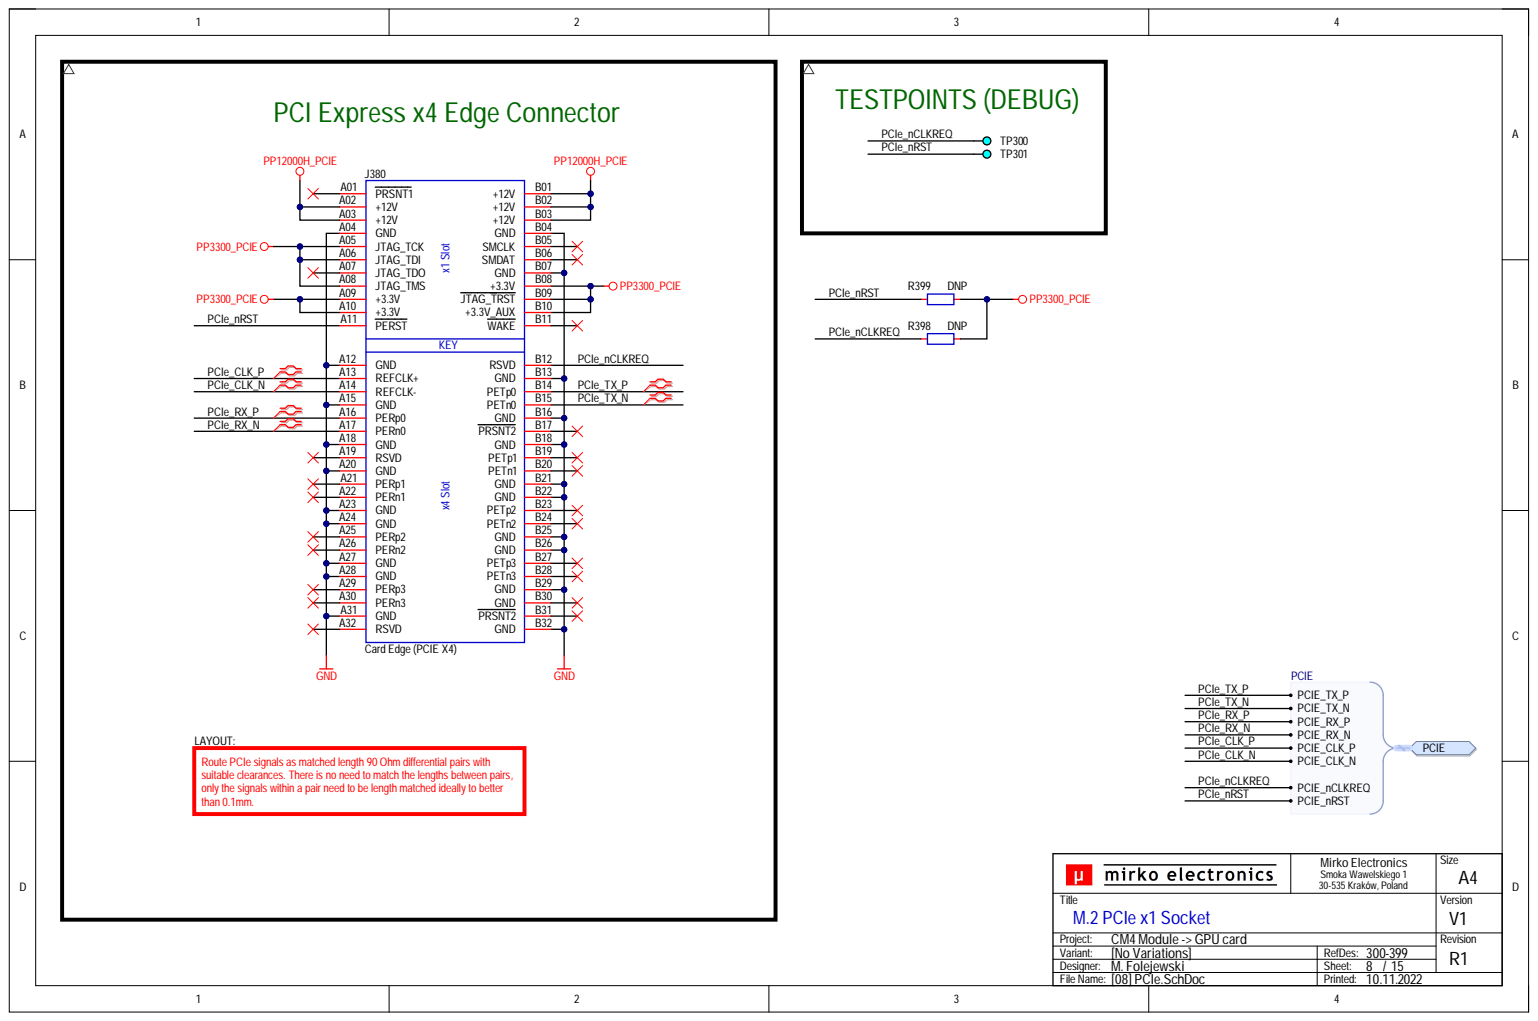
[picture p216: page 8]

PCI Express x4 Edge Connector

LAYOU
Route PCIe signals as matched le
suita
only the signals within a pair need to be le
tha

here is no need to match the le

ngth matched ideally to better

Mirko Electro n ics Smoka Wawelskiego 1 30-535 Kraków, Poland | Siz e A4

Titl e M.2 PCIe x1 Socket | | Ve rsion V1

Project: CM4 Module -> G PU card | | Revision R1
nt: [No V ariation s] Va ria | 300-399 RefDes:
Designer: M. Folejews k i | Sheet: 8 / 1 5
File Na me: [08] PCIe.S ch Doc | Printed : 1 0.1 1 . 2022

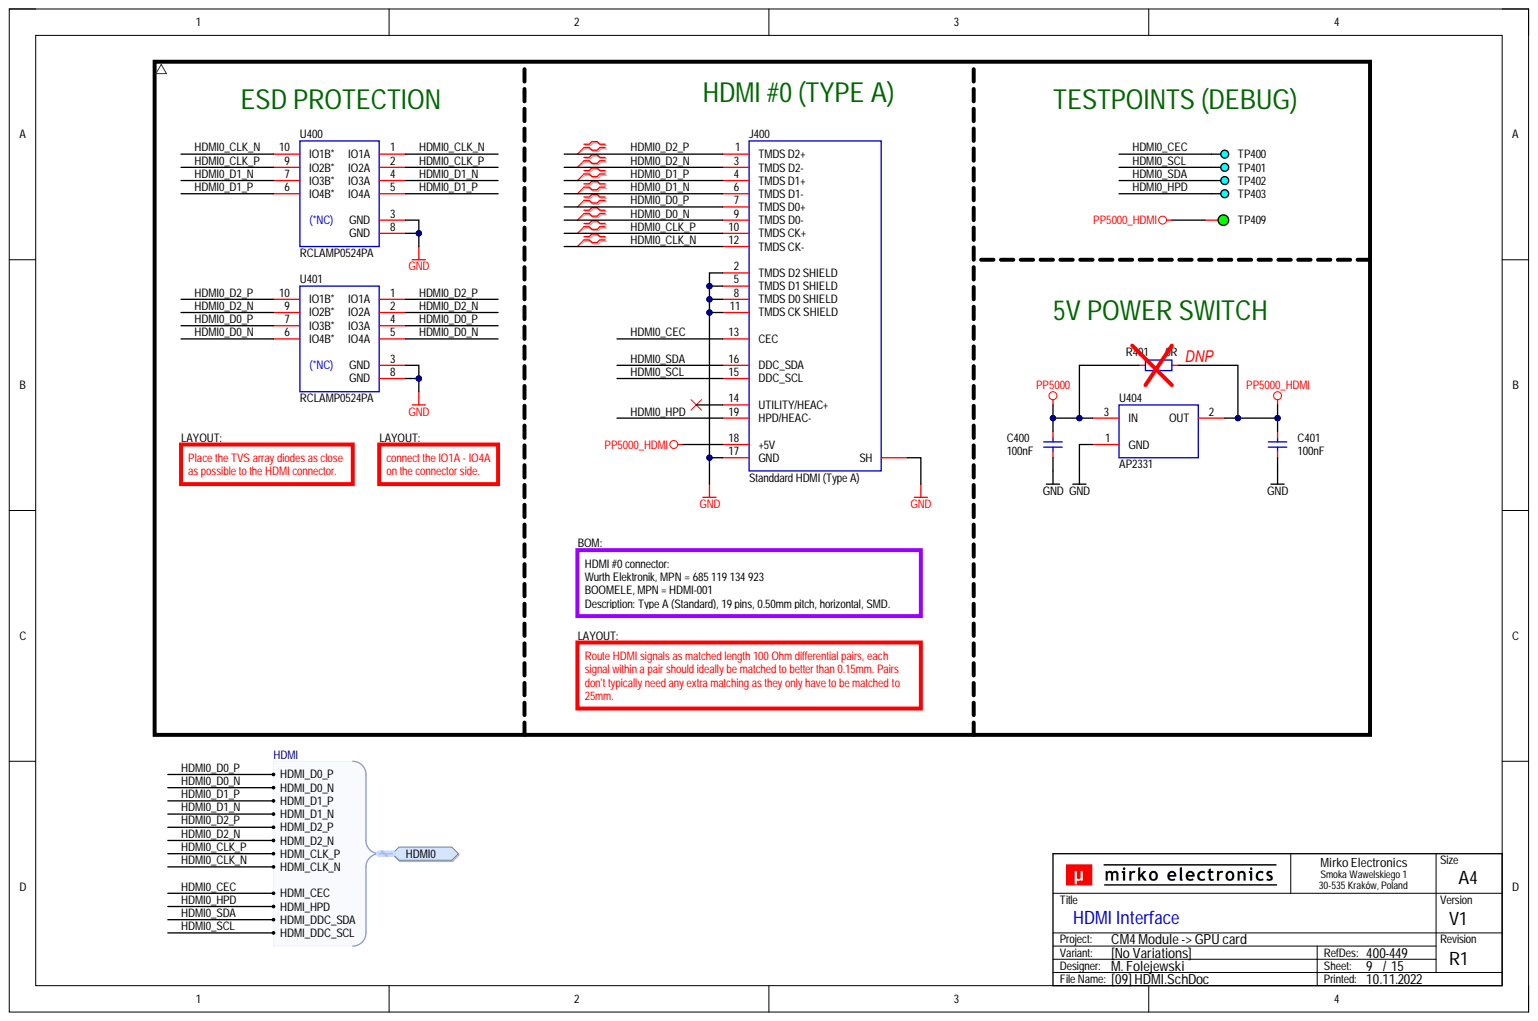
[picture p217: page 9]

Place the TVS array diodes as close
as possible to the HDMI connector.

connect the IO1A - IO4A
on the connector side.

BOM:
HDMI #0 connector:
Wurth Elektronik, MPN = 685 119 134 923
BOOMELE, MPN = HDMI-001
Description: Type A (Standard), 19 pins, 0.50mm pitch, horizontal, SMD.

LAYOUT:
Route HDMI signals as matched length 100 Ohm differential pairs, each
signal within a pair should ideally be matched to better than 0.15mm. Pairs
don’t typically need any extra matching as they only have to be matched to

Mirko Electronics Smoka Wawelskiego 1 30-535 Kraków, Poland | Size A4

Title HDMI Interface | | Version V1

Project: CM4 Module -> GPU card | | Revision R1
Variant: [No Variations] | RefDes: 400-449

File Name: [09] HDMI.SchDoc | Printed:

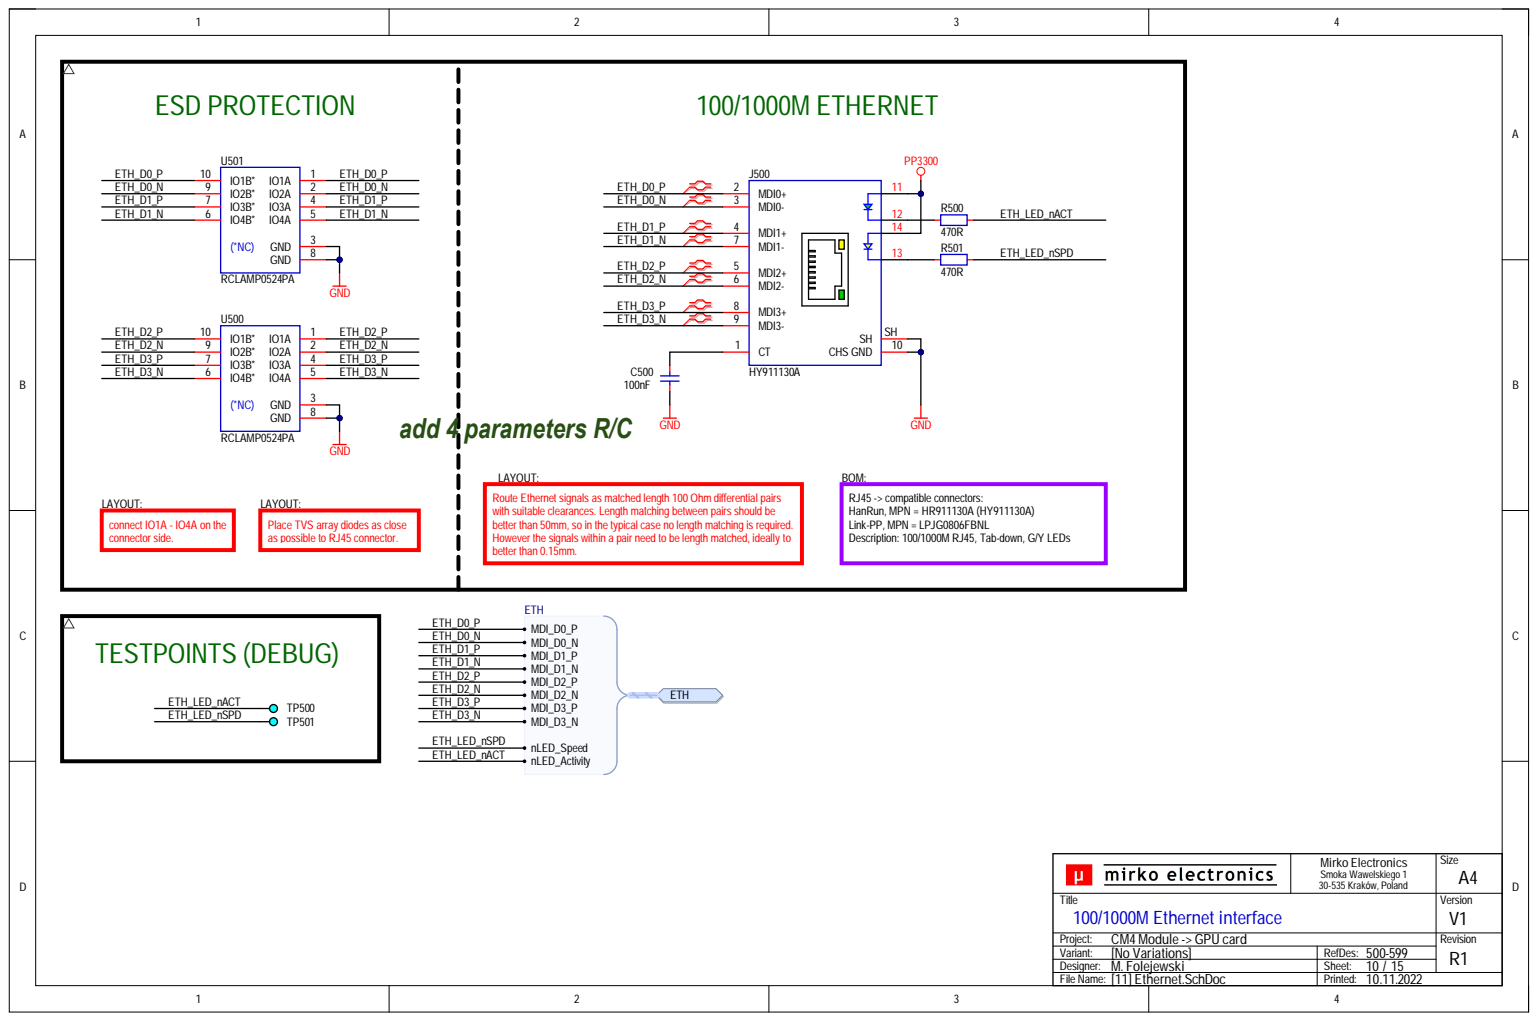
[picture p218: page 10]

LAYOUT:
Route Ethernet signals as matched length 100 Ohm differential pairs
with suitable clearances. Length matching between pairs should be
better than 50mm, so in the typical case no length matching is required.
However the signals within a pair need to be length matched, ideally to
better than 0.15mm.

BOM:
RJ45 -> compatible connectors:
HanRun, MPN = HR911130A (HY911130A)
Link-PP, MPN = LPJG0806FBNL
Description: 100/1000M RJ45, Tab-down, G/Y LEDs

Place TVS array diodes as close
as possible to RJ45 connector.

Mirko Electronics Smoka Wawelskiego 1 30-535 Kraków, Poland | Size A4

Title 100/1000M Ethernet interface | | Version V1

Project: CM4 Module -> GPU card | | Revision R1
Variant: [No Variations] | RefDes: 500-599

File Name: [11] Ethernet.SchDoc | Printed:

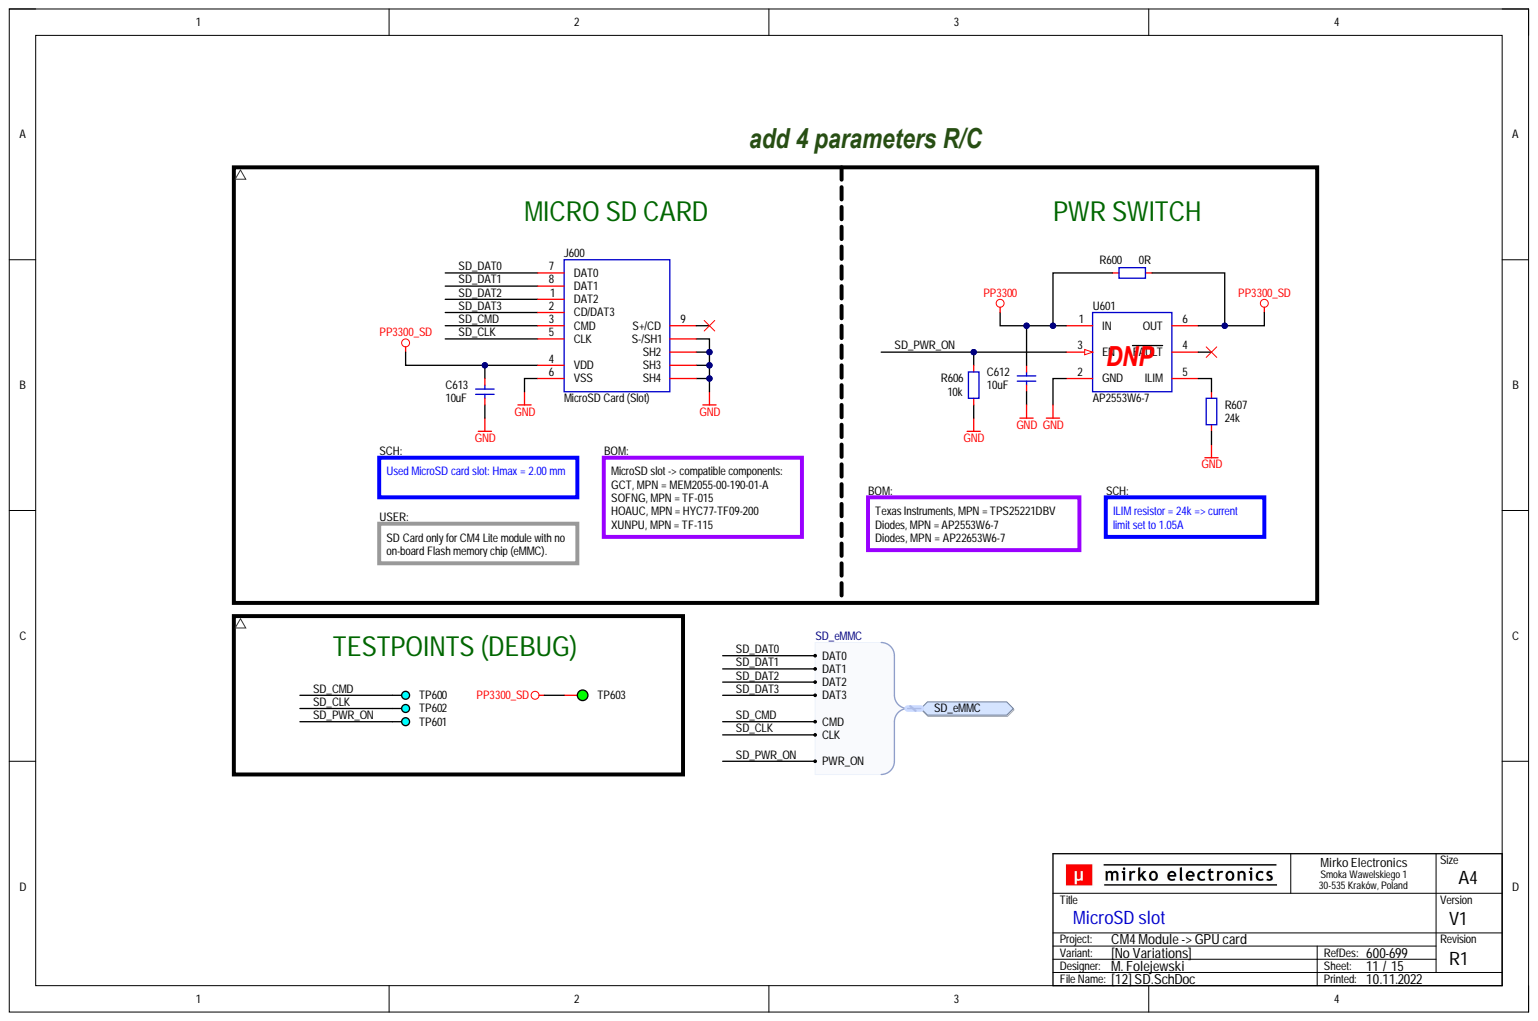
[picture p219: page 11]

SCH:
Used MicroSD card slot: Hmax = 2.00 mm

BOM:
MicroSD slot -> compatible components:
GCT, MPN = MEM2055-00-190-01-A
SOFNG, MPN = TF-015
HOAUC, MPN = HYC77-TF09-200
XUNPU, MPN = TF-115

USER:
SD Card only for CM4 Lite module with no
on-board Flash memory chip (eMMC).

Mirko Electronics Smoka Wawelskiego 1 30-535 Kraków, Poland | Size A4

Title MicroSD slot | | Version V1

Project: CM4 Module -> GPU card | | Revision R1
Variant: [No Variations] | RefDes: 600-699

File Name: [12] SD.SchDoc | Printed:

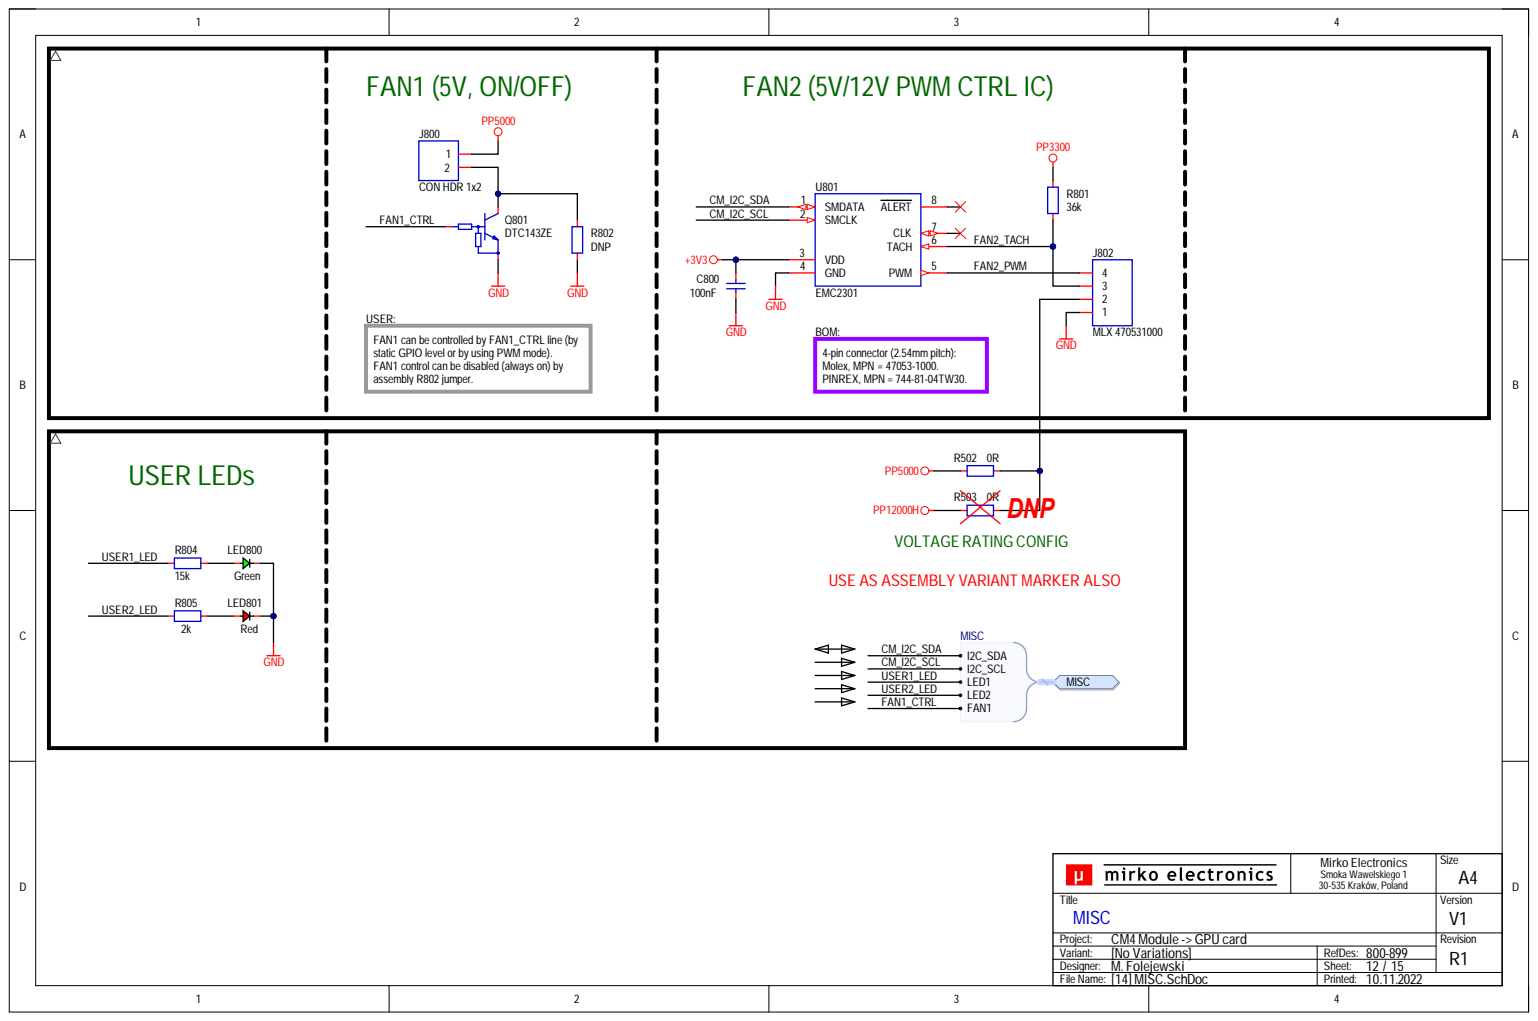
[picture p220: page 12]

USER:
FAN1 can be controlled by FAN1_CTRL line (by
static GPIO level or by using PWM mode).
FAN1 control can be disabled (always on) by
assembly R802 jumper.

USE AS ASSEMBLY VARIANT MARKER ALSO

Mirko Electronics Smoka Wawelskiego 1 30-535 Kraków, Poland | Size A4

Title MISC | | Version V1

Project: CM4 Module -> GPU card | | Revision R1
Variant: [No Variations] | RefDes: 800-899

File Name: [14] MISC.SchDoc | Printed:

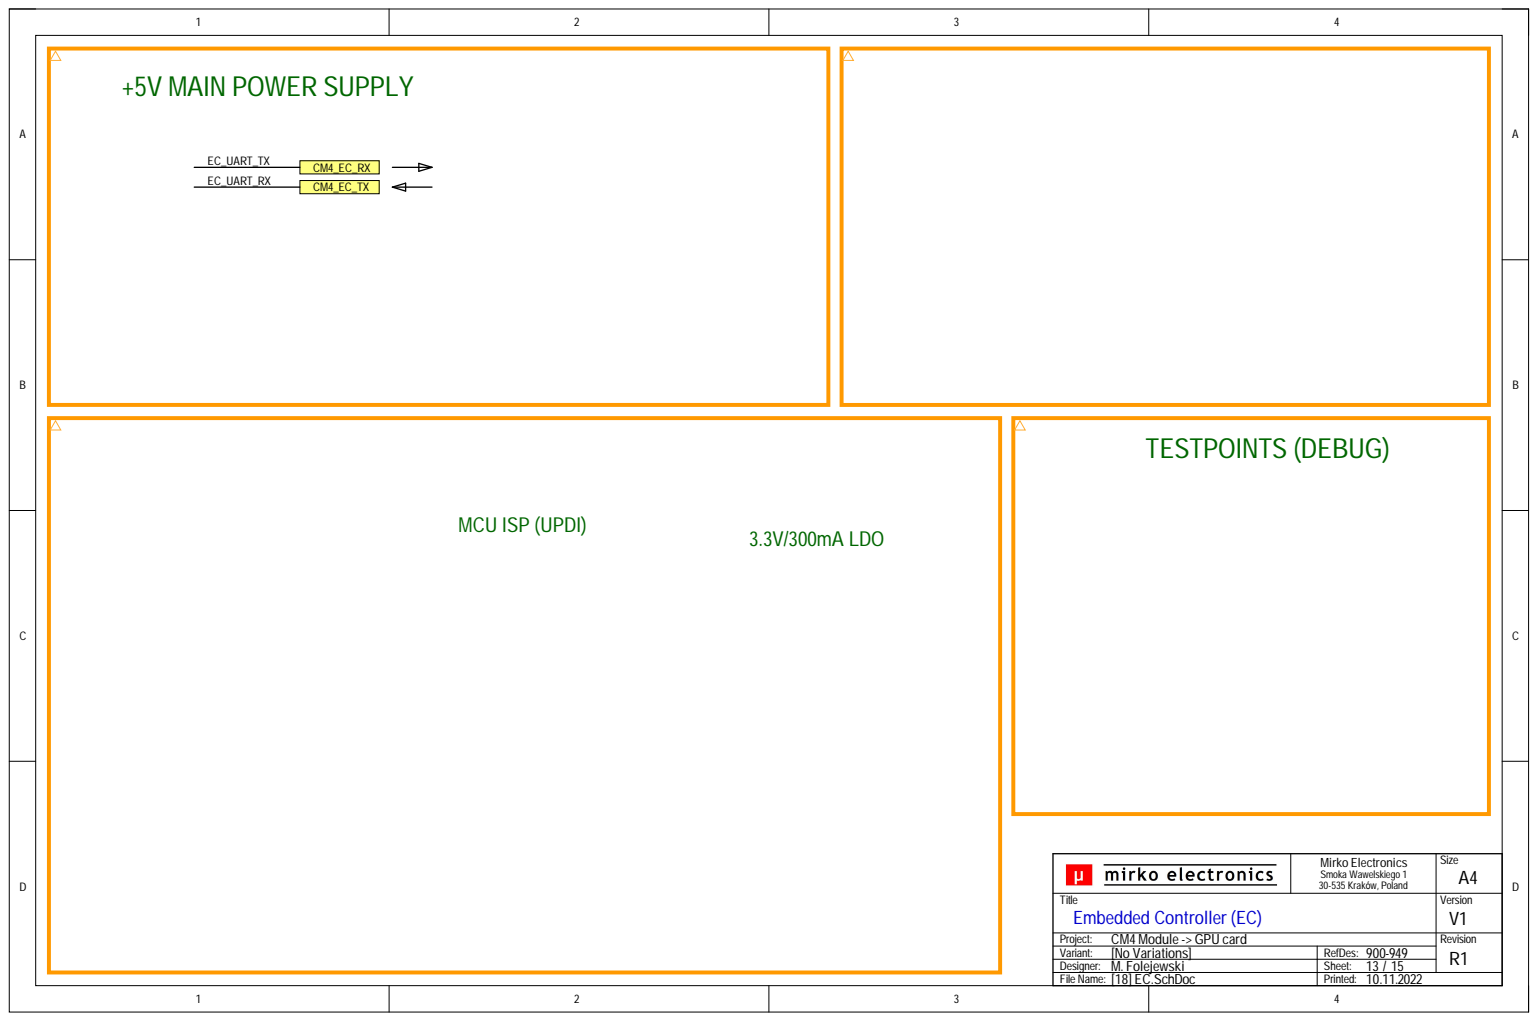
[picture p221: page 13]

3.3V/300mA LDO MCU ISP (UPDI)

Mirko Electro n ics Smoka Wawelskiego 1 30-535 Kraków, Poland | Siz e A4

Titl e Embedded Control ler (EC) | | Ve rsion V1

Project: CM4 Module -> G PU card | | Revision R1
nt: [No V ariation s] Va ria | 900-949 RefDes:
Designer: M. Folejews k i | Sheet: 1 3 / 1 5
File Na me: [1 8] EC.S ch Doc | Printed : 1 0.1 1 . 2022

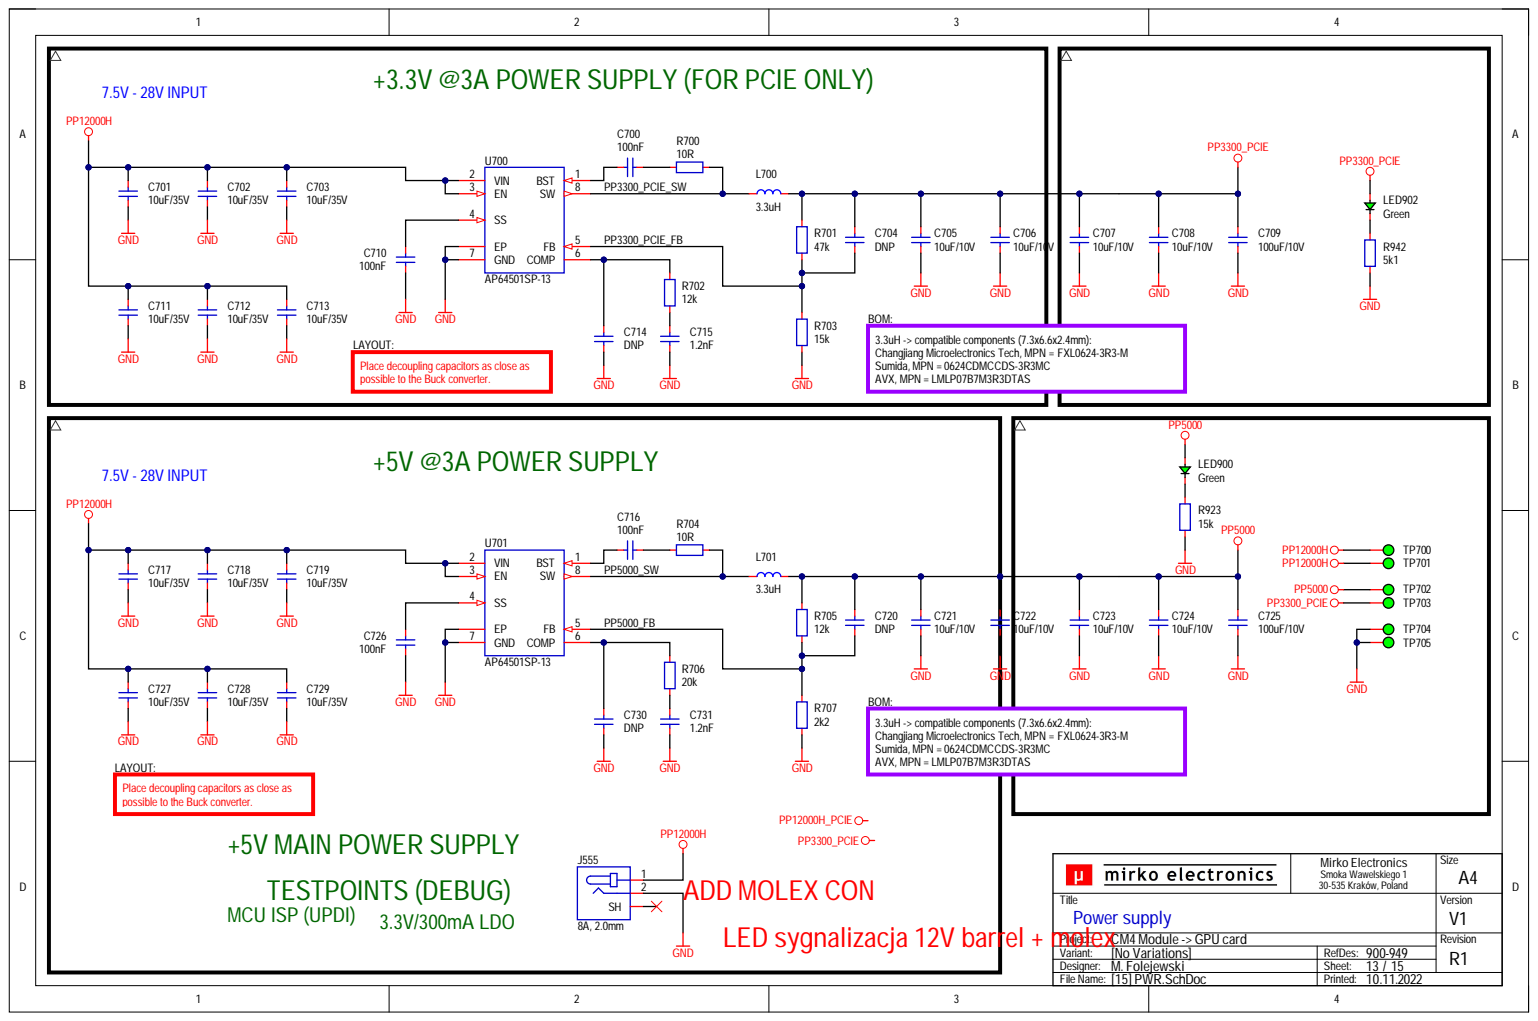
[picture p222: page 14]

+3.3V @3A POWER SUPPLY (FOR PCIE ONLY) 7.5V - 28V INPUT

BOM:
3.3uH -> compatible components (7.3x6.6x2.4mm):
Changjiang Microelectronics Tech, MPN = FXL0624-3R3-M
Sumida, MPN = 0624CDMCCDS-3R3MC
AVX, MPN = LMLP07B7M3R3DTAS

LAYOUT:
Place decoupling capacitors as close as
possible to the Buck converter.

Mirko Electronics Smoka Wawelskiego 1

30-535 Kraków, Poland TESTPOINTS (DEBUG)
MCU ISP (UPDI) 3.3V/300mA LDO

ADD MOLEX CON
LED sygnalizacja 12V barrel + molex

File Name: [15] PWR.SchDoc | Printed:

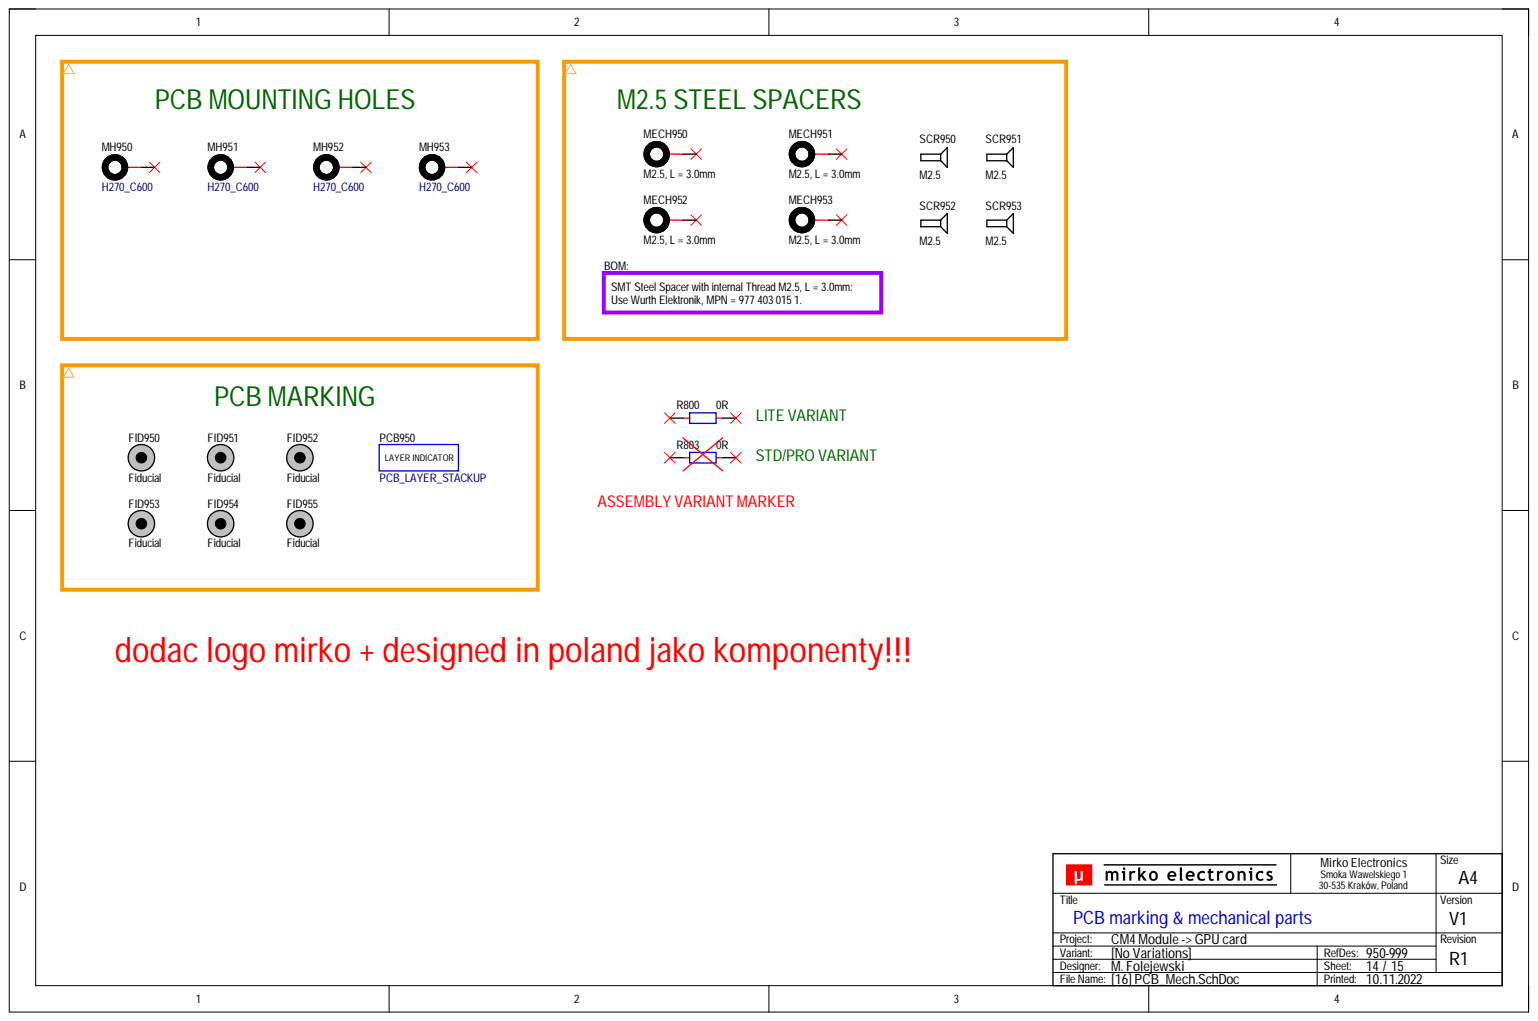
[picture p223: page 15]

BOM:
SMT Steel Spacer with internal Thread M2.5, L = 3.0mm:
Use Wurth Elektronik, MPN = 977 403 015 1.

dodac logo mirko + designed in poland jako komponenty!!!

Mirko Electronics Smoka Wawelskiego 1 30-535 Kraków, Poland | Size A4

Title PCB marking & mechanical parts | | Version V1

Project: CM4 Module -> GPU card | | Revision R1
Variant: [No Variations] | RefDes: 950-999

File Name: [16] PCB_Mech.SchDoc | Printed:

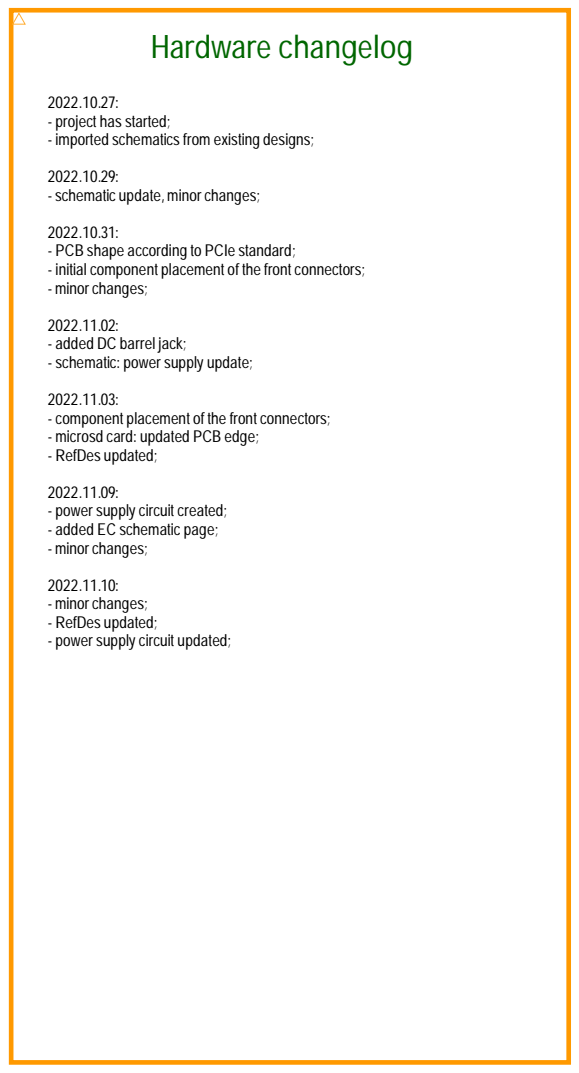
[picture p224: page 16]

- project has started;
- imported schematics from existing designs;

- schematic update, minor changes;

- PCB shape according to PCIe standard;
- initial component placement of the front connectors;
- minor changes;

- added DC barrel jack;
- schematic: power supply update;

- component placement of the front connectors;
- microsd card: updated PCB edge;
- RefDes updated;

- power supply circuit created;
- added EC schematic page;

- power supply circuit updated;

Mirko Electronics Smoka Wawelskiego 1 30-535 Kraków, Poland | Size A4

Title Hardware changelog | | Version V1

Revision R1
Variant: [No Variations]

File Name: [17] Changelog.SchDoc | Printed:
