geerlingguy/pi4gpu/schematics/deprecated/CM4GPU_v1_Schematic_20221103.pdf

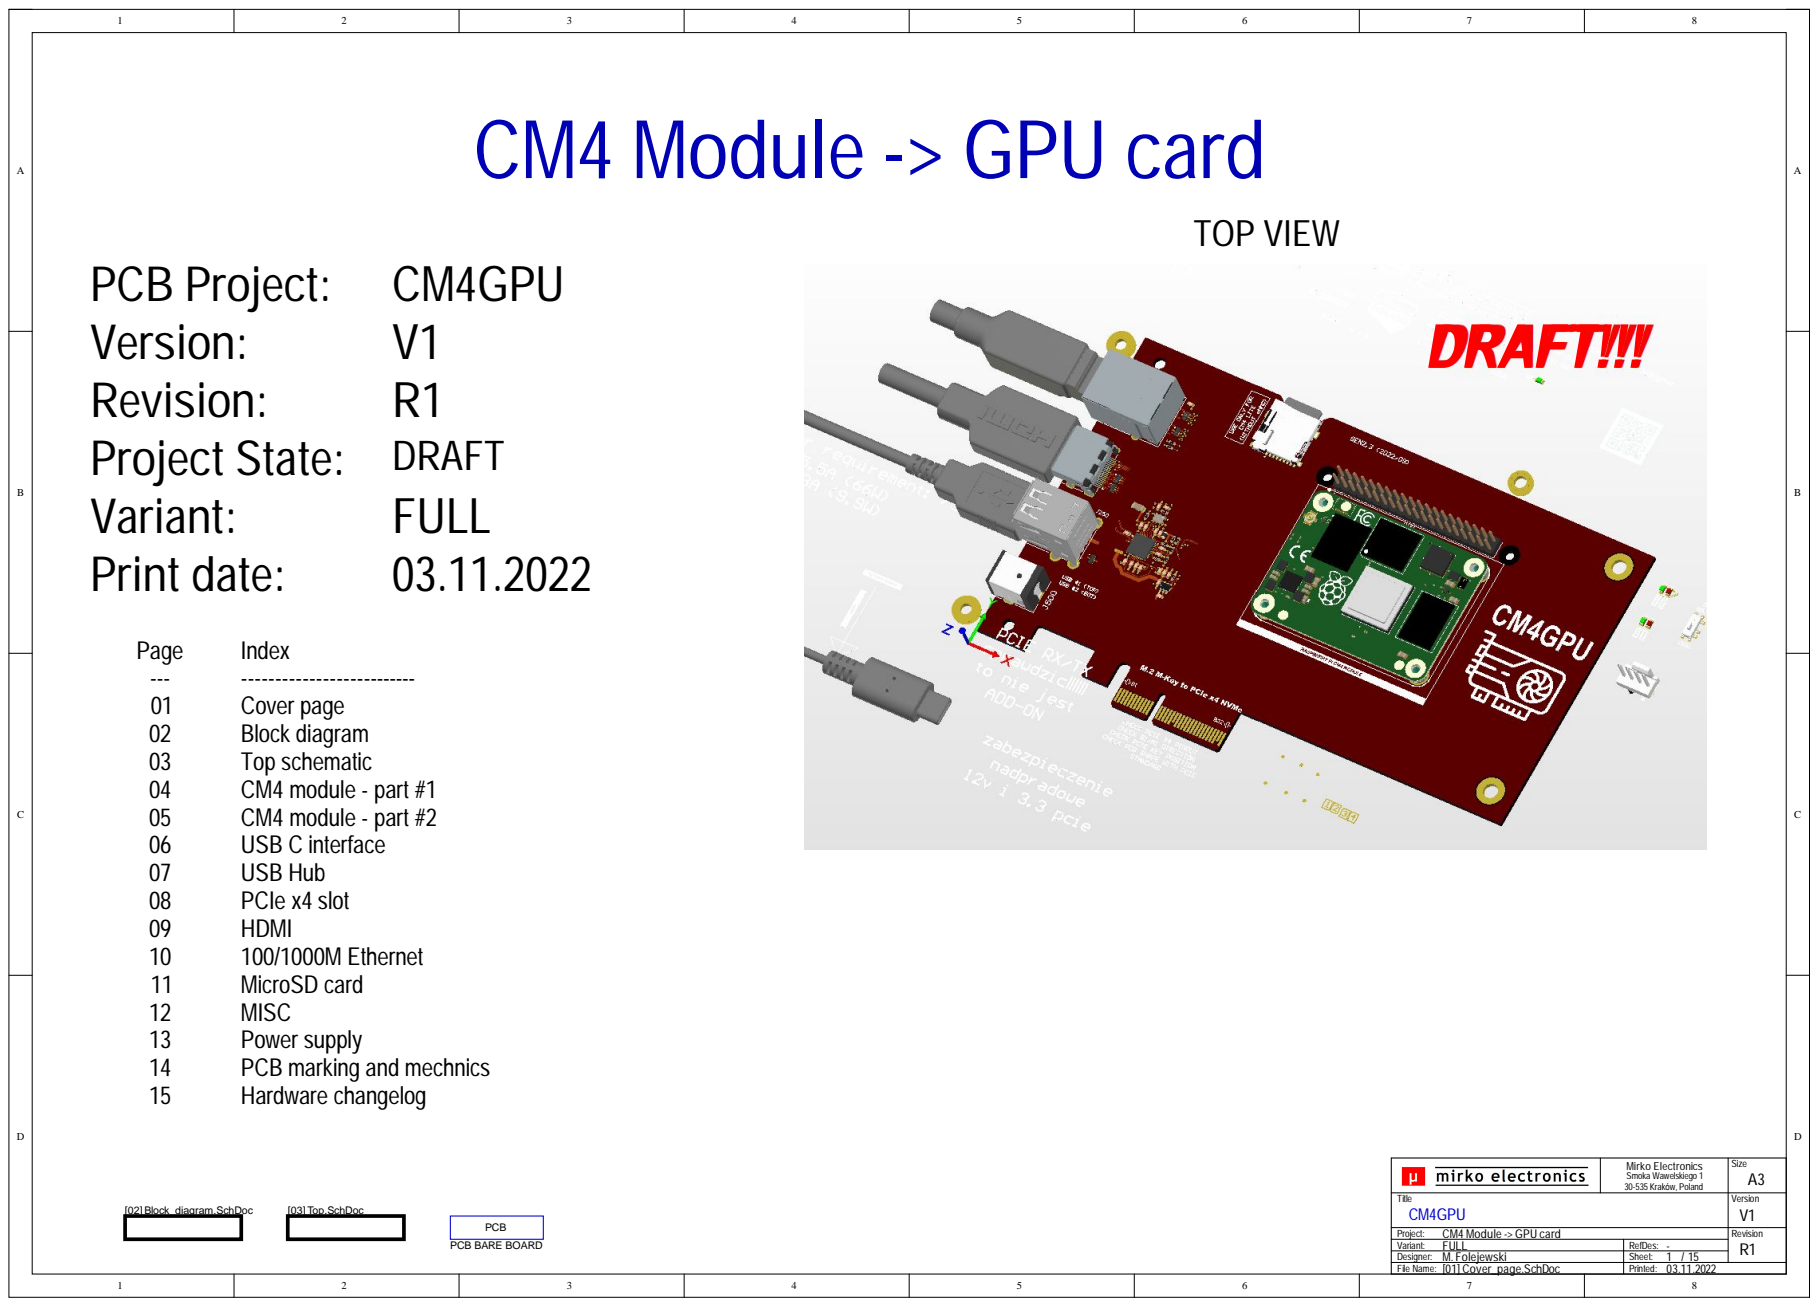
[picture p225: page 1]

Mirko Electronics Smoka Wawelskiego 1 30-535 Kraków, Poland | Size A3

Title CM4GPU | | Version V1

Project: CM4 Module -> GPU card | | Revision R1
Variant: FULL | RefDes: -
Designer: M. Folejewski
File Name: [01] Cover_page.SchDoc | Printed:

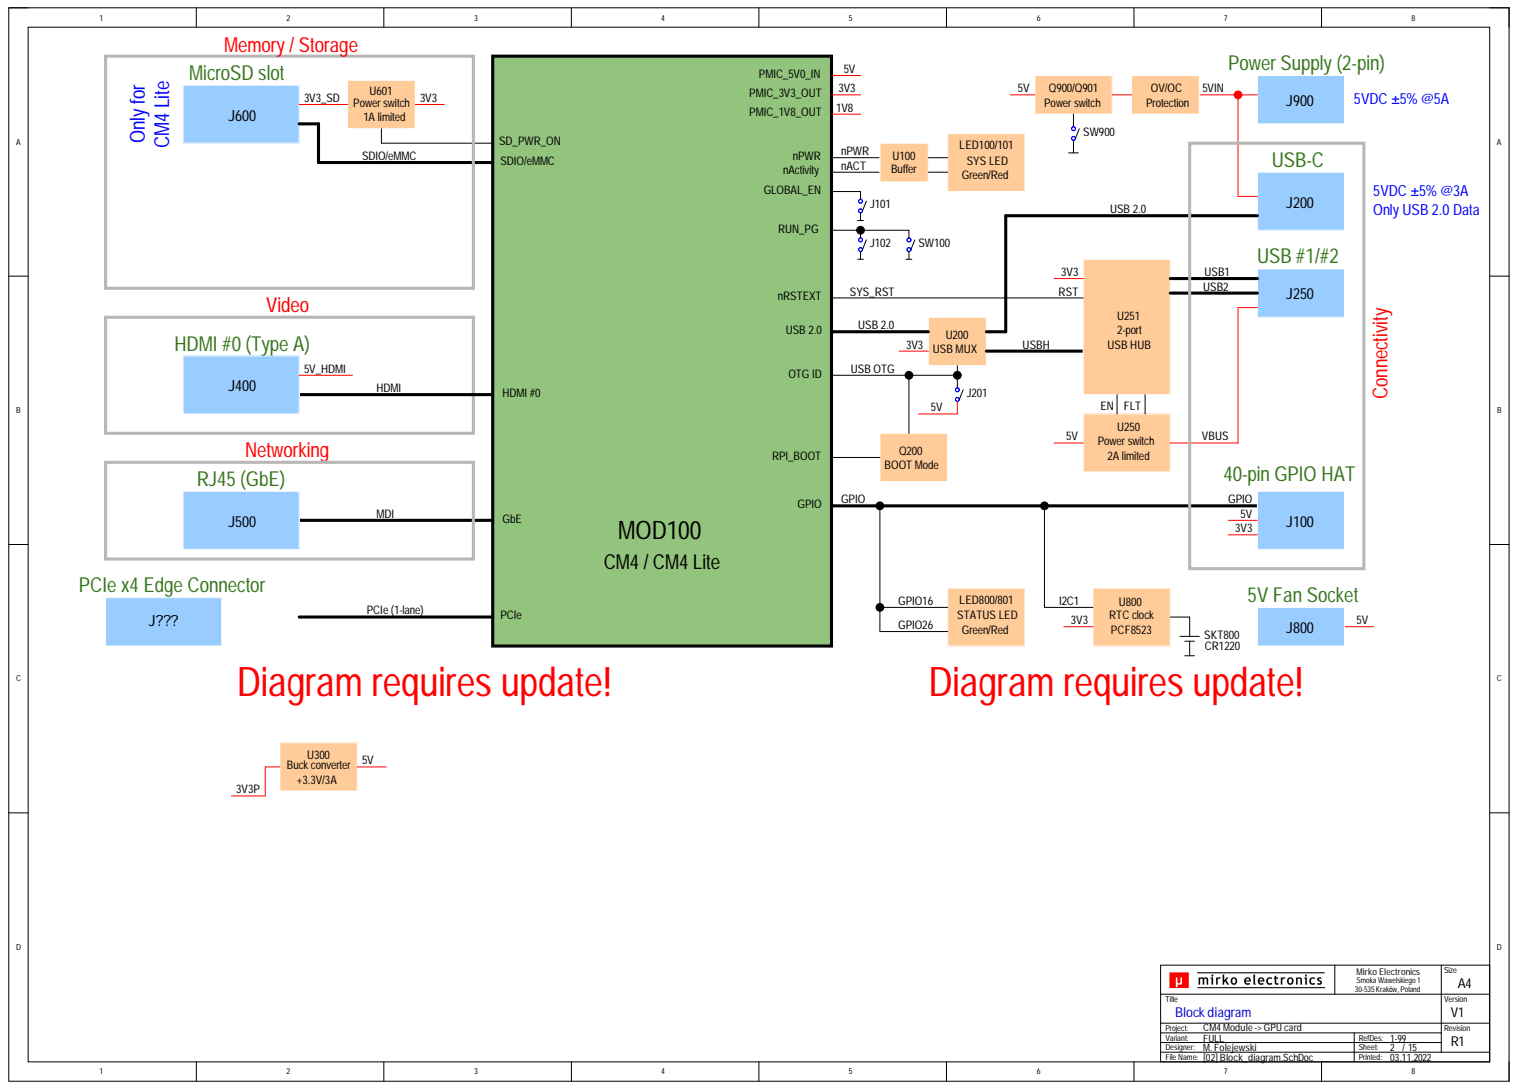
[picture p226: page 2]

SDIO/eMMC

USB OTG OTG ID

Mirko Electronics Smoka Wawelskiego 1 30-535 Kraków, Poland | Size A4

Title Block diagram | | Version V1

Project: CM4 Module -> GPU card | | Revision R1
Variant: FULL | RefDes: 1-99

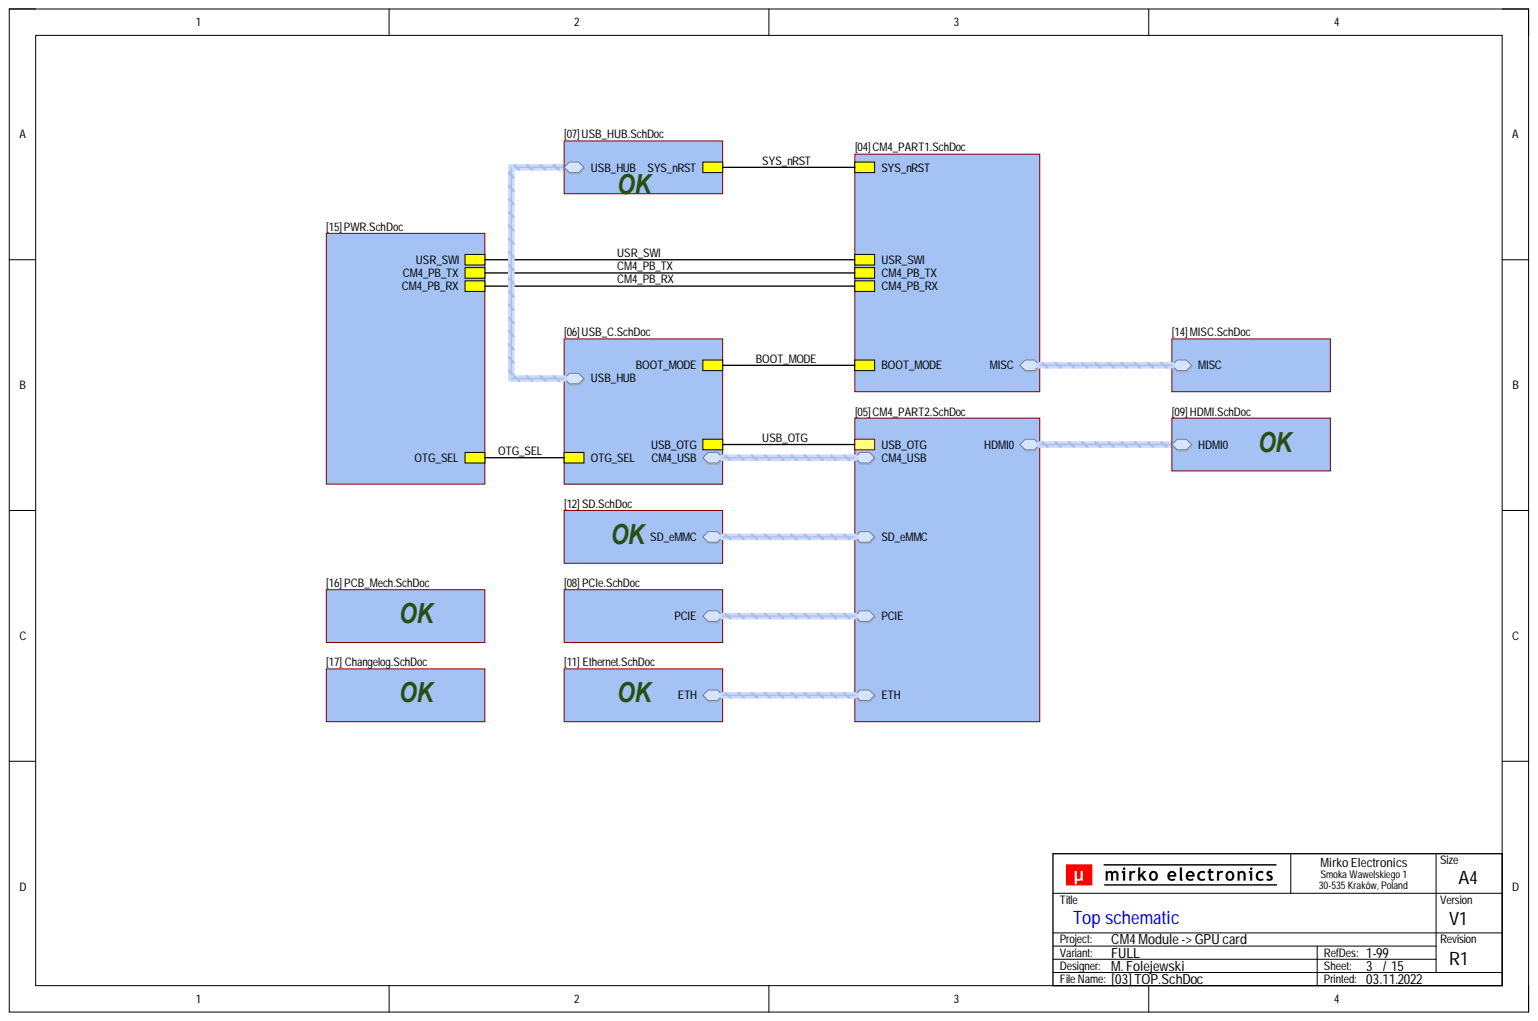
[picture p227: page 3]

CM4_PB_TX
CM4_PB_RX

[06] USB_C.SchDoc

Mirko Electronics Smoka Wawelskiego 1 30-535 Kraków, Poland | Size A4

Title Top schematic | | Version V1

Project: CM4 Module -> GPU card | | Revision R1
Variant: FULL | RefDes: 1-99

Sheet: 3 15 /

File Name: [03] TOP.SchDoc | Printed: 03.11.2022

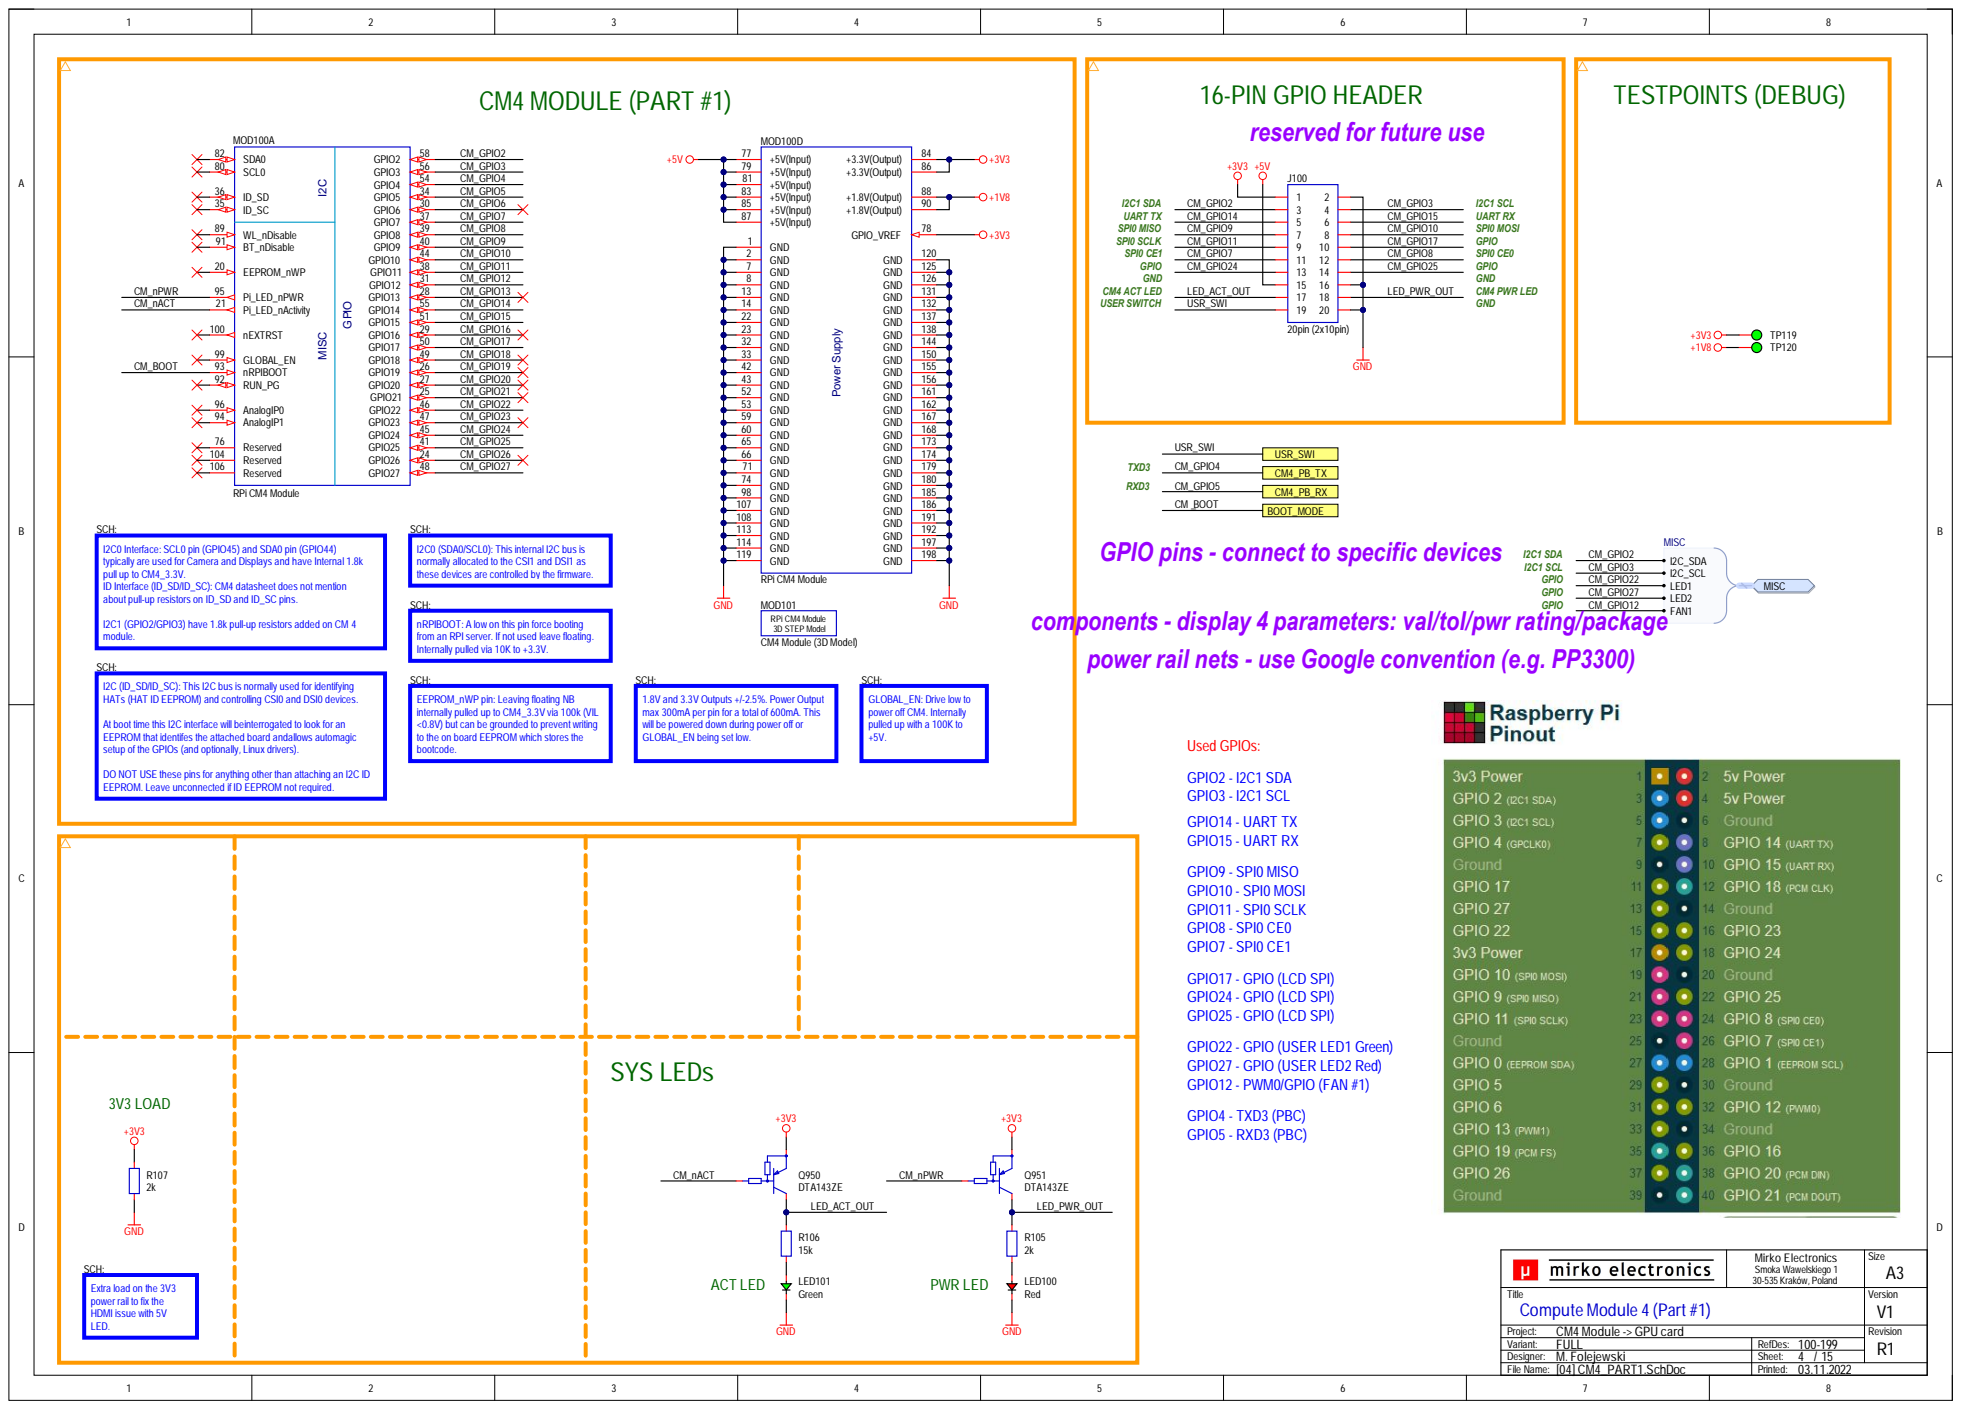
[picture p228: page 4]

16-PIN GPIO HEADER
reserved for future use

SCH:
I2C0 Interface: SCL0 pin (GPIO45) and SDA0 pin (GPIO44)
typically are used for Camera and Displays and have Internal 1.8k
pull up to CM4_3.3V.
ID Interface (ID_SD/ID_SC): CM4 datasheet does not mention
about pull-up resistors on ID_SD and ID_SC pins.

I2C0 (SDA0/SCL0): This internal I2C bus is
normally allocated to the CSI1 and DSI1 as
these devices are controlled by the firmware.

GPIO pins - connect to specific devices

nRPIBOOT: A low on this pin force booting
from an RPI server. If not used leave floating.
Internally pulled via 10K to +3.3V.

components - display 4 parameters: val/tol/pwr rating/package
power rail nets - use Google convention (e.g. PP3300)

I2C1 (GPIO2/GPIO3) have 1.8k pull-up resistors added on CM4
module.

I2C (ID_SD/ID_SC): This I2C bus is normally used for identifying
HATs (HAT ID EEPROM) and controlling CSI0 and DSI0 devices.

EEPROM_nWP pin: Leaving floating NB
internally pulled up to CM4_3.3V via 100k (VIL
<0.8V) but can be grounded to prevent writing
to the on board EEPROM which stores the
bootcode.

1.8V and 3.3V Outputs +/-2.5%. Power Output
max 300mA per pin for a total of 600mA. This
will be powered down during power off or
GLOBAL_EN being set low.

GLOBAL_EN: Drive low to
power off CM4. Internally
pulled up with a 100K to

At boot time this I2C interface will beinterrogated to look for an
EEPROM that identifes the attached board andallows automagic
setup of the GPIOs (and optionally, Linux drivers).

DO NOT USE these pins for anything other than attaching an I2C ID
EEPROM. Leave unconnected if ID EEPROM not required.

Mirko Electronics Smoka Wawelskiego 1 30-535 Kraków, Poland | Size A3

Extra load on the 3V3
power rail to fix the
HDMI issue with 5V
LED.

Title Compute Module 4 (Part #1) | | Version V1

Project: CM4 Module -> GPU card | | Revision R1
Variant: FULL | RefDes: 100-199

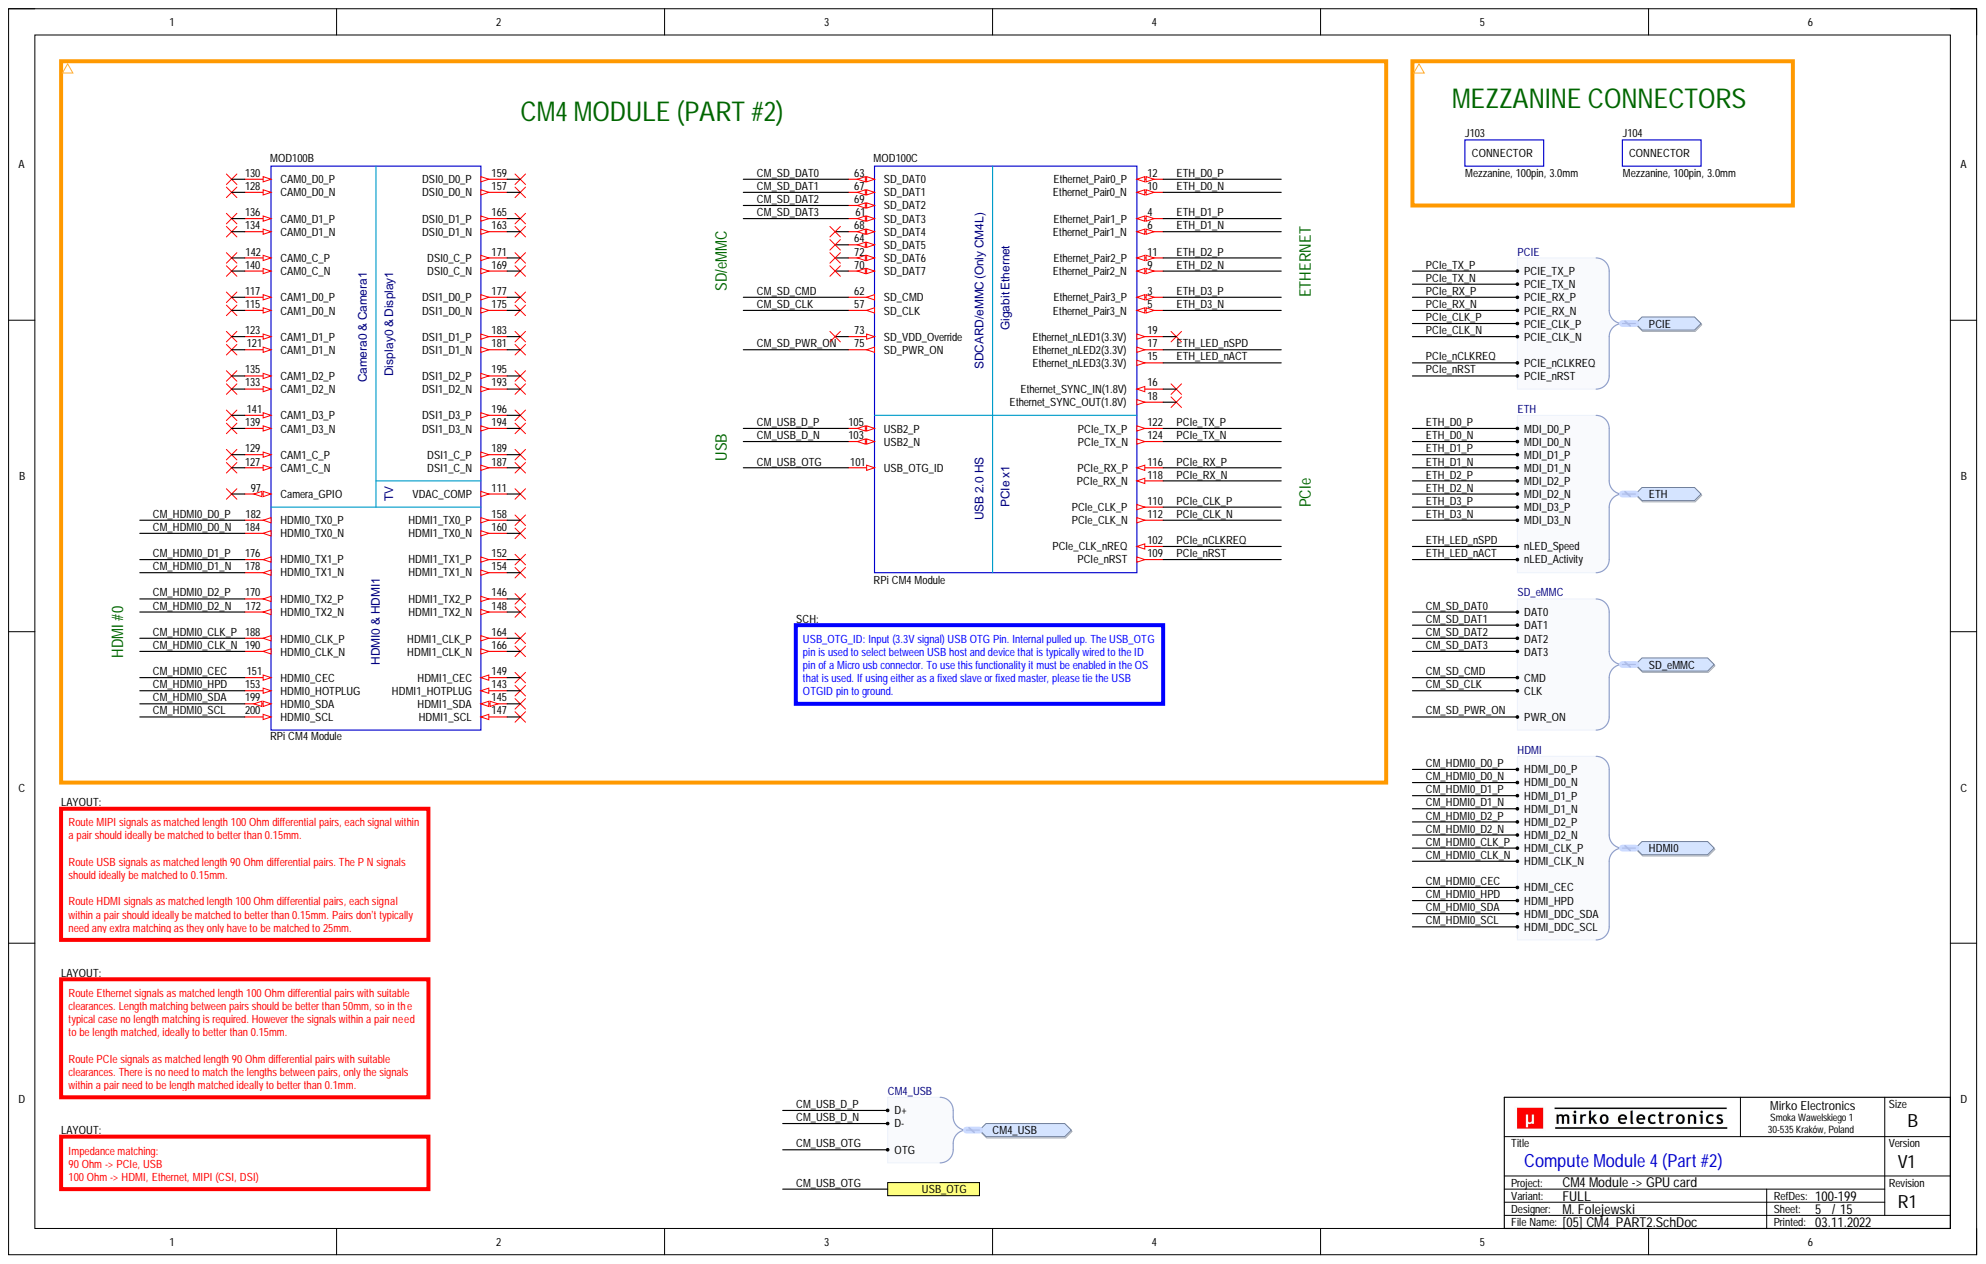
[picture p229: page 5]

SDCARD/eMMC(Only CM4L) USB 2.0 HS

SCH:
USB_OTG_ID: Input (3.3V signal) USB OTG Pin. Internal pulled up. The USB_OTG
pin is used to select between USB host and device that is typically wired to the ID
pin of a Micro usb connector. To use this functionality it must be enabled in the OS
that is used. If using either as a fixed slave or fixed master, please tie the USB
OTGID pin to ground.

LAYOUT:
Route MIPI signals as matched length 100 Ohm differential pairs, each signal within
a pair should ideally be matched to better than 0.15mm.

Route USB signals as matched length 90 Ohm differential pairs. The P N signals
should ideally be matched to 0.15mm.

Route HDMI signals as matched length 100 Ohm differential pairs, each signal
within a pair should ideally be matched to better than 0.15mm. Pairs don’t typically
need any extra matching as they only have to be matched to 25mm.

Route Ethernet signals as matched length 100 Ohm differential pairs with suitable
clearances. Length matching between pairs should be better than 50mm, so in the
typical case no length matching is required. However the signals within a pair need
to be length matched, ideally to better than 0.15mm.

Route PCIe signals as matched length 90 Ohm differential pairs with suitable
clearances. There is no need to match the lengths between pairs, only the signals
within a pair need to be length matched ideally to better than 0.1mm.

Impedance matching:
90 Ohm -> PCIe, USB
100 Ohm -> HDMI, Ethernet, MIPI (CSI, DSI)

Project: CM4 Module -> GPU card | Revision R1
Variant: FULL | RefDes: 100-199
Designer: M. Folejewski
File Name: [05] CM4_PART2.SchDoc | Printed:

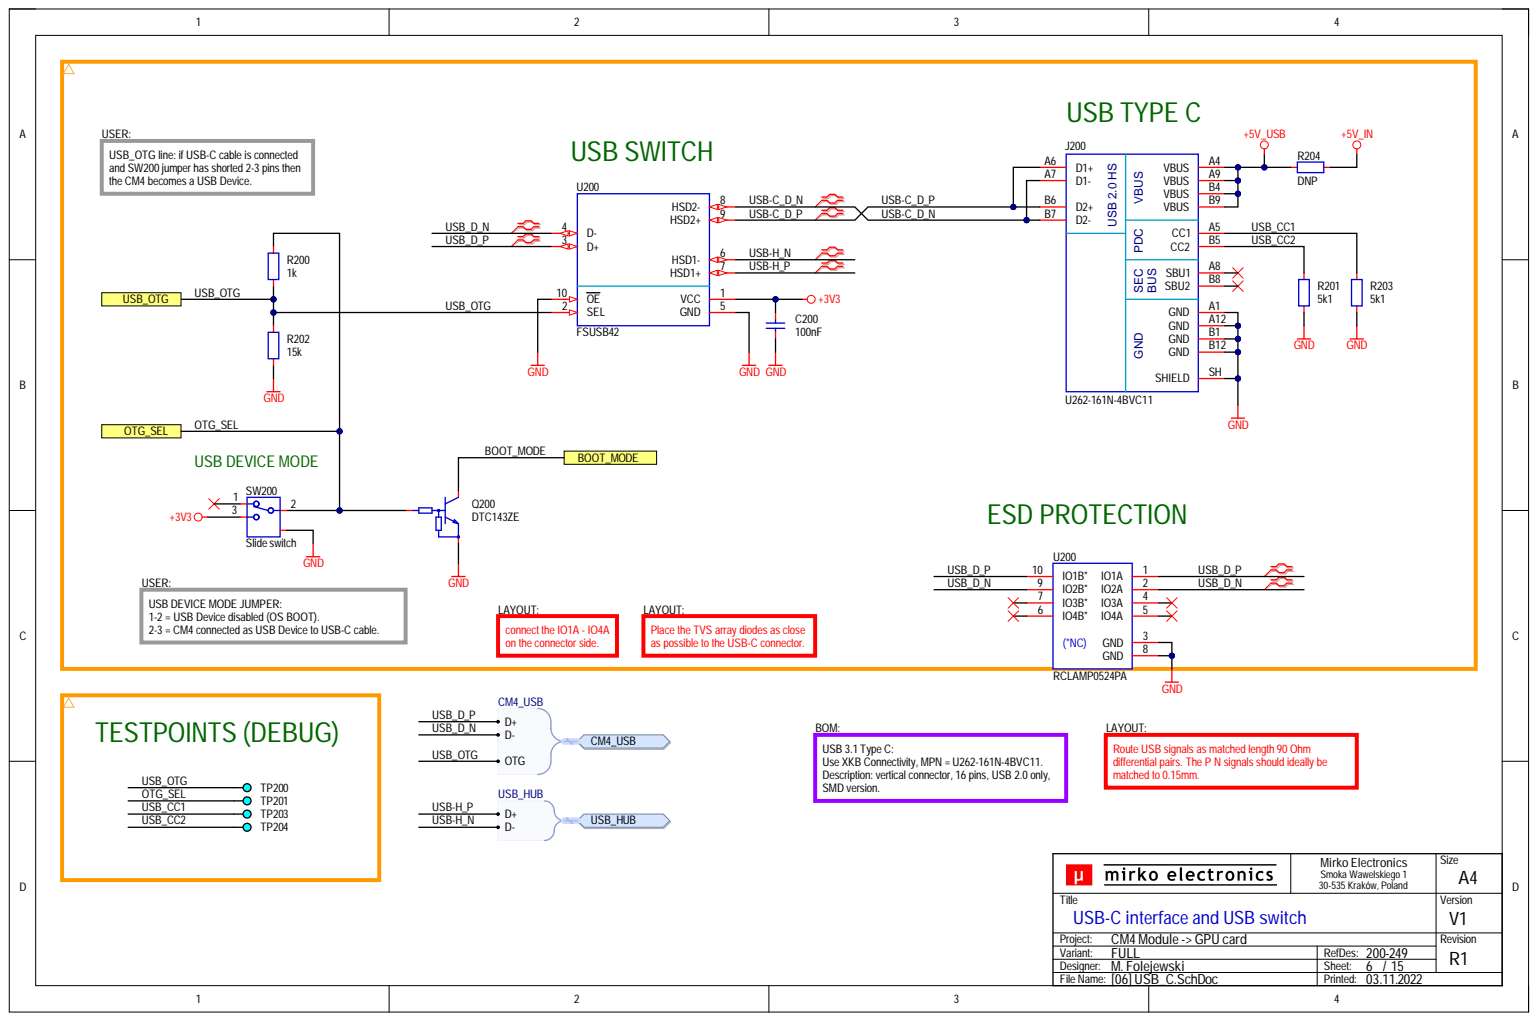
[picture p230: page 6]

USER:
USB_OTG line: if USB-C cable is connected
and SW200 jumper has shorted 2-3 pins then
the CM4 becomes a USB Device.

GND VBUS PDC SEC

USB DEVICE MODE JUMPER:
1-2 = USB Device disabled (OS BOOT).
2-3 = CM4 connected as USB Device to USB-C cable.

connect the IO1A - IO4A
on the connector side.

Place the TVS array diodes as close
as possible to the USB-C connector.

BOM:
USB 3.1 Type C:
Use XKB Connectivity, MPN = U262-161N-4BVC11.
Description: vertical connector, 16 pins, USB 2.0 only,
SMD version.

LAYOUT:
Route USB signals as matched length 90 Ohm
differential pairs. The P N signals should ideally be
matched to 0.15mm.

Mirko Electronics Smoka Wawelskiego 1 30-535 Kraków, Poland | Size A4

Title USB-C interface and USB switch | | Version V1

Project: CM4 Module -> GPU card | | Revision R1
Variant: FULL | RefDes: 200-249

File Name: [06] USB_C.SchDoc | Printed:

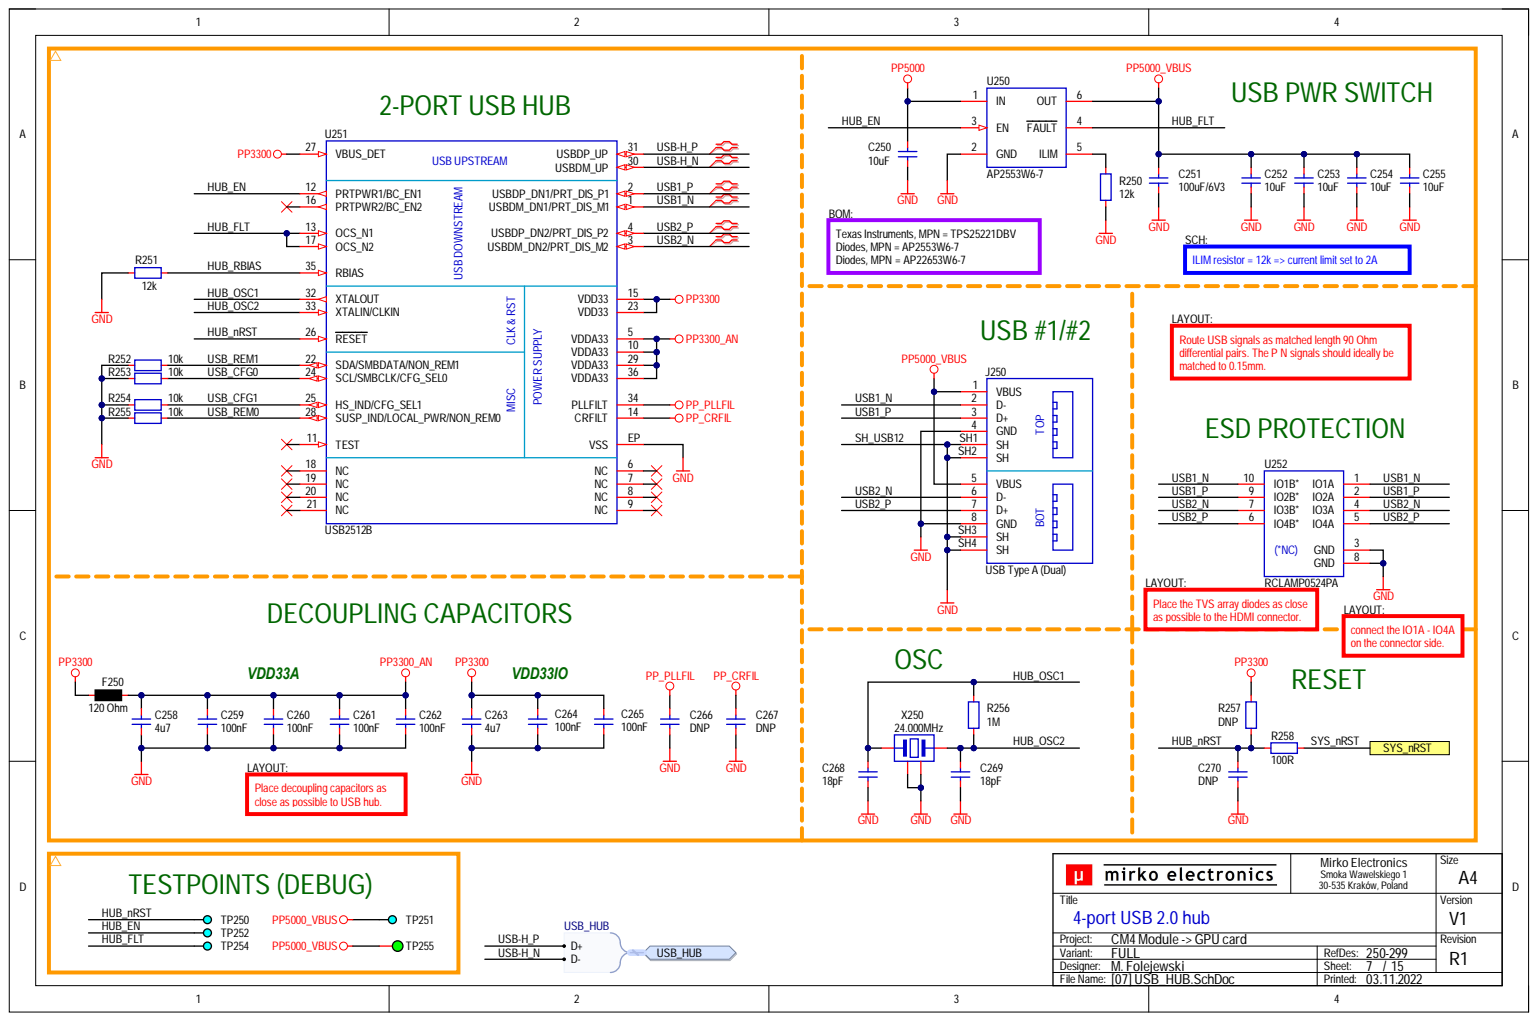
[picture p231: page 7]

SCH:
ILIM resistor = 12k => current limit set to 2A

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

D+ 3 D- 2 GND 4

Place the TVS array diodes as close
as possible to the HDMI connector.

Place decoupling capacitors as
close as possible to USB hub.

Mirko Electronics Smoka Wawelskiego 1

File Name: [07] USB_HUB.SchDoc | Printed:

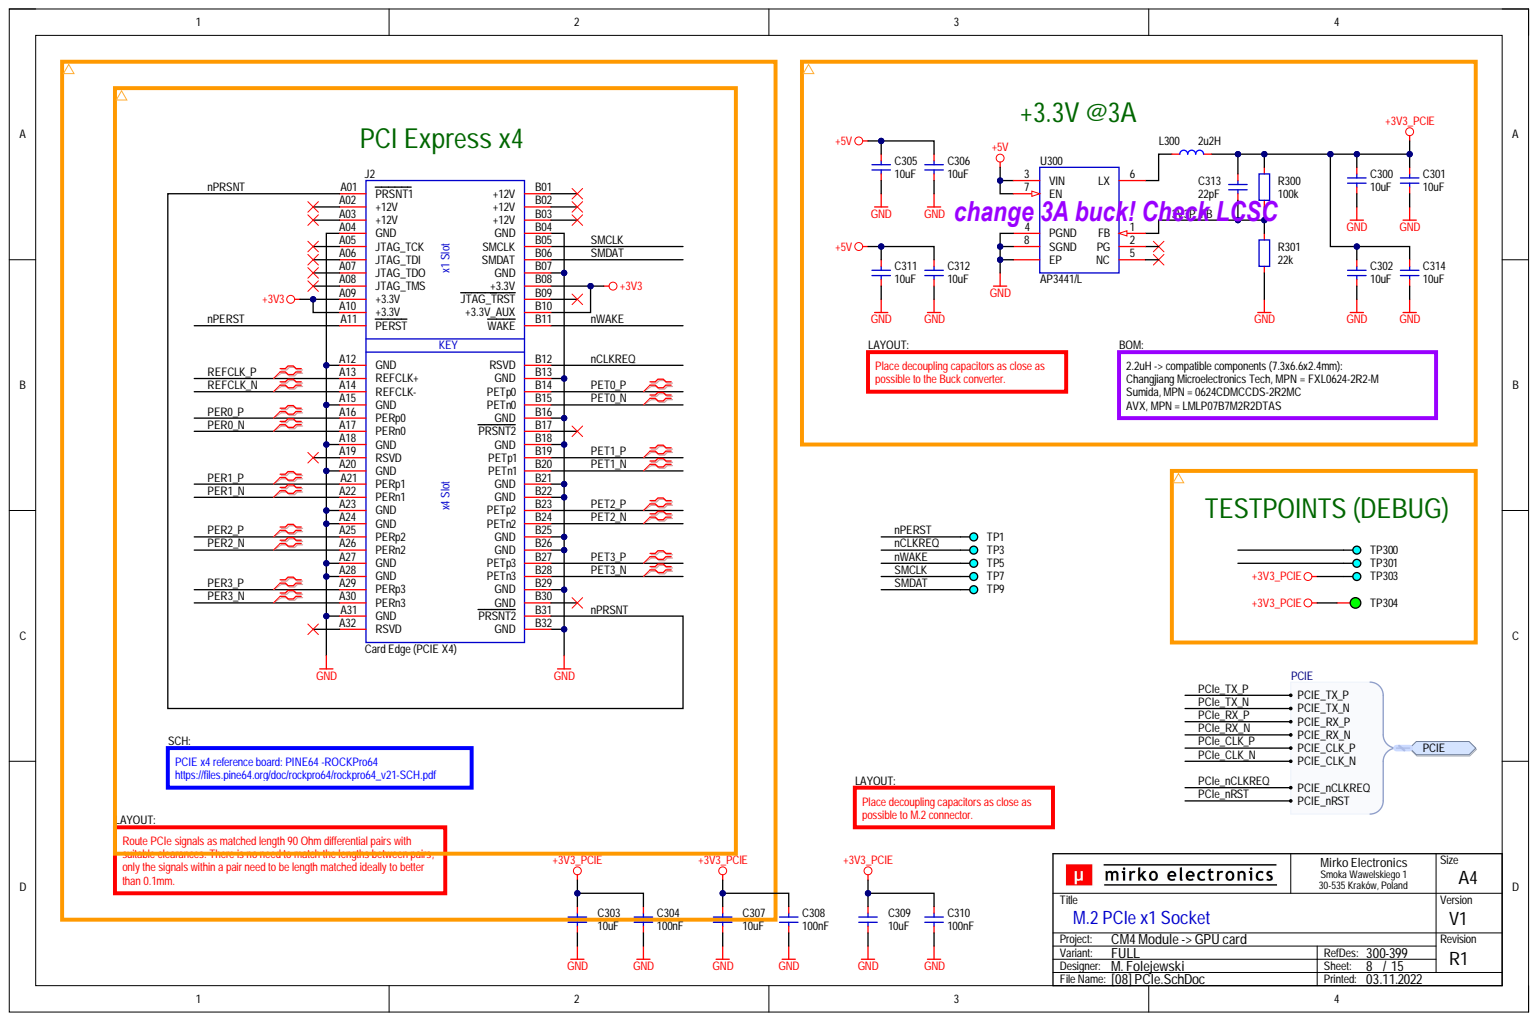
[picture p232: page 8]

LAYOU
Place decoupling ca
possible to the Buck converter.

pacitors as close as

SCH
PCIE x4 reference boa
https://files.pine64.org/doc/rockpro64/rockpro64_v21

Route PCIe signals as matched le
suita
only the signals within a pair need to be le
tha

here is no need to match the le

ngth matched ideally to better

Titl e M.2 PCIe x1 Socket | Ve rsion V1

Project: CM4 Module -> G PU card | Revision
nt: FUL L R1 Va ria | 300-399 RefDes:
Designer: M. Folejews k i | Sheet: 8 / 1 5
File Na me: [08] PCIe.S ch Doc | Printed : 03.1 1 . 2022

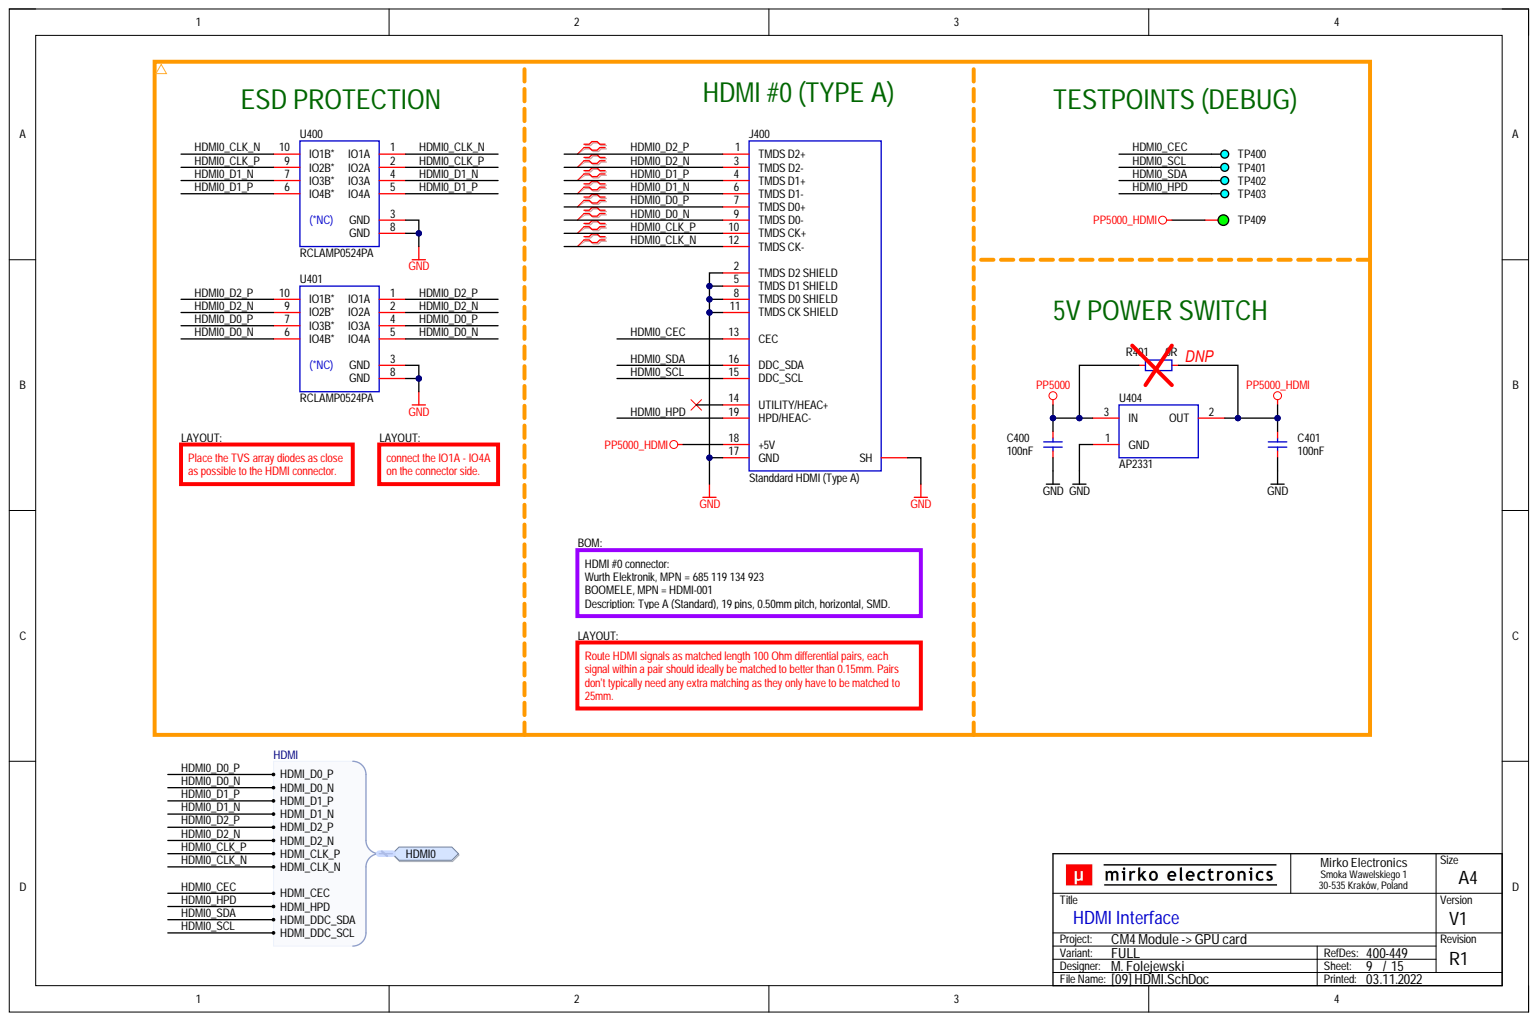
[picture p233: page 9]

Place the TVS array diodes as close
as possible to the HDMI connector.

connect the IO1A - IO4A
on the connector side.

BOM:
HDMI #0 connector:
Wurth Elektronik, MPN = 685 119 134 923
BOOMELE, MPN = HDMI-001
Description: Type A (Standard), 19 pins, 0.50mm pitch, horizontal, SMD.

LAYOUT:
Route HDMI signals as matched length 100 Ohm differential pairs, each
signal within a pair should ideally be matched to better than 0.15mm. Pairs
don’t typically need any extra matching as they only have to be matched to

Mirko Electronics Smoka Wawelskiego 1 30-535 Kraków, Poland | Size A4

Title HDMI Interface | | Version V1

Project: CM4 Module -> GPU card | | Revision R1
Variant: FULL | RefDes: 400-449

File Name: [09] HDMI.SchDoc | Printed:

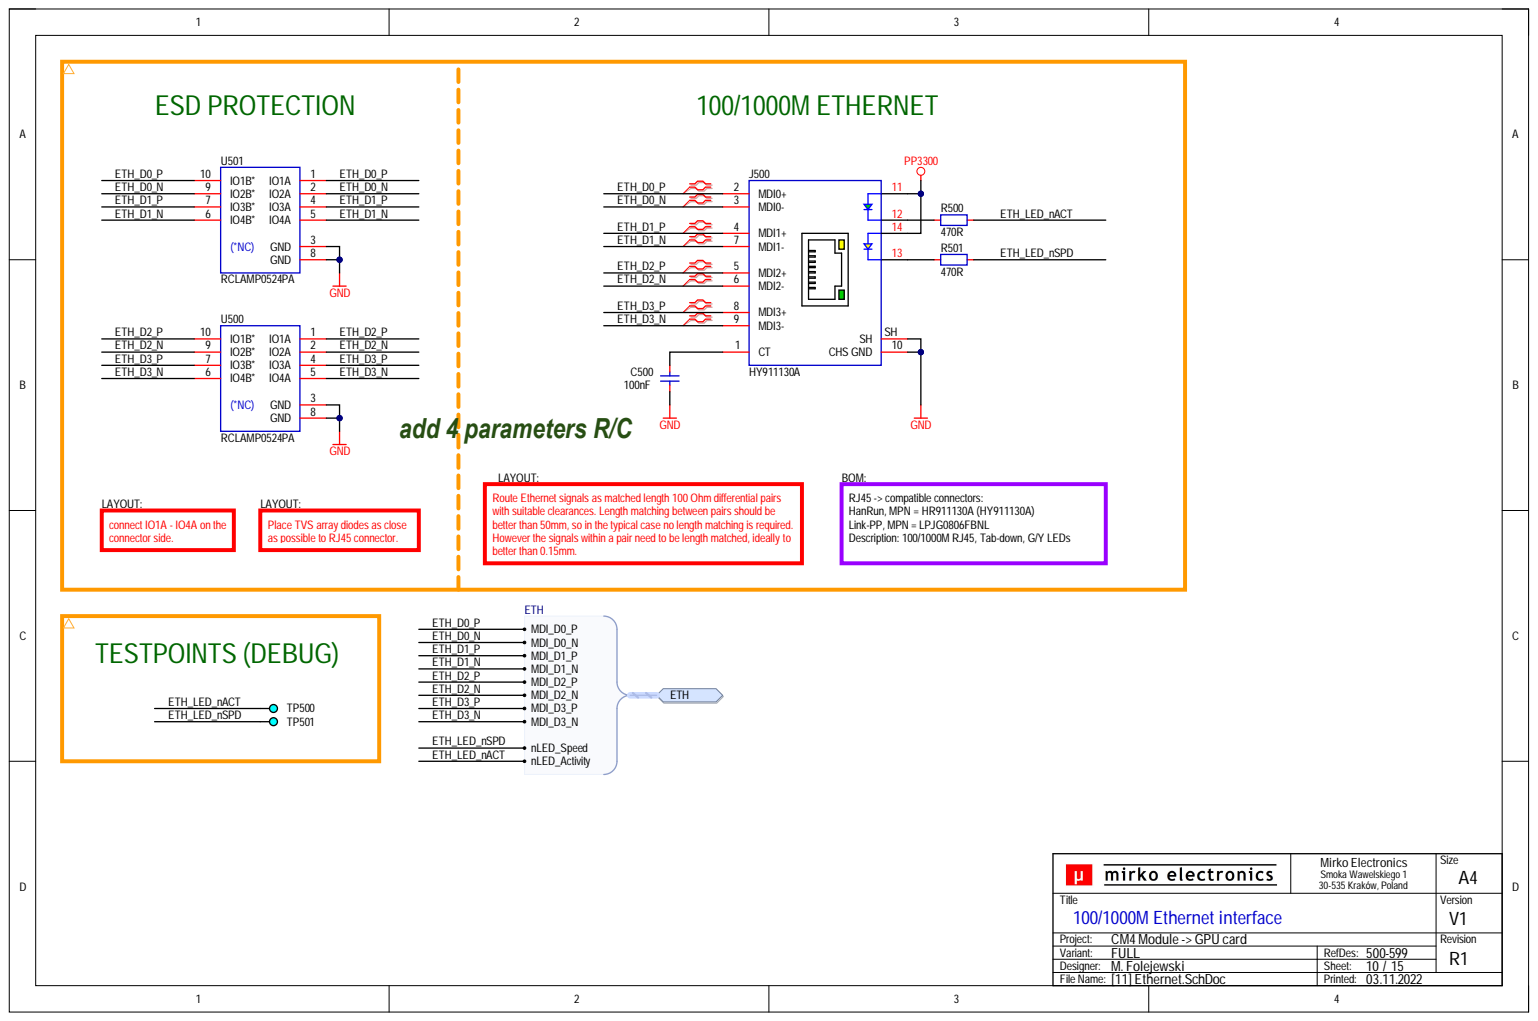
[picture p234: page 10]

LAYOUT:
Route Ethernet signals as matched length 100 Ohm differential pairs
with suitable clearances. Length matching between pairs should be
better than 50mm, so in the typical case no length matching is required.
However the signals within a pair need to be length matched, ideally to
better than 0.15mm.

BOM:
RJ45 -> compatible connectors:
HanRun, MPN = HR911130A (HY911130A)
Link-PP, MPN = LPJG0806FBNL
Description: 100/1000M RJ45, Tab-down, G/Y LEDs

Place TVS array diodes as close
as possible to RJ45 connector.

Mirko Electronics Smoka Wawelskiego 1 30-535 Kraków, Poland | Size A4

Title 100/1000M Ethernet interface | | Version V1

Project: CM4 Module -> GPU card | | Revision R1
Variant: FULL | RefDes: 500-599

File Name: [11] Ethernet.SchDoc | Printed:

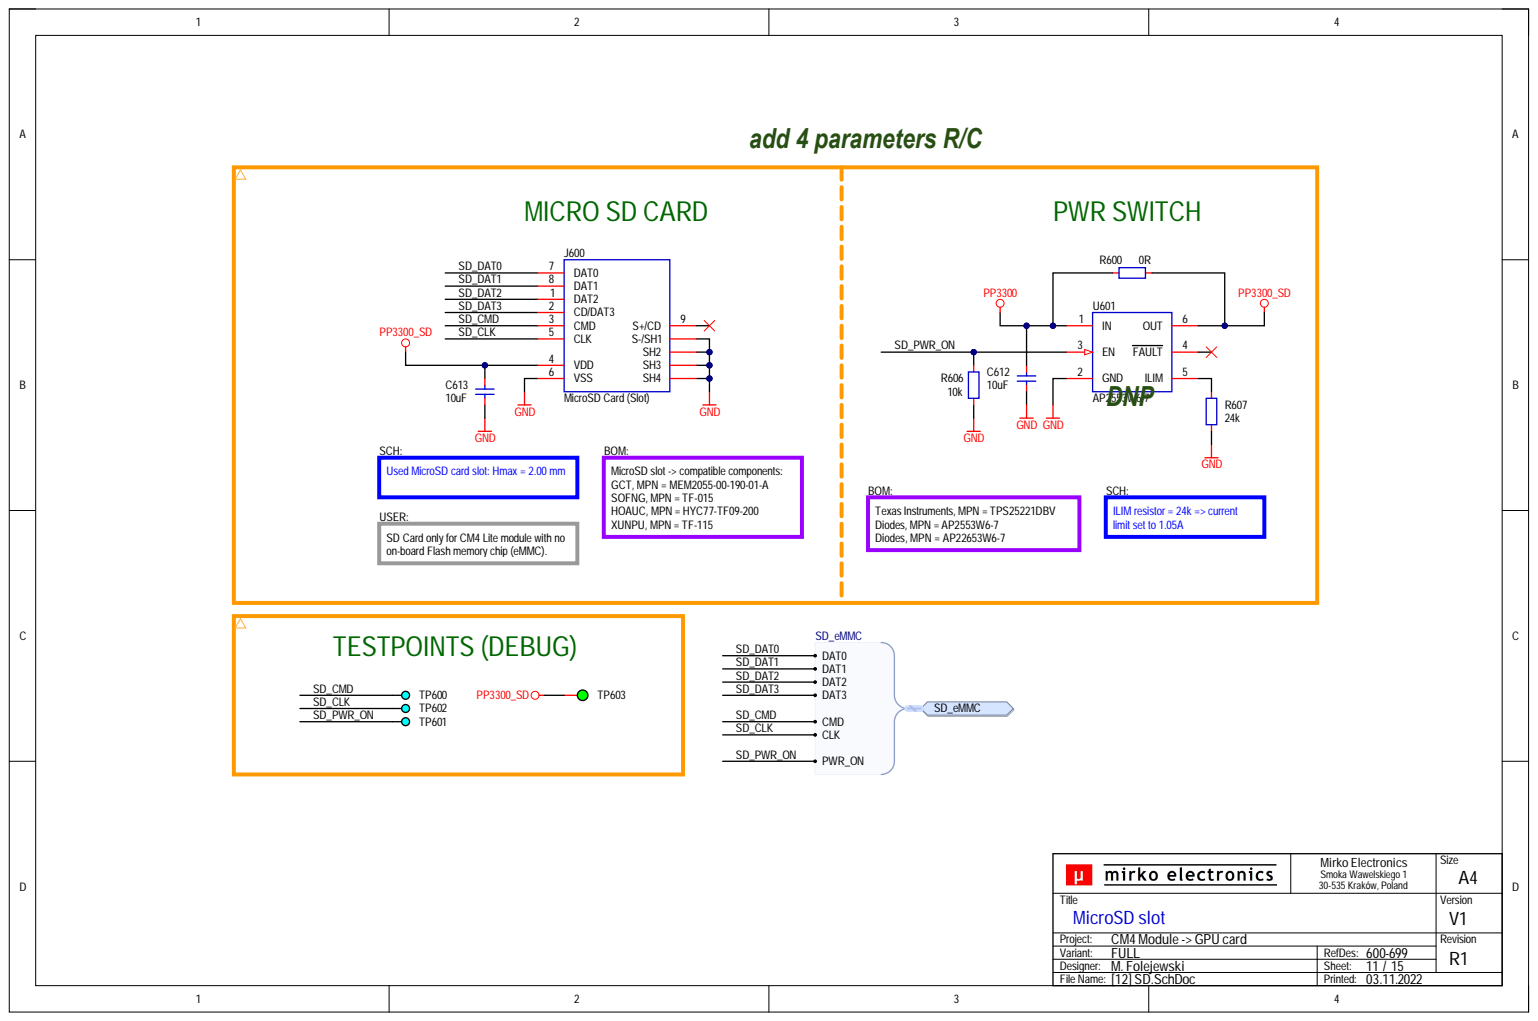
[picture p235: page 11]

SCH:
Used MicroSD card slot: Hmax = 2.00 mm

BOM:
MicroSD slot -> compatible components:
GCT, MPN = MEM2055-00-190-01-A
SOFNG, MPN = TF-015
HOAUC, MPN = HYC77-TF09-200
XUNPU, MPN = TF-115

USER:
SD Card only for CM4 Lite module with no
on-board Flash memory chip (eMMC).

Mirko Electronics Smoka Wawelskiego 1 30-535 Kraków, Poland | Size A4

Title MicroSD slot | | Version V1

Project: CM4 Module -> GPU card | | Revision R1
Variant: FULL | RefDes: 600-699

File Name: [12] SD.SchDoc | Printed:

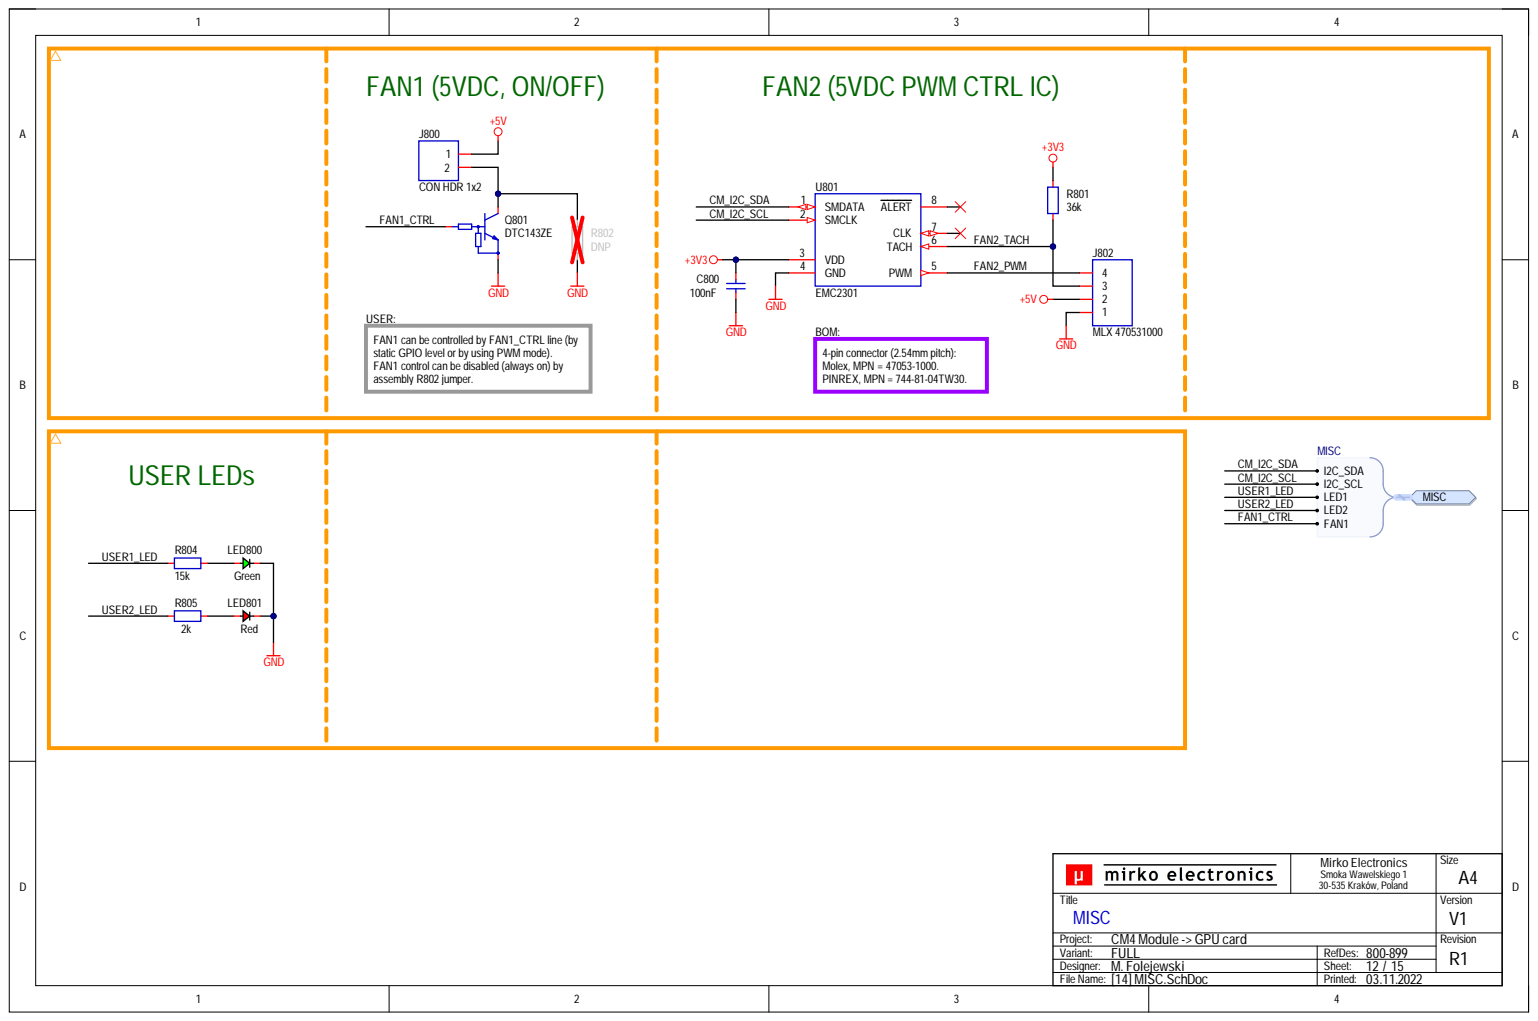
[picture p236: page 12]

USER:
FAN1 can be controlled by FAN1_CTRL line (by
static GPIO level or by using PWM mode).
FAN1 control can be disabled (always on) by
assembly R802 jumper.

Mirko Electronics Smoka Wawelskiego 1 30-535 Kraków, Poland | Size A4

Title MISC | | Version V1

Project: CM4 Module -> GPU card | | Revision R1
Variant: FULL | RefDes: 800-899

File Name: [14] MISC.SchDoc | Printed:

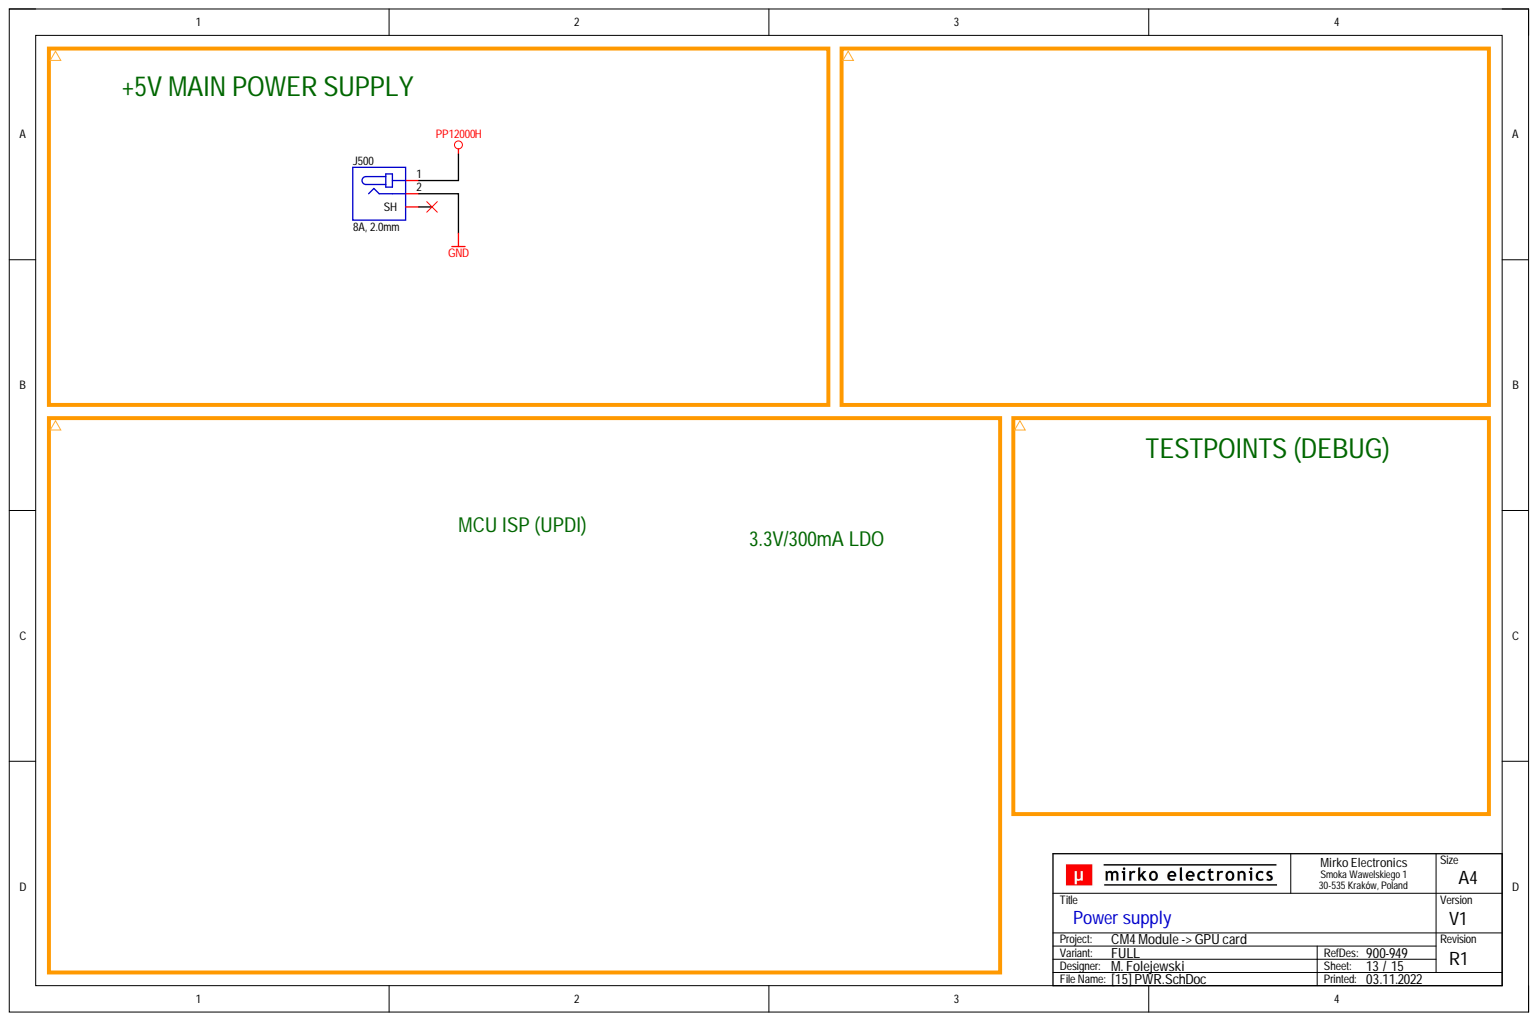
[picture p237: page 13]

3.3V/300mA LDO MCU ISP (UPDI)

Mirko Electronics Smoka Wawelskiego 1 30-535 Kraków, Poland | Size A4

Title Power supply | | Version V1

Project: CM4 Module -> GPU card | | Revision R1
Variant: FULL | RefDes: 900-949

File Name: [15] PWR.SchDoc | Printed:

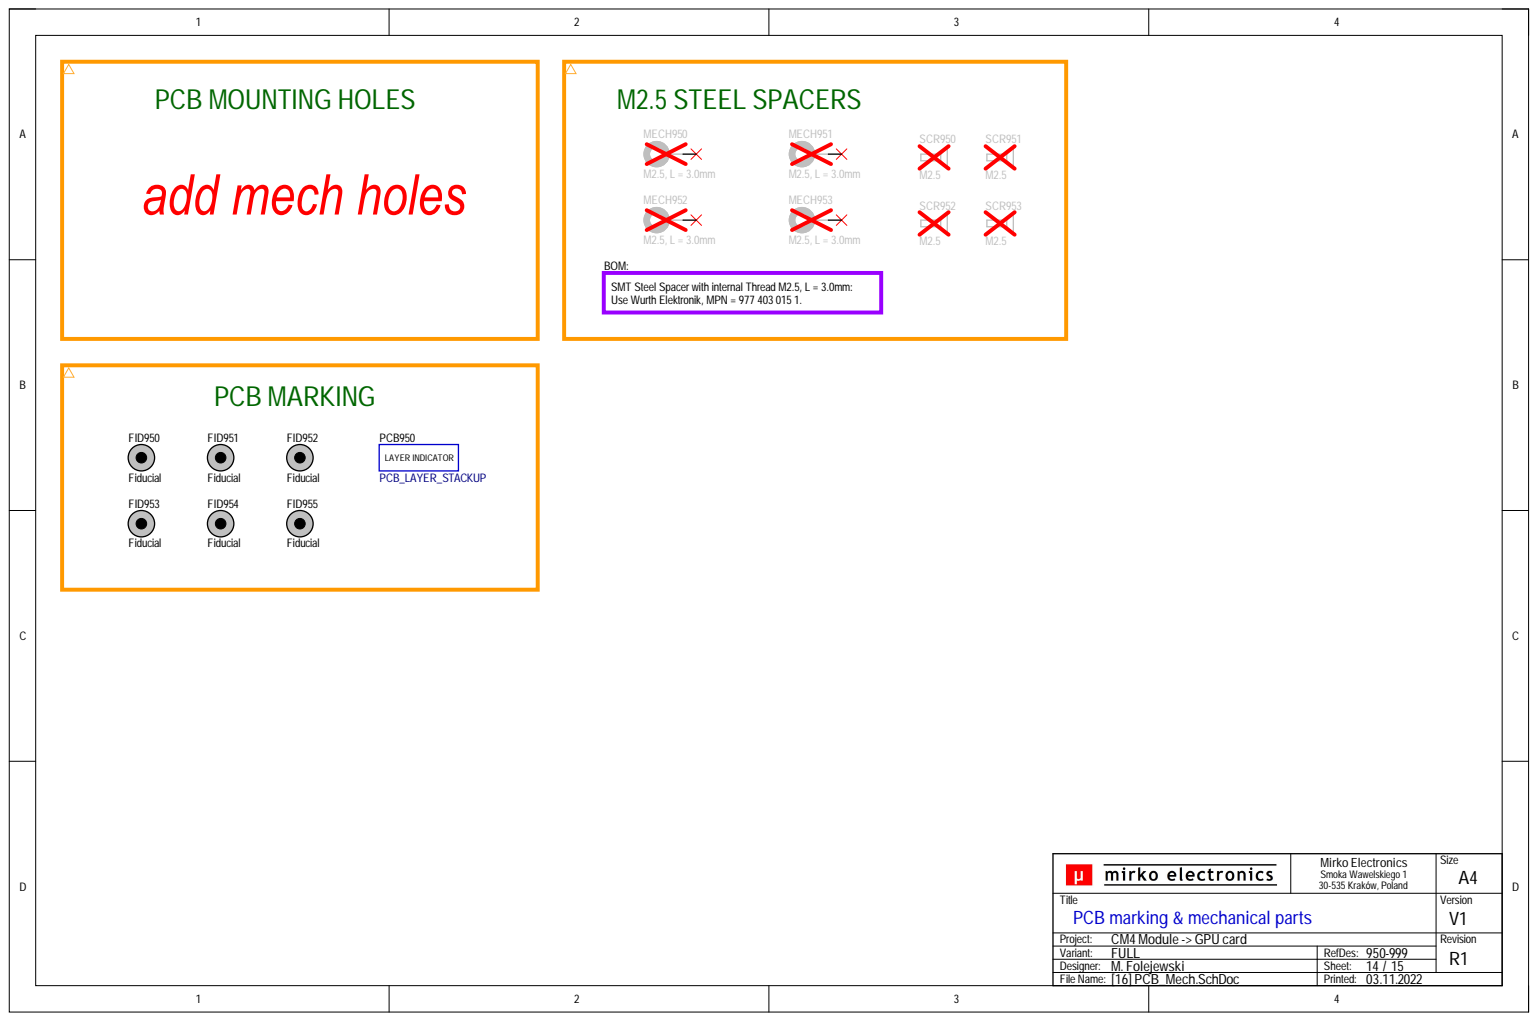
[picture p238: page 14]

BOM:
SMT Steel Spacer with internal Thread M2.5, L = 3.0mm:
Use Wurth Elektronik, MPN = 977 403 015 1.

Mirko Electronics Smoka Wawelskiego 1 30-535 Kraków, Poland | Size A4

Title PCB marking & mechanical parts | | Version V1

Project: CM4 Module -> GPU card | | Revision R1
Variant: FULL | RefDes: 950-999

File Name: [16] PCB_Mech.SchDoc | Printed:

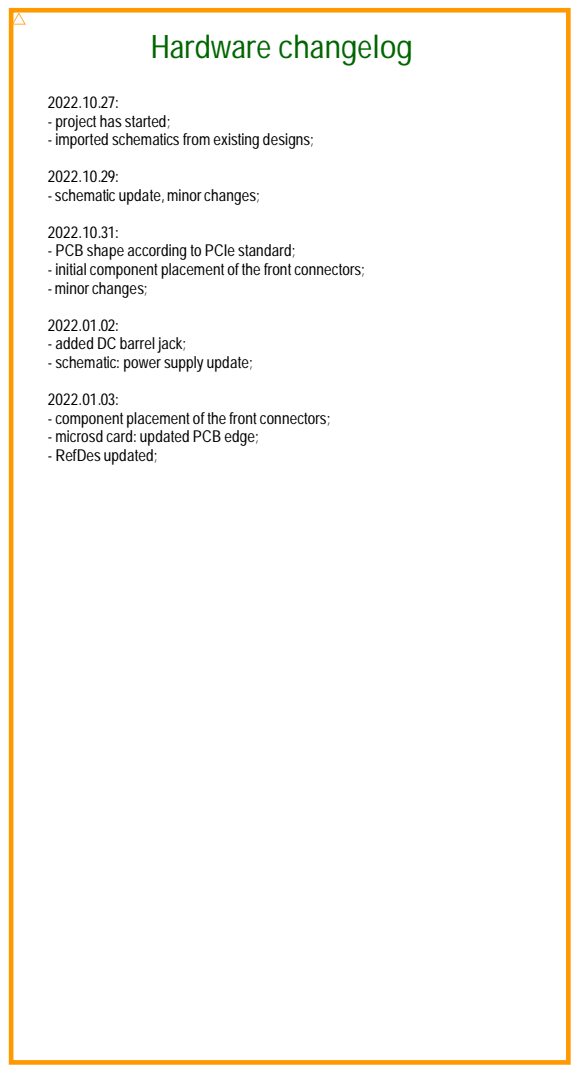
[picture p239: page 15]

- project has started;
- imported schematics from existing designs;

- schematic update, minor changes;

- PCB shape according to PCIe standard;
- initial component placement of the front connectors;
- minor changes;

- added DC barrel jack;
- schematic: power supply update;

- component placement of the front connectors;
- microsd card: updated PCB edge;
- RefDes updated;

Mirko Electronics Smoka Wawelskiego 1 30-535 Kraków, Poland | Size A4

Title Hardware changelog | | Version V1

Revision R1
Variant: FULL

File Name: [17] Changelog.SchDoc | Printed:
